juarendra/PocketMarauder/firmware/esp32_marauder/MenuFunctions.cpp

#include "MenuFunctions.h"
#include "MenuMarquee.h"
#include "CommandLine.h"
#include "OwnedListLifecycle.h"
#include "lang_var.h"

#ifdef HAS_SCREEN

extern const unsigned char menu_icons[][66];
extern LinkedList<AccessPoint>* access_points;
extern LinkedList<Station>* stations;
extern LinkedList<AirTag>* airtags;
extern LinkedList<Flipper>* flippers;
extern LinkedList<BleDevice>* ble_devices;
extern CommandLine cli_obj;

namespace {
bool parseGeofenceNumber(const String& value, double& parsed) {
  char* end = nullptr;
  parsed = strtod(value.c_str(), &end);
  return end != value.c_str() && *end == '\0' && isfinite(parsed);
}
}

#ifdef HAS_MINI_SCREEN
void MenuFunctions::drawMiniMenuButton(int b, int x, bool selected, uint16_t text_offset) {
  if (!current_menu || !current_menu->list || x < 0 || x >= current_menu->list->size())
    return;

  MenuNode mini_node = current_menu->list->get(x);
  bool is_setting_node = (mini_node.icon == SETTINGS && mini_node.color == TFTLIGHTGREY);
  uint16_t color = is_setting_node ? (mini_node.selected ? TFT_GREEN : TFT_RED) : this->getColor(mini_node.color);
  int16_t button_x = KEY_X - (KEY_W / 2);
  int16_t button_y = (KEY_Y + (b * (KEY_H + KEY_SPACING_Y))) - (KEY_H / 2);

  uint16_t background = selected ? (is_setting_node ? TFT_LIGHTGREY : color) : TFT_BLACK;
  uint16_t text_color = (selected && !is_setting_node) ? TFT_BLACK : color;

  display_obj.tft.setFreeFont(NULL);
  display_obj.tft.setTextSize(1);
  display_obj.tft.setTextWrap(false);
  display_obj.tft.fillRect(button_x, button_y - 4, KEY_W, KEY_H, background);
  display_obj.tft.setTextColor(text_color, background);
  display_obj.tft.setCursor(button_x + BUTTON_PADDING, button_y + (KEY_H / 2) - 8);
  display_obj.tft.print(this->menuLabelWindow(current_menu->list->get(x).name, text_offset));
}
#endif

String MenuFunctions::menuLabelWindow(const String& name, uint16_t offset) {
  const int16_t available_width = max(1, KEY_W - (2 * BUTTON_PADDING));

  #ifdef HAS_MINI_SCREEN
    display_obj.tft.setFreeFont(NULL);
    display_obj.tft.setTextSize(1);
  #else
    display_obj.tft.setFreeFont(MENU_FONT);
    display_obj.tft.setTextSize(KEY_TEXTSIZE);
  #endif

  if (offset >= name.length())
    offset = 0;

  String visible = name.substring(offset);
  while (visible.length() > 1 && display_obj.tft.textWidth(visible) > available_width)
    visible.remove(visible.length() - 1);

  return visible;
}

uint16_t MenuFunctions::menuLabelMaxOffset(const String& name) {
  const int16_t available_width = max(1, KEY_W - (2 * BUTTON_PADDING));
  uint16_t max_offset = 0;

  #ifdef HAS_MINI_SCREEN
    display_obj.tft.setFreeFont(NULL);
    display_obj.tft.setTextSize(1);
  #else
    display_obj.tft.setFreeFont(MENU_FONT);
    display_obj.tft.setTextSize(KEY_TEXTSIZE);
  #endif

  if (display_obj.tft.textWidth(name) > available_width) {
    max_offset = name.length() > 0 ? name.length() - 1 : 0;
    for (uint16_t offset = 1; offset < name.length(); offset++) {
      if (display_obj.tft.textWidth(name.substring(offset)) <= available_width) {
        max_offset = offset;
        break;
      }
    }
  }

  #ifdef HAS_FULL_SCREEN
    display_obj.tft.setFreeFont(NULL);
  #endif

  return max_offset;
}

void MenuFunctions::updateMenuMarquee(uint32_t current_time) {
  const bool menu_visible = (wifi_scan_obj.currentScanMode == WIFI_SCAN_OFF) ||
                            (wifi_scan_obj.currentScanMode == WIFI_CONNECTED) ||
                            (wifi_scan_obj.currentScanMode == OTA_UPDATE);

  if (!menu_visible || !current_menu || !current_menu->list ||
      current_menu->list->size() == 0 || current_menu->selected >= current_menu->list->size()) {
    marquee_menu = nullptr;
    marquee_selected = 0xFFFF;
    marquee_rendered_offset = 0;
    marquee_max_offset = 0;
    return;
  }

  if (marquee_menu != current_menu || marquee_selected != current_menu->selected) {
    marquee_menu = current_menu;
    marquee_selected = current_menu->selected;
    marquee_selected_since = current_time;
    marquee_rendered_offset = 0;
    marquee_max_offset = this->menuLabelMaxOffset(
      current_menu->list->get(current_menu->selected).name
    );
    return;
  }

  const uint16_t next_offset = MenuMarquee::offsetForElapsed(
    current_time - marquee_selected_since,
    marquee_max_offset
  );

  if (next_offset == marquee_rendered_offset)
    return;

  marquee_rendered_offset = next_offset;
  this->buttonSelected(
    current_menu->selected - menu_start_index,
    current_menu->selected,
    marquee_rendered_offset
  );
}

void MenuFunctions::buttonNotSelected(int b, int x) {
  if (x == -1)
    x = b;

  // Ensure b is within valid button index range
  b = (x - menu_start_index) % BUTTON_SCREEN_LIMIT;

  #ifdef HAS_MINI_SCREEN
    this->drawMiniMenuButton(b, x, false);
  #endif

  uint16_t color = (current_menu->list->get(x).icon == SETTINGS && current_menu->list->get(x).color == TFTLIGHTGREY) ? (current_menu->list->get(x).selected ? TFT_GREEN : TFT_RED) : this->getColor(current_menu->list->get(x).color);
  uint16_t icon_color = (current_menu->list->get(x).icon == SETTINGS && current_menu->list->get(x).color == TFTLIGHTGREY) ? TFT_LIGHTGREY : color;

  #ifdef HAS_FULL_SCREEN
    display_obj.tft.setFreeFont(MENU_FONT);
    display_obj.key[b].initButton(&display_obj.tft, KEY_X, KEY_Y + b * (KEY_H + KEY_SPACING_Y), KEY_W, KEY_H, TFT_BLACK, TFT_BLACK, color, (char*)"", KEY_TEXTSIZE);
    display_obj.key[b].drawButton(false, this->menuLabelWindow(current_menu->list->get(x).name));
    if ((current_menu->list->get(x).name != text09) && (current_menu->list->get(x).icon != 255))
          display_obj.tft.drawXBitmap(0,
                                      KEY_Y + (b * (KEY_H + KEY_SPACING_Y)) - (ICON_H / 2),
                                      menu_icons[current_menu->list->get(x).icon],
                                      ICON_W,
                                      ICON_H,
                                      TFT_BLACK,
                                      icon_color);
    display_obj.tft.setFreeFont(NULL);
  #endif
}

void MenuFunctions::buttonSelected(int b, int x, uint16_t text_offset) {
  if (x == -1)
    x = b;

  // Ensure b is within valid button index range
  b = (x - menu_start_index) % BUTTON_SCREEN_LIMIT;

  uint16_t color = this->getColor(current_menu->list->get(x).color);

  #ifdef HAS_MINI_SCREEN
    this->drawMiniMenuButton(b, x, true, text_offset);
  #endif

  #ifdef HAS_FULL_SCREEN
    display_obj.tft.setFreeFont(MENU_FONT);
    if (current_menu->list->get(x).icon == SETTINGS && current_menu->list->get(x).color == TFTLIGHTGREY) {
      uint16_t setting_color = current_menu->list->get(x).selected ? TFT_GREEN : TFT_RED;
      display_obj.key[b].initButton(&display_obj.tft, KEY_X, KEY_Y + b * (KEY_H + KEY_SPACING_Y), KEY_W, KEY_H, TFT_BLACK, TFT_LIGHTGREY, setting_color, (char*)"", KEY_TEXTSIZE);
      display_obj.key[b].drawButton(false, this->menuLabelWindow(current_menu->list->get(x).name, text_offset));
      display_obj.tft.drawXBitmap(0,
                                      KEY_Y + (b * (KEY_H + KEY_SPACING_Y)) - (ICON_H / 2),
                                      menu_icons[current_menu->list->get(x).icon],
                                      ICON_W,
                                      ICON_H,
                                      TFT_BLACK,
                                      TFT_LIGHTGREY);
    } else {
      display_obj.key[b].drawButton(true, this->menuLabelWindow(current_menu->list->get(x).name, text_offset));
      if ((current_menu->list->get(x).name != text09) && (current_menu->list->get(x).icon != 255))
            display_obj.tft.drawXBitmap(0,
                                        KEY_Y + (b * (KEY_H + KEY_SPACING_Y)) - (ICON_H / 2),
                                        menu_icons[current_menu->list->get(x).icon],
                                        ICON_W,
                                        ICON_H,
                                        TFT_BLACK,
                                        color);
    }
    display_obj.tft.setFreeFont(NULL);
  #endif
}

void MenuFunctions::displayMenuButtons() {
  #ifdef HAS_ILI9341
    // Draw lines to show each menu button
    for (int i = 0; i < 3; i++) {

      // Draw horizontal line on left
      display_obj.tft.drawLine(0, 
                              TFT_HEIGHT / 3 * (i),
                              (TFT_WIDTH / 12) / 2,
                              TFT_HEIGHT / 3 * (i),
                              TFT_FARTGRAY);

      // Draw horizontal line on right
      display_obj.tft.drawLine(TFT_WIDTH - 1 - ((TFT_WIDTH / 12) / 2), 
                              TFT_HEIGHT / 3 * (i),
                              TFT_WIDTH,
                              TFT_HEIGHT / 3 * (i),
                              TFT_FARTGRAY);

      // Draw vertical line on left
      display_obj.tft.drawLine(0, 
                              (TFT_HEIGHT / 3 * (i)) - ((TFT_WIDTH / 12) / 2),
                              0,
                              (TFT_HEIGHT / 3 * (i)) + ((TFT_WIDTH / 12) / 2),
                              TFT_FARTGRAY);

      // Draw vertical line on right
      display_obj.tft.drawLine(TFT_WIDTH - 1, 
                              (TFT_HEIGHT / 3 * (i)) - ((TFT_WIDTH / 12) / 2),
                              TFT_WIDTH - 1,
                              (TFT_HEIGHT / 3 * (i)) + ((TFT_WIDTH / 12) / 2),
                              TFT_FARTGRAY);
    }
  #endif
}

// Function to check menu input
void MenuFunctions::main(uint32_t currentTime)
{
  #ifdef HAS_MINI_SCREEN
    if (geofenceMenuRefreshPending) {
      geofenceMenuRefreshPending = false;
      this->buildGeofenceMenu();
    }
  #endif
  #ifdef HAS_SD
    if (sd_browser_release_pending && current_menu != &sdDeleteMenu)
      this->releaseSDDeleteBrowserResources();
  #endif
  if (saved_wifi_release_pending && current_menu != &savedWifiMenu) {
    this->releaseSavedWifiMenu();
    saved_wifi_release_pending = false;
  }

  #if defined(MARAUDER_CARDPUTER) || defined(MARAUDER_CARDPUTER_ADV)
    this->updateKeyboard();
  #endif

  // Some function exited and we need to go back to normal
  if (display_obj.exit_draw) {
    if (wifi_scan_obj.currentScanMode != WIFI_CONNECTED)
      wifi_scan_obj.currentScanMode = WIFI_SCAN_OFF;
    display_obj.exit_draw = false;
    this->orientDisplay();
  }
  if ((wifi_scan_obj.currentScanMode == WIFI_SCAN_OFF) ||
      (wifi_scan_obj.currentScanMode == WIFI_CONNECTED) ||
      (wifi_scan_obj.currentScanMode == OTA_UPDATE) ||
      (wifi_scan_obj.currentScanMode == ESP_UPDATE) ||
      (wifi_scan_obj.currentScanMode == SHOW_INFO) ||
      (wifi_scan_obj.currentScanMode == WIFI_SCAN_GPS_DATA) ||
      (wifi_scan_obj.currentScanMode == GPS_POI) ||
      (wifi_scan_obj.currentScanMode == GPS_TRACKER) ||
      (wifi_scan_obj.currentScanMode == WIFI_SCAN_GPS_NMEA)) {
    if (wifi_scan_obj.orient_display) {
      this->orientDisplay();
      wifi_scan_obj.orient_display = false;
    }
  }

  if (currentTime != 0) {
    if (currentTime - initTime >= BANNER_TIME) {
      this->initTime = millis();
      if ((wifi_scan_obj.currentScanMode != LV_JOIN_WIFI) &&
          (wifi_scan_obj.currentScanMode != LV_ADD_SSID) && (wifi_scan_obj.currentScanMode != WIFI_PACKET_MONITOR)) // GCOVR_EXCL_LINE -- Packet Monitor owns its full hardware display.
        this->updateStatusBar();
      
      // Do channel analyzer stuff
      if ((wifi_scan_obj.currentScanMode == WIFI_SCAN_CHAN_ANALYZER) ||
          (wifi_scan_obj.currentScanMode == BT_SCAN_ANALYZER)){
        #ifdef HAS_SCREEN
          this->setGraphScale(this->graphScaleCheck(wifi_scan_obj._analyzer_values));

          this->drawGraph(wifi_scan_obj._analyzer_values);
        #endif
      }

      if (wifi_scan_obj.currentScanMode == WIFI_SCAN_CHAN_ACT) {
        #ifdef HAS_SCREEN
          this->setGraphScale(this->graphScaleCheckSmall(wifi_scan_obj.channel_activity));

          this->drawGraphSmall(wifi_scan_obj.channel_activity);

        #endif
      }
    }
  }

  this->updateMenuMarquee(currentTime);


  boolean pressed = false;
  // This is code from bodmer's keypad example
  uint16_t t_x = 0, t_y = 0; // To store the touch coordinates

  // Get the display buffer out of the way
  if ((wifi_scan_obj.currentScanMode != WIFI_SCAN_OFF ) &&
      (wifi_scan_obj.currentScanMode != WIFI_CONNECTED) &&
      (wifi_scan_obj.currentScanMode != WIFI_ATTACK_BEACON_SPAM) &&
      (wifi_scan_obj.currentScanMode != WIFI_ATTACK_AP_SPAM) &&
      (wifi_scan_obj.currentScanMode != WIFI_ATTACK_CSA) &&
      (wifi_scan_obj.currentScanMode != WIFI_ATTACK_QUIET) &&
      (wifi_scan_obj.currentScanMode != WIFI_ATTACK_AUTH) &&
      (wifi_scan_obj.currentScanMode != WIFI_ATTACK_DEAUTH) &&
      (wifi_scan_obj.currentScanMode != WIFI_ATTACK_DEAUTH_MANUAL) &&
      (wifi_scan_obj.currentScanMode != WIFI_ATTACK_DEAUTH_TARGETED) &&
      (wifi_scan_obj.currentScanMode != WIFI_ATTACK_BAD_MSG_TARGETED) &&
      (wifi_scan_obj.currentScanMode != WIFI_ATTACK_BAD_MSG) &&
      (wifi_scan_obj.currentScanMode != WIFI_ATTACK_SLEEP) &&
      (wifi_scan_obj.currentScanMode != WIFI_ATTACK_SLEEP_TARGETED) &&
      (wifi_scan_obj.currentScanMode != WIFI_ATTACK_MIMIC) &&
	  (wifi_scan_obj.currentScanMode != WIFI_ATTACK_FUNNY_BEACON) &&
      (wifi_scan_obj.currentScanMode != WIFI_ATTACK_RICK_ROLL))
    display_obj.displayBuffer();


  int pre_getTouch = millis();

  #ifdef HAS_ILI9341
    if (!this->disable_touch)
      pressed = display_obj.updateTouch(&t_x, &t_y);
  #endif


  // Brightness gesture: hold top or bottom zone 1.5s to enter brightness mode
  #ifdef HAS_ILI9341
    bool touching_menu_control = false;
    if (pressed) {
      for (uint8_t b = BUTTON_ARRAY_LEN; b < BUTTON_ARRAY_LEN + 3; b++) {
        if (display_obj.key[b].contains(t_x, t_y)) {
          touching_menu_control = true;
          break;
        }
      }
    }
    if (pressed && !touching_menu_control &&
        (wifi_scan_obj.currentScanMode == WIFI_SCAN_OFF ||
                    wifi_scan_obj.currentScanMode == WIFI_CONNECTED)) {
      uint16_t zoneUp = TFT_HEIGHT * 25 / 100;
      uint16_t zoneDown = TFT_HEIGHT * 75 / 100;
      if (t_y < zoneUp || t_y >= zoneDown) {
        uint32_t hold_start = millis();
        uint16_t hx, hy;
        bool held = false;
        while (display_obj.updateTouch(&hx, &hy)) {
          if (millis() - hold_start >= 1500) {
            held = true;
            break;
          }
          delay(10);
        }
        if (held) {
          // Wait for release before entering brightness mode
          while (display_obj.updateTouch(&hx, &hy)) delay(10);
          this->brightnessMode();
          return;
        }
      }
    }
  #endif

  // POI button interception during wardrive — full width bottom bar
  #ifdef HAS_ILI9341
    if (pressed &&
        (wifi_scan_obj.currentScanMode == WIFI_SCAN_WAR_DRIVE ||
         wifi_scan_obj.currentScanMode == WIFI_SCAN_STATION_WAR_DRIVE)) {
      if (t_y >= (SCREEN_HEIGHT - 50)) {
        wifi_scan_obj.tagPOI(nullptr);
        // Brief green flash
        display_obj.tft.fillRect(0, SCREEN_HEIGHT - 50, SCREEN_WIDTH, 50, TFT_GREEN);
        display_obj.tft.setTextSize(2);
        #ifdef HAS_GPS
        if (gps_obj.getFixStatus())
          display_obj.tft.setTextColor(TFT_BLACK, TFT_GREEN);
        else
        #endif
          display_obj.tft.setTextColor(TFT_BLACK, TFT_RED);
        String poiFlash = "POI (" + String(wifi_scan_obj.poiCount) + ")";
        int16_t flashWidth = poiFlash.length() * 12;
        display_obj.tft.setCursor((SCREEN_WIDTH - flashWidth) / 2, SCREEN_HEIGHT - 33);
        display_obj.tft.print(poiFlash);
        delay(200);
        x = -1;
        y = -1;
        return;
      }
    }
  #endif

  // This is if there are scans/attacks going on
  #ifdef HAS_ILI9341
    if ((wifi_scan_obj.currentScanMode != WIFI_SCAN_OFF) &&
        (pressed) &&
        (wifi_scan_obj.currentScanMode != WIFI_CONNECTED) &&
        (wifi_scan_obj.currentScanMode != OTA_UPDATE) &&
        (wifi_scan_obj.currentScanMode != ESP_UPDATE) &&
        (wifi_scan_obj.currentScanMode != SHOW_INFO) &&
        (wifi_scan_obj.currentScanMode != WIFI_SCAN_GPS_DATA) &&
        (wifi_scan_obj.currentScanMode != GPS_POI) &&
        (wifi_scan_obj.currentScanMode != GPS_TRACKER) &&
        (wifi_scan_obj.currentScanMode != WIFI_SCAN_GPS_NMEA))
    {
      // Stop the current scan
      if ((wifi_scan_obj.currentScanMode == WIFI_SCAN_SAE_COMMIT) ||
          (wifi_scan_obj.currentScanMode == WIFI_SCAN_DETECT_FOLLOW) ||
          (wifi_scan_obj.currentScanMode == WIFI_SCAN_STATION_WAR_DRIVE) ||
          (wifi_scan_obj.currentScanMode == WIFI_SCAN_STATION) ||
          (wifi_scan_obj.currentScanMode == WIFI_SCAN_WAR_DRIVE) ||
          (wifi_scan_obj.currentScanMode == WIFI_SCAN_DISPLAY_AP_INFO) ||
          (wifi_scan_obj.currentScanMode == WIFI_SCAN_EVIL_PORTAL) ||
          (wifi_scan_obj.currentScanMode == WIFI_SCAN_AP_STA) ||
          (wifi_scan_obj.currentScanMode == WIFI_PING_SCAN) ||
          (wifi_scan_obj.currentScanMode == WIFI_ARP_SCAN) ||
          (wifi_scan_obj.currentScanMode == WIFI_PORT_SCAN_ALL) ||
          (wifi_scan_obj.currentScanMode == WIFI_SCAN_SSH) ||
          (wifi_scan_obj.currentScanMode == WIFI_SCAN_TELNET) ||
          (wifi_scan_obj.currentScanMode == WIFI_SCAN_DNS) ||
          (wifi_scan_obj.currentScanMode == WIFI_SCAN_SMTP) ||
          (wifi_scan_obj.currentScanMode == WIFI_SCAN_HTTP) ||
          (wifi_scan_obj.currentScanMode == WIFI_SCAN_HTTPS) ||
          (wifi_scan_obj.currentScanMode == WIFI_SCAN_RDP) ||
          (wifi_scan_obj.currentScanMode == WIFI_SCAN_PWN) ||
          (wifi_scan_obj.currentScanMode == WIFI_SCAN_PINESCAN) ||
          (wifi_scan_obj.currentScanMode == WIFI_SCAN_MULTISSID) ||
          (wifi_scan_obj.currentScanMode == WIFI_SCAN_ESPRESSIF) ||
          (wifi_scan_obj.currentScanMode == WIFI_SCAN_ALL) ||
          (wifi_scan_obj.currentScanMode == WIFI_ATTACK_BEACON_SPAM) ||
          (wifi_scan_obj.currentScanMode == WIFI_ATTACK_AP_SPAM) ||
          (wifi_scan_obj.currentScanMode == WIFI_ATTACK_CSA) ||
          (wifi_scan_obj.currentScanMode == WIFI_ATTACK_QUIET) ||
          (wifi_scan_obj.currentScanMode == WIFI_ATTACK_AUTH) ||
          (wifi_scan_obj.currentScanMode == WIFI_ATTACK_DEAUTH) ||
          (wifi_scan_obj.currentScanMode == WIFI_ATTACK_DEAUTH_MANUAL) ||
          (wifi_scan_obj.currentScanMode == WIFI_ATTACK_DEAUTH_TARGETED) ||
          (wifi_scan_obj.currentScanMode == WIFI_ATTACK_BAD_MSG_TARGETED) ||
          (wifi_scan_obj.currentScanMode == WIFI_ATTACK_BAD_MSG) ||
          (wifi_scan_obj.currentScanMode == WIFI_ATTACK_SLEEP) ||
          (wifi_scan_obj.currentScanMode == WIFI_ATTACK_SLEEP_TARGETED) ||
          (wifi_scan_obj.currentScanMode == WIFI_ATTACK_SAE_COMMIT) ||
          (wifi_scan_obj.currentScanMode == WIFI_ATTACK_MIMIC) ||
		      (wifi_scan_obj.currentScanMode == WIFI_ATTACK_FUNNY_BEACON) ||
          (wifi_scan_obj.currentScanMode == WIFI_ATTACK_RICK_ROLL) ||
          (wifi_scan_obj.currentScanMode == WIFI_ATTACK_BEACON_LIST) ||
          (wifi_scan_obj.currentScanMode == BT_SCAN_ALL) ||
          (wifi_scan_obj.currentScanMode == BT_SCAN_FOX_HUNT) ||
          (wifi_scan_obj.currentScanMode == WIFI_SCAN_SIG_STREN) ||
          (wifi_scan_obj.currentScanMode == BT_ATTACK_FINDMY_LIVE) ||
          (wifi_scan_obj.currentScanMode == BT_SCAN_RAYBAN) ||
          (wifi_scan_obj.currentScanMode == BT_SCAN_AIRTAG) ||
          (wifi_scan_obj.currentScanMode == BT_SCAN_AIRTAG_MON) ||
          (wifi_scan_obj.currentScanMode == BT_SCAN_FLIPPER) ||
          (wifi_scan_obj.currentScanMode == BT_SCAN_SIMPLE) ||
          (wifi_scan_obj.currentScanMode == BT_SCAN_SIMPLE_TWO) ||
          (wifi_scan_obj.currentScanMode == BT_ATTACK_SOUR_APPLE) ||
          (wifi_scan_obj.currentScanMode == BT_ATTACK_APPLE_JUICE) ||
          (wifi_scan_obj.currentScanMode == BT_ATTACK_SWIFTPAIR_SPAM) ||
          (wifi_scan_obj.currentScanMode == BT_ATTACK_SPAM_ALL) ||
          (wifi_scan_obj.currentScanMode == BT_ATTACK_SAMSUNG_SPAM) ||
          (wifi_scan_obj.currentScanMode == BT_ATTACK_GOOGLE_SPAM) ||
          (wifi_scan_obj.currentScanMode == BT_ATTACK_FLIPPER_SPAM) ||
          (wifi_scan_obj.currentScanMode == BT_SPOOF_AIRTAG) ||
          (wifi_scan_obj.currentScanMode == BT_SCAN_WAR_DRIVE) ||
          (wifi_scan_obj.currentScanMode == BT_SCAN_WAR_DRIVE_CONT) ||
          (wifi_scan_obj.currentScanMode == BT_SCAN_SKIMMERS) ||
          (wifi_scan_obj.currentScanMode == BT_SCAN_ANALYZER))
      {
        wifi_scan_obj.StartScan(WIFI_SCAN_OFF);
  
        // If we don't do this, the text and button coordinates will be off
        display_obj.init();
  
        // Take us back to the menu
        changeMenu(current_menu, true);
      }
  
      x = -1;
      y = -1;
  
      return;
    }
  #endif

  #ifdef HAS_BUTTONS

    #if (C_BTN >= 0) && !defined(MARAUDER_CARDPUTER) && !defined(MARAUDER_CARDPUTER_ADV)
      bool c_btn_press = c_btn.justPressed();
    #elif defined(MARAUDER_CARDPUTER) || defined(MARAUDER_CARDPUTER_ADV)
      bool c_btn_press = this->isKeyPressed('(');
    #endif

    #ifndef HAS_ILI9341
    
      if ((c_btn_press) &&
          (wifi_scan_obj.currentScanMode != WIFI_SCAN_OFF) &&
          (wifi_scan_obj.currentScanMode != WIFI_CONNECTED) &&
          (wifi_scan_obj.currentScanMode != OTA_UPDATE) &&
          (wifi_scan_obj.currentScanMode != ESP_UPDATE) &&
          (wifi_scan_obj.currentScanMode != SHOW_INFO) &&
          (wifi_scan_obj.currentScanMode != WIFI_SCAN_GPS_DATA) &&
          (wifi_scan_obj.currentScanMode != GPS_POI) &&
          (wifi_scan_obj.currentScanMode != GPS_TRACKER) &&
          (wifi_scan_obj.currentScanMode != WIFI_SCAN_GPS_NMEA))
      {
        // Stop the current scan
        if ((wifi_scan_obj.currentScanMode == WIFI_SCAN_PROBE) ||
            (wifi_scan_obj.currentScanMode == WIFI_SCAN_SAE_COMMIT) ||
            (wifi_scan_obj.currentScanMode == WIFI_SCAN_DETECT_FOLLOW) ||
            (wifi_scan_obj.currentScanMode == WIFI_SCAN_STATION_WAR_DRIVE) ||
            (wifi_scan_obj.currentScanMode == WIFI_SCAN_RAW_CAPTURE) ||
            (wifi_scan_obj.currentScanMode == WIFI_SCAN_STATION) ||
            (wifi_scan_obj.currentScanMode == WIFI_SCAN_AP) ||
            (wifi_scan_obj.currentScanMode == WIFI_SCAN_WAR_DRIVE) ||
            (wifi_scan_obj.currentScanMode == WIFI_SCAN_DISPLAY_AP_INFO) ||
            (wifi_scan_obj.currentScanMode == WIFI_SCAN_EVIL_PORTAL) ||
            (wifi_scan_obj.currentScanMode == WIFI_SCAN_SIG_STREN) ||
            (wifi_scan_obj.currentScanMode == BT_ATTACK_FINDMY_LIVE) ||
            (wifi_scan_obj.currentScanMode == WIFI_SCAN_AP_STA) ||
            (wifi_scan_obj.currentScanMode == WIFI_PING_SCAN) ||
            (wifi_scan_obj.currentScanMode == WIFI_ARP_SCAN) ||
            (wifi_scan_obj.currentScanMode == WIFI_PORT_SCAN_ALL) ||
            (wifi_scan_obj.currentScanMode == WIFI_SCAN_SSH) ||
            (wifi_scan_obj.currentScanMode == WIFI_SCAN_TELNET) ||
            (wifi_scan_obj.currentScanMode == WIFI_SCAN_DNS) ||
            (wifi_scan_obj.currentScanMode == WIFI_SCAN_SMTP) ||
            (wifi_scan_obj.currentScanMode == WIFI_SCAN_HTTP) ||
            (wifi_scan_obj.currentScanMode == WIFI_SCAN_HTTPS) ||
            (wifi_scan_obj.currentScanMode == WIFI_SCAN_RDP) ||
            (wifi_scan_obj.currentScanMode == WIFI_SCAN_PWN) ||
            (wifi_scan_obj.currentScanMode == WIFI_SCAN_PINESCAN) ||
            (wifi_scan_obj.currentScanMode == WIFI_SCAN_MULTISSID) ||
            (wifi_scan_obj.currentScanMode == WIFI_SCAN_ESPRESSIF) ||
            (wifi_scan_obj.currentScanMode == WIFI_SCAN_ALL) ||
            (wifi_scan_obj.currentScanMode == WIFI_SCAN_DEAUTH) ||
            (wifi_scan_obj.currentScanMode == WIFI_ATTACK_BEACON_SPAM) ||
            (wifi_scan_obj.currentScanMode == WIFI_ATTACK_AP_SPAM) ||
            (wifi_scan_obj.currentScanMode == WIFI_ATTACK_CSA) ||
            (wifi_scan_obj.currentScanMode == WIFI_ATTACK_QUIET) ||
            (wifi_scan_obj.currentScanMode == WIFI_ATTACK_AUTH) ||
            (wifi_scan_obj.currentScanMode == WIFI_ATTACK_DEAUTH) ||
            (wifi_scan_obj.currentScanMode == WIFI_ATTACK_DEAUTH_MANUAL) ||
            (wifi_scan_obj.currentScanMode == WIFI_ATTACK_DEAUTH_TARGETED) ||
            (wifi_scan_obj.currentScanMode == WIFI_ATTACK_BAD_MSG_TARGETED) ||
            (wifi_scan_obj.currentScanMode == WIFI_ATTACK_BAD_MSG) ||
            (wifi_scan_obj.currentScanMode == WIFI_ATTACK_SLEEP) ||
            (wifi_scan_obj.currentScanMode == WIFI_ATTACK_SLEEP_TARGETED) ||
            (wifi_scan_obj.currentScanMode == WIFI_ATTACK_SAE_COMMIT) ||
            (wifi_scan_obj.currentScanMode == WIFI_ATTACK_MIMIC) ||
			      (wifi_scan_obj.currentScanMode == WIFI_ATTACK_FUNNY_BEACON) ||
            (wifi_scan_obj.currentScanMode == WIFI_ATTACK_RICK_ROLL) ||
            (wifi_scan_obj.currentScanMode == WIFI_ATTACK_BEACON_LIST) ||
            (wifi_scan_obj.currentScanMode == BT_SCAN_ALL) ||
            (wifi_scan_obj.currentScanMode == BT_SCAN_FOX_HUNT) ||
            (wifi_scan_obj.currentScanMode == BT_SCAN_RAYBAN) ||
            (wifi_scan_obj.currentScanMode == BT_SCAN_AIRTAG) ||
            (wifi_scan_obj.currentScanMode == BT_SCAN_AIRTAG_MON) ||
            (wifi_scan_obj.currentScanMode == BT_SCAN_FLIPPER) ||
            (wifi_scan_obj.currentScanMode == BT_SCAN_FLOCK) ||
            (wifi_scan_obj.currentScanMode == BT_SCAN_SIMPLE) ||
            (wifi_scan_obj.currentScanMode == BT_SCAN_SIMPLE_TWO) ||
            (wifi_scan_obj.currentScanMode == BT_ATTACK_SOUR_APPLE) ||
            (wifi_scan_obj.currentScanMode == BT_ATTACK_APPLE_JUICE) ||
            (wifi_scan_obj.currentScanMode == BT_ATTACK_SWIFTPAIR_SPAM) ||
            (wifi_scan_obj.currentScanMode == BT_ATTACK_SPAM_ALL) ||
            (wifi_scan_obj.currentScanMode == BT_ATTACK_SAMSUNG_SPAM) ||
            (wifi_scan_obj.currentScanMode == BT_ATTACK_GOOGLE_SPAM) ||
            (wifi_scan_obj.currentScanMode == BT_ATTACK_FLIPPER_SPAM) ||
            (wifi_scan_obj.currentScanMode == BT_SPOOF_AIRTAG) ||
            (wifi_scan_obj.currentScanMode == BT_SCAN_WAR_DRIVE) ||
            (wifi_scan_obj.currentScanMode == BT_SCAN_WAR_DRIVE_CONT) ||
            (wifi_scan_obj.currentScanMode == BT_SCAN_SKIMMERS) ||
            (wifi_scan_obj.currentScanMode == WIFI_SCAN_EAPOL) ||
            (wifi_scan_obj.currentScanMode == WIFI_SCAN_ACTIVE_EAPOL) ||
            (wifi_scan_obj.currentScanMode == WIFI_SCAN_ACTIVE_LIST_EAPOL) ||
            (wifi_scan_obj.currentScanMode == WIFI_PACKET_MONITOR) ||
            (wifi_scan_obj.currentScanMode == WIFI_SCAN_CHAN_ANALYZER) ||
            (wifi_scan_obj.currentScanMode == WIFI_SCAN_CHAN_ACT) ||
            (wifi_scan_obj.currentScanMode == WIFI_SCAN_PACKET_RATE) ||
            (wifi_scan_obj.currentScanMode == BT_SCAN_ANALYZER))
        {
          wifi_scan_obj.StartScan(WIFI_SCAN_OFF);

          // Restore display state without full reinit to avoid screen flash
          #if defined(MARAUDER_CARDPUTER) || defined(MARAUDER_CARDPUTER_ADV)
            display_obj.tft.setRotation(SCREEN_ORIENTATION);
            display_obj.clearScreen();
          #else
            display_obj.init();
          #endif

          // Take us back to the menu
          changeMenu(current_menu, true);
        }
    
        x = -1;
        y = -1;
    
        return;
      }
    #endif

  #endif


  // Check if any key coordinate boxes contain the touch coordinates
  // This is for when on a menu
  // Make sure to add certain scanning functions here or else
  // menu items will be selected while scans and attacks are running
  #ifdef HAS_ILI9341
    if ((wifi_scan_obj.currentScanMode != WIFI_ATTACK_BEACON_SPAM) &&
        (wifi_scan_obj.currentScanMode != WIFI_ATTACK_AP_SPAM) &&
        (wifi_scan_obj.currentScanMode != WIFI_ATTACK_CSA) &&
        (wifi_scan_obj.currentScanMode != WIFI_ATTACK_QUIET) &&
        (wifi_scan_obj.currentScanMode != WIFI_ATTACK_AUTH) &&
        (wifi_scan_obj.currentScanMode != WIFI_ATTACK_DEAUTH) &&
        (wifi_scan_obj.currentScanMode != WIFI_ATTACK_DEAUTH_MANUAL) &&
        (wifi_scan_obj.currentScanMode != WIFI_ATTACK_DEAUTH_TARGETED) &&
        (wifi_scan_obj.currentScanMode != WIFI_ATTACK_BAD_MSG_TARGETED) &&
        (wifi_scan_obj.currentScanMode != WIFI_ATTACK_BAD_MSG) &&
        (wifi_scan_obj.currentScanMode != WIFI_ATTACK_SLEEP) &&
        (wifi_scan_obj.currentScanMode != WIFI_ATTACK_SLEEP_TARGETED) &&
        (wifi_scan_obj.currentScanMode != WIFI_ATTACK_SAE_COMMIT) &&
        (wifi_scan_obj.currentScanMode != WIFI_ATTACK_MIMIC) &&
        (wifi_scan_obj.currentScanMode != WIFI_SCAN_PACKET_RATE) &&
        (wifi_scan_obj.currentScanMode != WIFI_SCAN_RAW_CAPTURE) &&
        (wifi_scan_obj.currentScanMode != WIFI_SCAN_CHAN_ANALYZER) &&
        (wifi_scan_obj.currentScanMode != WIFI_SCAN_CHAN_ACT) &&
        (wifi_scan_obj.currentScanMode != WIFI_SCAN_SIG_STREN) &&
        (wifi_scan_obj.currentScanMode != WIFI_SCAN_AP) &&
        (wifi_scan_obj.currentScanMode != BT_SCAN_FLOCK) &&
        (wifi_scan_obj.currentScanMode != WIFI_SCAN_PROBE) &&
        (wifi_scan_obj.currentScanMode != WIFI_SCAN_DEAUTH) &&
		    (wifi_scan_obj.currentScanMode != WIFI_ATTACK_FUNNY_BEACON) &&
        (wifi_scan_obj.currentScanMode != WIFI_SCAN_EAPOL) &&
        (wifi_scan_obj.currentScanMode != WIFI_ATTACK_RICK_ROLL))
    {
      // Need this to set all keys to false
      /*for (uint8_t b = 0; b < BUTTON_ARRAY_LEN; b++) {
        if (pressed && display_obj.key[b].contains(t_x, t_y)) {
          display_obj.key[b].press(true);  // tell the button it is pressed
        } else {
          display_obj.key[b].press(false);  // tell the button it is NOT pressed
        }
      }*/

      // Detect up, down, select
      int8_t menu_button;
      const bool menu_navigation_active =
          wifi_scan_obj.currentScanMode == WIFI_SCAN_OFF ||
          wifi_scan_obj.currentScanMode == WIFI_CONNECTED ||
          wifi_scan_obj.currentScanMode == OTA_UPDATE;
      if (menu_navigation_active) {
        const int8_t held_button =
            display_obj.menuButton(&t_x, &t_y, pressed, true);
        const int8_t released_button = menuTouchReleasedButton(
            menu_touch_button, held_button, pressed);
        menu_touch_button = held_button;
        const bool up_event = menu_up_repeat.update(
            held_button == UP_BUTTON, currentTime);
        const bool down_event = menu_down_repeat.update(
            held_button == DOWN_BUTTON, currentTime);
        menu_button = up_event ? UP_BUTTON :
                      down_event ? DOWN_BUTTON :
                      released_button == SELECT_BUTTON ? SELECT_BUTTON : -1;
      } else {
        menu_up_repeat.reset();
        menu_down_repeat.reset();
        menu_touch_button = -1;
        menu_button = display_obj.menuButton(&t_x, &t_y, pressed);
      }

      if (menu_button >= 0) {
        if (menu_button == UP_BUTTON) {
          if ((wifi_scan_obj.currentScanMode == WIFI_SCAN_OFF) ||
              (wifi_scan_obj.currentScanMode == WIFI_CONNECTED) ||
              (wifi_scan_obj.currentScanMode == OTA_UPDATE)) {
            if (current_menu->selected > 0) {
              current_menu->selected--;
              // Page up
              if (current_menu->selected < this->menu_start_index) {
                this->buildButtons(current_menu, current_menu->selected);
                this->displayCurrentMenu(current_menu->selected);
              }
              this->buttonSelected(current_menu->selected - this->menu_start_index, current_menu->selected);
              if (!current_menu->list->get(current_menu->selected + 1).selected || (current_menu->list->get(current_menu->selected + 1).icon == SETTINGS && current_menu->list->get(current_menu->selected + 1).color == TFTLIGHTGREY))
                this->buttonNotSelected(current_menu->selected + 1 - this->menu_start_index, current_menu->selected + 1);
            }
            // Loop to end
            else {
              current_menu->selected = current_menu->list->size() - 1;
              if (current_menu->selected >= BUTTON_SCREEN_LIMIT) {
                this->buildButtons(current_menu, current_menu->selected + 1 - BUTTON_SCREEN_LIMIT);
                this->displayCurrentMenu(current_menu->selected + 1 - BUTTON_SCREEN_LIMIT);
              }
              this->buttonSelected(current_menu->selected, current_menu->selected);
              if (!current_menu->list->get(0).selected || (current_menu->list->get(0).icon == SETTINGS && current_menu->list->get(0).color == TFTLIGHTGREY))
                this->buttonNotSelected(0, this->menu_start_index);
            }
          }
          else if ((wifi_scan_obj.currentScanMode == WIFI_PACKET_MONITOR) ||
                  (wifi_scan_obj.currentScanMode == WIFI_SCAN_EAPOL) ||
                  (wifi_scan_obj.currentScanMode == WIFI_SCAN_CHAN_ANALYZER) ||
                  (wifi_scan_obj.currentScanMode == WIFI_SCAN_PACKET_RATE) ||
                  (wifi_scan_obj.currentScanMode == WIFI_SCAN_RAW_CAPTURE) ||
                  (wifi_scan_obj.currentScanMode == WIFI_SCAN_AP) ||
                  (wifi_scan_obj.currentScanMode == BT_SCAN_FLOCK) ||
                  (wifi_scan_obj.currentScanMode == WIFI_SCAN_PROBE) ||
                  (wifi_scan_obj.currentScanMode == WIFI_SCAN_DEAUTH) ||
                  (wifi_scan_obj.currentScanMode == WIFI_SCAN_SIG_STREN)) {
            #ifndef HAS_DUAL_BAND
              if (wifi_scan_obj.set_channel < 14)
                wifi_scan_obj.changeChannel(wifi_scan_obj.set_channel + 1);
              else
                wifi_scan_obj.changeChannel(1);
            #else
              if (wifi_scan_obj.dual_band_channel_index < DUAL_BAND_CHANNELS - 1)
                wifi_scan_obj.dual_band_channel_index++;
              else
                wifi_scan_obj.dual_band_channel_index = 0;

              wifi_scan_obj.changeChannel(wifi_scan_obj.dual_band_channels[wifi_scan_obj.dual_band_channel_index]);
            #endif
          }
          else if (wifi_scan_obj.currentScanMode == WIFI_SCAN_CHAN_ACT) {
            #ifndef HAS_DUAL_BAND
              if (wifi_scan_obj.activity_page < MAX_CHANNEL / CHAN_PER_PAGE) {
                wifi_scan_obj.activity_page++;
              }
            #else
              if (wifi_scan_obj.activity_page < DUAL_BAND_CHANNELS / CHAN_PER_PAGE) {
                wifi_scan_obj.activity_page++;
              }
            #endif
            wifi_scan_obj.drawChannelLine();
          }
        }
        if (menu_button == DOWN_BUTTON) {
          if ((wifi_scan_obj.currentScanMode == WIFI_SCAN_OFF) ||
              (wifi_scan_obj.currentScanMode == WIFI_CONNECTED) ||
              (wifi_scan_obj.currentScanMode == OTA_UPDATE)) {
            if (current_menu->selected < current_menu->list->size() - 1) {
              current_menu->selected++;
              // Page down
              if (current_menu->selected - this->menu_start_index >= BUTTON_SCREEN_LIMIT) {
                this->buildButtons(current_menu, current_menu->selected + 1 - BUTTON_SCREEN_LIMIT);
                this->displayCurrentMenu(current_menu->selected + 1 - BUTTON_SCREEN_LIMIT);
              }
              else
                this->buttonSelected(current_menu->selected - this->menu_start_index, current_menu->selected);
              if (!current_menu->list->get(current_menu->selected - 1).selected || (current_menu->list->get(current_menu->selected - 1).icon == SETTINGS && current_menu->list->get(current_menu->selected - 1).color == TFTLIGHTGREY))
                this->buttonNotSelected(current_menu->selected - 1 - this->menu_start_index, current_menu->selected - 1);
            }
            // Loop to beginning
            else {
              if (current_menu->selected >= BUTTON_SCREEN_LIMIT) {
                current_menu->selected = 0;
                this->buildButtons(current_menu);
                this->displayCurrentMenu();
                this->buttonSelected(current_menu->selected);
              }
              else {
                current_menu->selected = 0;
                this->buttonSelected(current_menu->selected);
                if (!current_menu->list->get(current_menu->list->size() - 1).selected || (current_menu->list->get(current_menu->list->size() - 1).icon == SETTINGS && current_menu->list->get(current_menu->list->size() - 1).color == TFTLIGHTGREY))
                  this->buttonNotSelected(current_menu->list->size() - 1);
              }
            }
          }
          else if ((wifi_scan_obj.currentScanMode == WIFI_PACKET_MONITOR) ||
                  (wifi_scan_obj.currentScanMode == WIFI_SCAN_EAPOL) ||
                  (wifi_scan_obj.currentScanMode == WIFI_SCAN_CHAN_ANALYZER) ||
                  (wifi_scan_obj.currentScanMode == WIFI_SCAN_PACKET_RATE) ||
                  (wifi_scan_obj.currentScanMode == WIFI_SCAN_RAW_CAPTURE) ||
                  (wifi_scan_obj.currentScanMode == WIFI_SCAN_AP) ||
                  (wifi_scan_obj.currentScanMode == BT_SCAN_FLOCK) ||
                  (wifi_scan_obj.currentScanMode == WIFI_SCAN_PROBE) ||
                  (wifi_scan_obj.currentScanMode == WIFI_SCAN_DEAUTH) ||
                  (wifi_scan_obj.currentScanMode == WIFI_SCAN_SIG_STREN)) {
            #ifndef HAS_DUAL_BAND
              if (wifi_scan_obj.set_channel > 1)
                wifi_scan_obj.changeChannel(wifi_scan_obj.set_channel - 1);
              else
                wifi_scan_obj.changeChannel(14);
            #else
              if (wifi_scan_obj.dual_band_channel_index > 0)
                wifi_scan_obj.dual_band_channel_index--;
              else
                wifi_scan_obj.dual_band_channel_index = DUAL_BAND_CHANNELS - 1;

              wifi_scan_obj.changeChannel(wifi_scan_obj.dual_band_channels[wifi_scan_obj.dual_band_channel_index]);
            #endif
          }
          else if (wifi_scan_obj.currentScanMode == WIFI_SCAN_CHAN_ACT) {
            #ifndef HAS_DUAL_BAND
              if (wifi_scan_obj.activity_page > 1) {
                wifi_scan_obj.activity_page--;
              }
            #else
              if (wifi_scan_obj.activity_page > 0) {
                wifi_scan_obj.activity_page--;
              }
            #endif
            wifi_scan_obj.drawChannelLine();
          }
        }
        if(menu_button == SELECT_BUTTON) {
          current_menu->list->get(current_menu->selected).callable();
        }
        else {
          if ((wifi_scan_obj.currentScanMode == WIFI_SCAN_OFF) ||
              (wifi_scan_obj.currentScanMode == WIFI_CONNECTED))
            this->displayMenuButtons();
        }
      }
    }
    x = -1;
    y = -1;
  #endif

  // Menu navigation and paging
  #ifdef HAS_BUTTONS
    // Don't do this for touch screens
    #if !(defined(MARAUDER_V6) || defined(MARAUDER_V6_1) || defined(MARAUDER_CYD_MICRO) || defined(MARAUDER_CYD_GUITION) || defined(MARAUDER_CYD_2USB) || defined(MARAUDER_CYD_3_5_INCH))
      #if !defined(MARAUDER_M5STICKC) || defined(MARAUDER_M5STICKCP2)
        #if (U_BTN >= 0 || defined(MARAUDER_CARDPUTER) || defined(MARAUDER_CARDPUTER_ADV))
          #if (U_BTN >= 0)
            const bool up_just_pressed = u_btn.justPressed();
            const bool up_is_pressed = u_btn.isPressedNow();
          #elif defined(MARAUDER_CARDPUTER) || defined(MARAUDER_CARDPUTER_ADV)
            const bool up_just_pressed = this->isKeyPressed(';');
            const bool up_is_pressed = up_just_pressed;
          #endif
            const bool menu_navigation_active =
                wifi_scan_obj.currentScanMode == WIFI_SCAN_OFF ||
                wifi_scan_obj.currentScanMode == WIFI_CONNECTED ||
                wifi_scan_obj.currentScanMode == OTA_UPDATE;
            const bool up_event = menu_navigation_active
                ? menu_up_repeat.update(up_is_pressed, currentTime)
                : up_just_pressed;
            if (!menu_navigation_active) menu_up_repeat.reset();
            if (up_event) {
              if ((wifi_scan_obj.currentScanMode == WIFI_SCAN_OFF) ||
                  (wifi_scan_obj.currentScanMode == WIFI_CONNECTED) ||
                  (wifi_scan_obj.currentScanMode == OTA_UPDATE)) {
                if (current_menu->selected > 0) {
                  current_menu->selected--;
                  // Page up
                  if (current_menu->selected < this->menu_start_index) {
                    this->buildButtons(current_menu, current_menu->selected);
                    this->displayCurrentMenu(current_menu->selected);
                  }
                  this->buttonSelected(current_menu->selected - this->menu_start_index, current_menu->selected);
                  if (!current_menu->list->get(current_menu->selected + 1).selected || (current_menu->list->get(current_menu->selected + 1).icon == SETTINGS && current_menu->list->get(current_menu->selected + 1).color == TFTLIGHTGREY))
                    this->buttonNotSelected(current_menu->selected + 1 - this->menu_start_index, current_menu->selected + 1);
                }
                // Loop to end
                else {
                  current_menu->selected = current_menu->list->size() - 1;
                  if (current_menu->selected >= BUTTON_SCREEN_LIMIT) {
                    this->buildButtons(current_menu, current_menu->selected + 1 - BUTTON_SCREEN_LIMIT);
                    this->displayCurrentMenu(current_menu->selected + 1 - BUTTON_SCREEN_LIMIT);
                  }
                  this->buttonSelected(current_menu->selected, current_menu->selected);
                  if (!current_menu->list->get(0).selected || (current_menu->list->get(0).icon == SETTINGS && current_menu->list->get(0).color == TFTLIGHTGREY))
                    this->buttonNotSelected(0, this->menu_start_index);
                }
              }
              else if ((wifi_scan_obj.currentScanMode == WIFI_PACKET_MONITOR) ||
                      (wifi_scan_obj.currentScanMode == WIFI_SCAN_EAPOL) ||
                      (wifi_scan_obj.currentScanMode == WIFI_SCAN_CHAN_ANALYZER) ||
                      (wifi_scan_obj.currentScanMode == WIFI_SCAN_PACKET_RATE) ||
                      (wifi_scan_obj.currentScanMode == WIFI_SCAN_RAW_CAPTURE) ||
                      (wifi_scan_obj.currentScanMode == WIFI_SCAN_AP) ||
                      (wifi_scan_obj.currentScanMode == BT_SCAN_FLOCK) ||
                      (wifi_scan_obj.currentScanMode == WIFI_SCAN_PROBE) ||
                      (wifi_scan_obj.currentScanMode == WIFI_SCAN_DEAUTH) ||
                      (wifi_scan_obj.currentScanMode == WIFI_SCAN_SIG_STREN)) {
                #ifndef HAS_DUAL_BAND
                  if (wifi_scan_obj.set_channel < 14)
                    wifi_scan_obj.changeChannel(wifi_scan_obj.set_channel + 1);
                  else
                    wifi_scan_obj.changeChannel(1);
                #else
                  if (wifi_scan_obj.dual_band_channel_index < DUAL_BAND_CHANNELS - 1)
                    wifi_scan_obj.dual_band_channel_index++;
                  else
                    wifi_scan_obj.dual_band_channel_index = 0;

                  wifi_scan_obj.changeChannel(wifi_scan_obj.dual_band_channels[wifi_scan_obj.dual_band_channel_index]);
                #endif
              }
              else if (wifi_scan_obj.currentScanMode == WIFI_SCAN_CHAN_ACT) {
                #ifndef HAS_DUAL_BAND
                  if (wifi_scan_obj.activity_page < MAX_CHANNEL / CHAN_PER_PAGE) {
                    wifi_scan_obj.activity_page++;
                  }
                #else
                  if (wifi_scan_obj.activity_page < DUAL_BAND_CHANNELS / CHAN_PER_PAGE) {
                    wifi_scan_obj.activity_page++;
                  }
                #endif
                wifi_scan_obj.drawChannelLine();
              }
            }
        #endif
      #endif

      #if (D_BTN >= 0 || defined(MARAUDER_CARDPUTER) || defined(MARAUDER_CARDPUTER_ADV))
      #if (D_BTN >= 0)
      const bool down_just_pressed = d_btn.justPressed();
      const bool down_is_pressed = d_btn.isPressedNow();
      #elif defined(MARAUDER_CARDPUTER) || defined(MARAUDER_CARDPUTER_ADV)
      const bool down_just_pressed = this->isKeyPressed('.');
      const bool down_is_pressed = down_just_pressed;
      #endif
      const bool down_menu_navigation_active =
          wifi_scan_obj.currentScanMode == WIFI_SCAN_OFF ||
          wifi_scan_obj.currentScanMode == WIFI_CONNECTED ||
          wifi_scan_obj.currentScanMode == OTA_UPDATE;
      const bool down_event = down_menu_navigation_active
          ? menu_down_repeat.update(down_is_pressed, currentTime)
          : down_just_pressed;
      if (!down_menu_navigation_active) menu_down_repeat.reset();
      if (down_event) {
        if ((wifi_scan_obj.currentScanMode == WIFI_SCAN_OFF) ||
            (wifi_scan_obj.currentScanMode == WIFI_CONNECTED) ||
            (wifi_scan_obj.currentScanMode == OTA_UPDATE)) {
          if (current_menu->selected < current_menu->list->size() - 1) {
            current_menu->selected++;
            // Page down
            if (current_menu->selected - this->menu_start_index >= BUTTON_SCREEN_LIMIT) {
              this->buildButtons(current_menu, current_menu->selected + 1 - BUTTON_SCREEN_LIMIT);
              this->displayCurrentMenu(current_menu->selected + 1 - BUTTON_SCREEN_LIMIT);
            }
            else
              this->buttonSelected(current_menu->selected - this->menu_start_index, current_menu->selected);
            if (!current_menu->list->get(current_menu->selected - 1).selected || (current_menu->list->get(current_menu->selected - 1).icon == SETTINGS && current_menu->list->get(current_menu->selected - 1).color == TFTLIGHTGREY))
              this->buttonNotSelected(current_menu->selected - 1 - this->menu_start_index, current_menu->selected - 1);
          }
          // Loop to beginning
          else {
            if (current_menu->selected >= BUTTON_SCREEN_LIMIT) {
              current_menu->selected = 0;
              this->buildButtons(current_menu);
              this->displayCurrentMenu();
              this->buttonSelected(current_menu->selected);
            }
            else {
              current_menu->selected = 0;
              this->buttonSelected(current_menu->selected);
              if (!current_menu->list->get(current_menu->list->size() - 1).selected || (current_menu->list->get(current_menu->list->size() - 1).icon == SETTINGS && current_menu->list->get(current_menu->list->size() - 1).color == TFTLIGHTGREY))
                this->buttonNotSelected(current_menu->list->size() - 1);
            }
          }
        }
        else if ((wifi_scan_obj.currentScanMode == WIFI_PACKET_MONITOR) ||
                (wifi_scan_obj.currentScanMode == WIFI_SCAN_EAPOL) ||
                (wifi_scan_obj.currentScanMode == WIFI_SCAN_CHAN_ANALYZER) ||
                (wifi_scan_obj.currentScanMode == WIFI_SCAN_PACKET_RATE) ||
                (wifi_scan_obj.currentScanMode == WIFI_SCAN_RAW_CAPTURE) ||
                (wifi_scan_obj.currentScanMode == WIFI_SCAN_AP) ||
                (wifi_scan_obj.currentScanMode == BT_SCAN_FLOCK) ||
                (wifi_scan_obj.currentScanMode == WIFI_SCAN_PROBE) ||
                (wifi_scan_obj.currentScanMode == WIFI_SCAN_DEAUTH) ||
                (wifi_scan_obj.currentScanMode == WIFI_SCAN_SIG_STREN)) {
          #ifndef HAS_DUAL_BAND
            if (wifi_scan_obj.set_channel > 1)
              wifi_scan_obj.changeChannel(wifi_scan_obj.set_channel - 1);
            else
              wifi_scan_obj.changeChannel(14);
          #else
            if (wifi_scan_obj.dual_band_channel_index > 0)
              wifi_scan_obj.dual_band_channel_index--;
            else
              wifi_scan_obj.dual_band_channel_index = DUAL_BAND_CHANNELS - 1;

            wifi_scan_obj.changeChannel(wifi_scan_obj.dual_band_channels[wifi_scan_obj.dual_band_channel_index]);
          #endif
        }
        else if (wifi_scan_obj.currentScanMode == WIFI_SCAN_CHAN_ACT) {
          #ifndef HAS_DUAL_BAND
            if (wifi_scan_obj.activity_page > 1) {
              wifi_scan_obj.activity_page--;
            }
          #else
            if (wifi_scan_obj.activity_page > 0) {
              wifi_scan_obj.activity_page--;
            }
          #endif
          wifi_scan_obj.drawChannelLine();
        }
      }
      #endif

      #if (R_BTN >= 0 || defined(MARAUDER_CARDPUTER) || defined(MARAUDER_CARDPUTER_ADV))
      #if (R_BTN >= 0)
      if (r_btn.justPressed()) {
      #elif defined(MARAUDER_CARDPUTER) || defined(MARAUDER_CARDPUTER_ADV)
      if (this->isKeyPressed('/')) {
      #endif
        if (wifi_scan_obj.currentScanMode == WIFI_SCAN_OFF) {
          #ifndef HAS_DUAL_BAND
            if (wifi_scan_obj.set_channel < 14)
              wifi_scan_obj.changeChannel(wifi_scan_obj.set_channel + 1);
            else
              wifi_scan_obj.changeChannel(1);
          #else
            if (wifi_scan_obj.dual_band_channel_index < DUAL_BAND_CHANNELS - 1)
              wifi_scan_obj.dual_band_channel_index++;
            else
              wifi_scan_obj.dual_band_channel_index = 0;

            wifi_scan_obj.changeChannel(wifi_scan_obj.dual_band_channels[wifi_scan_obj.dual_band_channel_index]);
          #endif
        }
      }
      #endif

      #if (L_BTN >= 0 || defined(MARAUDER_CARDPUTER) || defined(MARAUDER_CARDPUTER_ADV))
      #if (L_BTN >= 0)
      if (l_btn.justPressed()) {
      #elif defined(MARAUDER_CARDPUTER) || defined(MARAUDER_CARDPUTER_ADV)
      if (this->isKeyPressed(',')) {
      #endif
        if (wifi_scan_obj.currentScanMode == WIFI_SCAN_OFF) {
          #ifndef HAS_DUAL_BAND
            if (wifi_scan_obj.set_channel > 1)
              wifi_scan_obj.changeChannel(wifi_scan_obj.set_channel - 1);
            else
              wifi_scan_obj.changeChannel(14);
          #else
            if (wifi_scan_obj.dual_band_channel_index > 0)
              wifi_scan_obj.dual_band_channel_index--;
            else
              wifi_scan_obj.dual_band_channel_index = DUAL_BAND_CHANNELS - 1;

            wifi_scan_obj.changeChannel(wifi_scan_obj.dual_band_channels[wifi_scan_obj.dual_band_channel_index]);
          #endif
        }
      }
      #endif

      #if defined(MARAUDER_CARDPUTER) || defined(MARAUDER_CARDPUTER_ADV)
      if (this->isKeyPressed('`') || this->isKeyPressed(KEY_BACKSPACE)) {
        if (wifi_scan_obj.currentScanMode == WIFI_SCAN_OFF) {
          if (current_menu->parentMenu != NULL) {
            this->changeMenu(current_menu->parentMenu, true);
          }
        }
      }
      #endif

      if(c_btn_press){
        current_menu->list->get(current_menu->selected).callable();
      }

    #endif
  #endif
}

#if BATTERY_ANALOG_ON == 1
byte battery_analog_array[10];
byte battery_count = 0;
byte battery_analog_last = 101;
#define BATTERY_CHECK 50
uint16_t battery_analog = 0;
void MenuFunctions::battery(bool initial)
{
  if (BATTERY_ANALOG_ON) {
    uint8_t n = 0;
    byte battery_analog_sample[10];
    byte deviation;
    if (battery_count == BATTERY_CHECK - 5)  digitalWrite(BATTERY_PIN, HIGH);
    else if (battery_count == 5) digitalWrite(BATTERY_PIN, LOW);
    if (battery_count == 0) {
      battery_analog = 0;
      for (n = 9; n > 0; n--)battery_analog_array[n] = battery_analog_array[n - 1];
      for (n = 0; n < 10; n++) {
        battery_analog_sample[n] = map((analogRead(ANALOG_PIN) * 5), 2400, 4200, 0, 100);
        if (battery_analog_sample[n] > 100) battery_analog_sample[n] = 100;
        else if (battery_analog_sample[n] < 0) battery_analog_sample[n] = 0;
        battery_analog += battery_analog_sample[n];
      }
      battery_analog = battery_analog / 10;
      for (n = 0; n < 10; n++) {
        deviation = abs(battery_analog - battery_analog_sample[n]);
        if (deviation >= 10) battery_analog_sample[n] = battery_analog;
      }
      battery_analog = 0;
      for (n = 0; n < 10; n++) battery_analog += battery_analog_sample[n];
      battery_analog = battery_analog / 10;
      battery_analog_array[0] = battery_analog;
      if (battery_analog_array[9] > 0 ) {
        battery_analog = 0;
        for (n = 0; n < 10; n++) battery_analog += battery_analog_array[n];
        battery_analog = battery_analog / 10;
      }
      battery_count ++;
    }
    else if (battery_count < BATTERY_CHECK) battery_count++;
    else if (battery_count >= BATTERY_CHECK) battery_count = 0;

    if (battery_analog_last != battery_analog) {
      battery_analog_last = battery_analog;
      MenuFunctions::battery2();
    }
  }
}
void MenuFunctions::battery2(bool initial)
{
  uint16_t the_color;
  if ( digitalRead(CHARGING_PIN) == 1) the_color = TFT_BLUE;
  else if (battery_analog < 20) the_color = TFT_RED;
  else if (battery_analog < 40)  the_color = TFT_YELLOW;
  else the_color = TFT_GREEN;

  display_obj.tft.setTextColor(the_color, STATUSBAR_COLOR);
  display_obj.tft.fillRect(SB_TOUCH_X, 0, 50, STATUS_BAR_WIDTH, STATUSBAR_COLOR);
  display_obj.tft.drawXBitmap(SB_TOUCH_X,
                              0,
                              menu_icons[STATUS_BAT],
                              16,
                              16,
                              STATUSBAR_COLOR,
                              the_color);
  display_obj.tft.drawString((String) battery_analog + "%", SB_BAT_X, 0, 2);
}
#else
void MenuFunctions::battery(bool initial)
{
  #ifdef HAS_BATTERY
    uint16_t the_color;
    if (battery_obj.i2c_supported)
    {
      // Could use int compare maybe idk
      if (((String)battery_obj.battery_level != "25") && ((String)battery_obj.battery_level != "0"))
        the_color = TFT_GREEN;
      else
        the_color = TFT_RED;

      if ((battery_obj.battery_level != battery_obj.old_level) || (initial)) {
        battery_obj.old_level = battery_obj.battery_level;
        display_obj.tft.fillRect(204, 0, SCREEN_WIDTH, STATUS_BAR_WIDTH, STATUSBAR_COLOR);
      }

      display_obj.tft.setCursor(0, 1);
      /*if (!this->disable_touch) {
        display_obj.tft.drawXBitmap(SB_TOUCH_X,
                                    0,
                                    menu_icons[STATUS_BAT],
                                    16,
                                    16,
                                    STATUSBAR_COLOR,
                                    the_color);
      }*/
      #if defined(MARAUDER_CARDPUTER) || defined(MARAUDER_CARDPUTER_ADV)
        display_obj.tft.drawString((String)battery_obj.battery_level + "%", SB_BAT_X, 0, 1);
      #else
        display_obj.tft.drawString((String)battery_obj.battery_level + "%", SB_BAT_X, 0, 2);
      #endif
    }
  #endif
}
void MenuFunctions::battery2(bool initial)
{
  MenuFunctions::battery(initial);
}
#endif

void MenuFunctions::updateStatusBar()
{
  display_obj.tft.setTextSize(1);

  bool status_changed = false;
  
  #if defined(MARAUDER_MINI) || defined(MARAUDER_M5STICKC) || defined(MARAUDER_REV_FEATHER) || defined(MARAUDER_CARDPUTER) || defined(MARAUDER_CARDPUTER_ADV) || defined(MARAUDER_MINI_V3)
    display_obj.tft.setFreeFont(NULL);
  #endif

  uint16_t the_color; 

  #ifdef HAS_GPS
    if (this->old_gps_sat_count != gps_obj.getNumSats()) {
      this->old_gps_sat_count = gps_obj.getNumSats();
      display_obj.tft.fillRect(0, 0, SCREEN_WIDTH, STATUS_BAR_WIDTH, STATUSBAR_COLOR);
      status_changed = true;
    }
  #endif

  // GPS Stuff
  #ifdef HAS_GPS
    if (gps_obj.getGpsModuleStatus()) {
      if (gps_obj.getFixStatus())
        the_color = TFT_GREEN;
      else
        the_color = TFT_RED;
        
      #ifdef HAS_FULL_SCREEN
        display_obj.tft.drawXBitmap(4,
                                    0,
                                    menu_icons[STATUS_GPS],
                                    16,
                                    16,
                                    STATUSBAR_COLOR,
                                    the_color);
        display_obj.tft.setTextColor(TFT_WHITE, STATUSBAR_COLOR, true);

        display_obj.tft.drawString(gps_obj.getNumSatsString(), 22, 0, 2);
      #elif defined(HAS_SCREEN)
        display_obj.tft.setTextColor(the_color, STATUSBAR_COLOR, true);
        display_obj.tft.drawString("GPS", 0, 0, 1);
      #endif
    }
  #endif

  display_obj.tft.setTextColor(TFT_WHITE, STATUSBAR_COLOR, true);

  // WiFi Channel Stuff
  uint8_t primaryChannel;
  wifi_second_chan_t secondChannel;
  esp_err_t err = esp_wifi_get_channel(&primaryChannel, &secondChannel);

  uint8_t current_channel = wifi_scan_obj.set_channel;

  if (err == ESP_OK)
    current_channel = primaryChannel;

  if ((current_channel != wifi_scan_obj.old_channel) || (status_changed)) {
    wifi_scan_obj.old_channel = current_channel;
    #if defined(MARAUDER_MINI) || defined(MARAUDER_M5STICKC) || defined(MARAUDER_REV_FEATHER) || defined(MARAUDER_CARDPUTER) || defined(MARAUDER_CARDPUTER_ADV) || defined(MARAUDER_MINI_V3)
      display_obj.tft.fillRect(TFT_WIDTH/4, 0, CHAR_WIDTH * 6, STATUS_BAR_WIDTH, STATUSBAR_COLOR);
    #elif defined(HAS_DUAL_BAND)
      display_obj.tft.fillRect(50, 0, (CHAR_WIDTH / 2) * 8, STATUS_BAR_WIDTH, STATUSBAR_COLOR);
    #else
      display_obj.tft.fillRect(50, 0, (CHAR_WIDTH / 2) * 7, STATUS_BAR_WIDTH, STATUSBAR_COLOR);
    #endif
    #ifdef HAS_FULL_SCREEN
      display_obj.tft.drawString("CH: " + (String)wifi_scan_obj.old_channel, 50, 0, 2);
    #endif

    #ifdef HAS_MINI_SCREEN
      display_obj.tft.drawString("CH:" + (String)wifi_scan_obj.old_channel, TFT_WIDTH/4, 0, 1);
    #endif
  }

  // RAM Stuff
  wifi_scan_obj.free_ram = String(esp_get_free_heap_size());
  if ((wifi_scan_obj.free_ram != wifi_scan_obj.old_free_ram) || (status_changed)) {
    wifi_scan_obj.old_free_ram = wifi_scan_obj.free_ram;
    //display_obj.tft.fillRect(SB_MEM_X, 0, 60, STATUS_BAR_WIDTH, STATUSBAR_COLOR);
    #ifdef HAS_FULL_SCREEN
    #ifndef HAS_PSRAM
      display_obj.tft.drawString("D:" + String(getDRAMUsagePercent()) + "%", SB_MEM_X, 0, 2);
    #else
      display_obj.tft.drawString("D:" + String(getDRAMUsagePercent()) + "%", SB_MEM_X, 0, 1);
      display_obj.tft.drawString("P:" + String(getPSRAMUsagePercent()) + "%", SB_MEM_X, 8, 1);
    #endif
  #endif

  #ifdef HAS_MINI_SCREEN
    display_obj.tft.drawString(String(getDRAMUsagePercent()) + "%", TFT_WIDTH/1.75, 0, 1);
  #endif
  }

  // Draw battery info
  MenuFunctions::battery(false);
  display_obj.tft.fillRect(186, 0, 16, STATUS_BAR_WIDTH, STATUSBAR_COLOR);

  // Disable touch stuff
  #ifdef HAS_ILI9341
    #ifdef HAS_BUTTONS
      if (this->disable_touch) {
        display_obj.tft.setCursor(0, 1);
        display_obj.tft.drawXBitmap(SB_TOUCH_X,
                                    0,
                                    menu_icons[DISABLE_TOUCH],
                                    16,
                                    16,
                                    STATUSBAR_COLOR,
                                    TFT_RED);
      }
      else {
        display_obj.tft.setCursor(0, 1);
        display_obj.tft.drawXBitmap(SB_TOUCH_X,
                                    0,
                                    menu_icons[DISABLE_TOUCH],
                                    16,
                                    16,
                                    STATUSBAR_COLOR,
                                    TFT_DARKGREY);
      }
    #endif
  #endif

  // Draw SD info
  #ifdef HAS_SD
    if (sd_obj.supported)
      the_color = TFT_GREEN;
    else
      the_color = TFT_RED;

    #ifdef HAS_FULL_SCREEN
      display_obj.tft.drawXBitmap(SB_SD_X,
                                  0,
                                  menu_icons[STATUS_SD],
                                  16,
                                  16,
                                  STATUSBAR_COLOR,
                                  the_color);
    #endif
  #endif

  #ifdef HAS_MINI_SCREEN
    display_obj.tft.setTextColor(the_color, STATUSBAR_COLOR, true);
    display_obj.tft.drawString("SD", TFT_WIDTH - 12, 0, 1);
  #endif

  // WiFi connection status stuff
  if (wifi_scan_obj.wifi_connected) {
    #ifdef HAS_FULL_SCREEN
      display_obj.tft.drawXBitmap(SB_WIFI_X,
                                  0,
                                  menu_icons[JOINED],
                                  16,
                                  16,
                                  STATUSBAR_COLOR,
                                  TFT_GREEN);
    #endif
  } else {
    #ifdef HAS_FULL_SCREEN
      display_obj.tft.drawXBitmap(SB_WIFI_X,
                                  0,
                                  menu_icons[JOINED],
                                  16,
                                  16,
                                  STATUSBAR_COLOR,
                                  TFT_DARKGREY);
    #endif
  }

  // Force PMKID stuff
  if ((wifi_scan_obj.force_pmkid) || (wifi_scan_obj.ep_deauth)) {
    #ifdef HAS_FULL_SCREEN
      display_obj.tft.drawXBitmap(SB_FORCE_X,
                                  0,
                                  menu_icons[FORCE],
                                  16,
                                  16,
                                  STATUSBAR_COLOR,
                                  TFT_GREEN);
    #endif
  } else {
    #ifdef HAS_FULL_SCREEN
      display_obj.tft.drawXBitmap(SB_FORCE_X,
                                  0,
                                  menu_icons[FORCE],
                                  16,
                                  16,
                                  STATUSBAR_COLOR,
                                  TFT_DARKGREY);
    #endif
  }
}

void MenuFunctions::drawStatusBar()
{
  display_obj.tft.setTextSize(1);
  #ifdef HAS_MINI_SCREEN
    display_obj.tft.setFreeFont(NULL);
  #endif
  display_obj.tft.fillRect(0, 0, SCREEN_WIDTH, STATUS_BAR_WIDTH, STATUSBAR_COLOR);
  display_obj.tft.setTextColor(TFT_WHITE, STATUSBAR_COLOR);

  uint16_t the_color;

  // GPS Stuff
  #ifdef HAS_GPS
    if (gps_obj.getGpsModuleStatus()) {
      if (gps_obj.getFixStatus())
        the_color = TFT_GREEN;
      else
        the_color = TFT_RED;
        
      #ifdef HAS_FULL_SCREEN
        display_obj.tft.drawXBitmap(4,
                                    0,
                                    menu_icons[STATUS_GPS],
                                    16,
                                    16,
                                    STATUSBAR_COLOR,
                                    the_color);
        display_obj.tft.setTextColor(TFT_WHITE, STATUSBAR_COLOR);

        display_obj.tft.drawString(gps_obj.getNumSatsString(), 22, 0, 2);
      #endif
    }
  #endif

  display_obj.tft.setTextColor(TFT_WHITE, STATUSBAR_COLOR);


  // WiFi Channel Stuff
  uint8_t primaryChannel;
  wifi_second_chan_t secondChannel;
  esp_err_t err = esp_wifi_get_channel(&primaryChannel, &secondChannel);

  if (err == ESP_OK)
    wifi_scan_obj.old_channel = primaryChannel;
  else
    wifi_scan_obj.old_channel = wifi_scan_obj.set_channel;

  #ifdef HAS_MINI_SCREEN
    display_obj.tft.fillRect(43, 0, TFT_WIDTH * 0.21, STATUS_BAR_WIDTH, STATUSBAR_COLOR);
  #else
    display_obj.tft.fillRect(50, 0, TFT_WIDTH * 0.21, STATUS_BAR_WIDTH, STATUSBAR_COLOR);
  #endif
  #ifdef HAS_FULL_SCREEN
    display_obj.tft.drawString("CH: " + (String)wifi_scan_obj.old_channel, 50, 0, 2);
  #endif

  #ifdef HAS_MINI_SCREEN
    display_obj.tft.drawString("CH:" + (String)wifi_scan_obj.old_channel, TFT_WIDTH/4, 0, 1);
  #endif

  // RAM Stuff
  wifi_scan_obj.free_ram = String(esp_get_free_heap_size());
  wifi_scan_obj.old_free_ram = wifi_scan_obj.free_ram;
  display_obj.tft.fillRect(100, 0, 60, STATUS_BAR_WIDTH, STATUSBAR_COLOR);
  #ifdef HAS_FULL_SCREEN
    #ifndef HAS_PSRAM
      display_obj.tft.drawString("D:" + String(getDRAMUsagePercent()) + "%", SB_MEM_X, 0, 2);
    #else
      display_obj.tft.drawString("D:" + String(getDRAMUsagePercent()) + "%", SB_MEM_X, 0, 1);
      display_obj.tft.drawString("P:" + String(getPSRAMUsagePercent()) + "%", SB_MEM_X, 8, 1);
    #endif
  #endif

  #ifdef HAS_MINI_SCREEN
    display_obj.tft.drawString(String(getDRAMUsagePercent()) + "%", TFT_WIDTH/1.75, 0, 1);
  #endif


  MenuFunctions::battery(true);
  display_obj.tft.fillRect(186, 0, 16, STATUS_BAR_WIDTH, STATUSBAR_COLOR);


  // Disable touch stuff
  #ifdef HAS_ILI9341
    #ifdef HAS_BUTTONS
      if (this->disable_touch) {
        display_obj.tft.setCursor(0, 1);
        display_obj.tft.drawXBitmap(SB_TOUCH_X,
                                    0,
                                    menu_icons[DISABLE_TOUCH],
                                    16,
                                    16,
                                    STATUSBAR_COLOR,
                                    TFT_RED);
      }
      else {
        display_obj.tft.setCursor(0, 1);
        display_obj.tft.drawXBitmap(SB_TOUCH_X,
                                    0,
                                    menu_icons[DISABLE_TOUCH],
                                    16,
                                    16,
                                    STATUSBAR_COLOR,
                                    TFT_DARKGREY);
      }
    #endif
  #endif

  // Draw SD info
  #ifdef HAS_SD
    if (sd_obj.supported)
      the_color = TFT_GREEN;
    else
      the_color = TFT_RED;
  

    #ifdef HAS_FULL_SCREEN
      display_obj.tft.drawXBitmap(SB_SD_X,
                                  0,
                                  menu_icons[STATUS_SD],
                                  16,
                                  16,
                                  STATUSBAR_COLOR,
                                  the_color);
    #endif
  #endif

  #ifdef HAS_MINI_SCREEN
    display_obj.tft.setTextColor(the_color, STATUSBAR_COLOR);
    display_obj.tft.drawString("SD", TFT_WIDTH - 12, 0, 1);
  #endif

  // WiFi connection status stuff
  if (wifi_scan_obj.wifi_connected) {
    #ifdef HAS_FULL_SCREEN
      display_obj.tft.drawXBitmap(SB_WIFI_X,
                                  0,
                                  menu_icons[JOINED],
                                  16,
                                  16,
                                  STATUSBAR_COLOR,
                                  TFT_GREEN);
    #endif
  } else {
    #ifdef HAS_FULL_SCREEN
      display_obj.tft.drawXBitmap(SB_WIFI_X,
                                  0,
                                  menu_icons[JOINED],
                                  16,
                                  16,
                                  STATUSBAR_COLOR,
                                  TFT_DARKGREY);
    #endif
  }

  // Force PMKID stuff
  if ((wifi_scan_obj.force_pmkid) || (wifi_scan_obj.ep_deauth)) {
    #ifdef HAS_FULL_SCREEN
      display_obj.tft.drawXBitmap(SB_FORCE_X,
                                  0,
                                  menu_icons[FORCE],
                                  16,
                                  16,
                                  STATUSBAR_COLOR,
                                  TFT_GREEN);
    #endif
  } else {
    #ifdef HAS_FULL_SCREEN
      display_obj.tft.drawXBitmap(SB_FORCE_X,
                                  0,
                                  menu_icons[FORCE],
                                  16,
                                  16,
                                  STATUSBAR_COLOR,
                                  TFT_DARKGREY);
    #endif
  }
}

void MenuFunctions::orientDisplay() {
  display_obj.init();

  display_obj.tft.setRotation(SCREEN_ORIENTATION); // Portrait

  display_obj.tft.setCursor(0, 0);

  #ifdef HAS_ILI9341
    #ifndef HAS_CYD_TOUCH
      display_obj.setCalData();
    #else
      display_obj.touchscreen.setRotation(0);
    #endif
  #endif

  changeMenu(current_menu, true);
}

const char* MenuFunctions::callSetting(const char* key) {
  specSettingMenu.name = key;

  const char* setting_type = settings_obj.getSettingType(key);

  if (setting_type && strcmp(setting_type, "bool") == 0) {
    return "bool";
  }

  return "";
}

/*void MenuFunctions::displaySetting(String key, Menu* menu, int index) {
  specSettingMenu.name = key;

  bool setting_value = settings_obj.loadSetting<bool>(key);

  // Make a local copy of menu node
  MenuNode node = menu->list->get(index);

  display_obj.tft.setTextWrap(false);
  display_obj.tft.setFreeFont(NULL);
  display_obj.tft.setCursor(0, 100);
  display_obj.tft.setTextSize(1);

  // Set local copy value
  if (!setting_value) {
    display_obj.tft.setTextColor(TFT_RED);
    display_obj.tft.println(F(text_table1[4]));
    node.selected = false;
  }
  else {
    display_obj.tft.setTextColor(TFT_GREEN);
    display_obj.tft.println(F(text_table1[5]));
    node.selected = true;
  }

  // Put local copy back into menu
  menu->list->set(index, node);
    
}*/

void MenuFunctions::displaySetting(const char* key, Menu* menu, int index) {
  specSettingMenu.name = String(key);

  bool setting_value = settings_obj.loadSetting<bool>(key);

  // Make a local copy of menu node
  MenuNode node = menu->list->get(index);

  display_obj.tft.setTextWrap(false);
  display_obj.tft.setFreeFont(NULL);
  display_obj.tft.setCursor(0, 100);
  display_obj.tft.setTextSize(1);

  // Set local copy value
  if (!setting_value) {
    display_obj.tft.setTextColor(TFT_RED);
    display_obj.tft.println(F(text_table1[4]));
    node.selected = false;
  } else {
    display_obj.tft.setTextColor(TFT_GREEN);
    display_obj.tft.println(F(text_table1[5]));
    node.selected = true;
  }

  // Put local copy back into menu
  menu->list->set(index, node);
}

#if defined(MARAUDER_CARDPUTER) || defined(MARAUDER_CARDPUTER_ADV)
void MenuFunctions::updateKeyboard()
{
  M5CardputerKeyboard.updateKeyList();
  M5CardputerKeyboard.updateKeysState();
}

bool MenuFunctions::isKeyPressed(char c)
{
  bool pressed = M5CardputerKeyboard.isKeyPressed(c);

  if (pressed)
    delay(200);

  return pressed;
}
#endif

#ifdef HAS_DIRECT_UPLOAD
  void MenuFunctions::buildUploadFileMenu() {
    if (sd_obj.supported) {
      this->setupSDFileList();

      uploadLogsMenu.list->clear();
      delete uploadLogsMenu.list;
      uploadLogsMenu.list = new LinkedList<MenuNode>();
      uploadLogsMenu.name = "Logs";

      uploadLogsMenu.parentMenu = &wifiGeneralMenu;

      this->addNodes(&uploadLogsMenu, "Back", TFTLIGHTGREY, 0, [this]() {
        this->changeMenu(uploadLogsMenu.parentMenu, true);
      });

      this->addNodes(&uploadLogsMenu, "Delete Wardrive Logs", TFTORANGE, 0, [this]() {
        this->changeMenu(&deleteAllMenu, true);
      });

      this->addNodes(&uploadLogsMenu, "Upload All", TFTGREEN, 0, [this]() {
        this->changeMenu(&uploadAllMenu, true);
        
      });

      for (int i = 0; i < sd_obj.sd_files->size(); i++) {
        File current_file = sd_obj.getFile("/" + sd_obj.sd_files->get(i));
        if (sd_obj.sd_files->get(i).startsWith("wardrive_") || sd_obj.sd_files->get(i).startsWith("wigle-")) {
          if (!sd_obj.sd_files->get(i).endsWith(".wdg") && !sd_obj.sd_files->get(i).endsWith(".wigle") && !sd_obj.sd_files->get(i).endsWith(".gpx")) {
            this->addNodes(&uploadLogsMenu, sd_obj.sd_files->get(i).c_str(), TFTCYAN, 0, [this, i]() {
              sd_obj.selected_file_name = sd_obj.sd_files->get(i);
              Serial.println(sd_obj.sd_files->get(i) + " selected");
              this->changeMenu(&actionMenu, true);
            });
          }
        }
      }

      Serial.println("Built SD file menu with " + (String)sd_obj.sd_files->size() + " files");
    } else {
      Serial.println("SD Card not detected. Skipping menu creation...");
    }
  }
#endif

const char* MenuFunctions::foxSortLabel() const {
  switch (fox_sort_mode) {
    case TargetSortMode::SIGNAL_DESC: return "Signal v";
    case TargetSortMode::NAME_ASC: return "Name A-Z";
    case TargetSortMode::CHANNEL_ASC: return "Channel 1-177";
  }
  return "Signal v";
}

const char* MenuFunctions::foxFilterLabel() const {
  switch (fox_filter_mode) {
    case TargetFilterMode::ALL: return "All";
    case TargetFilterMode::RECENT_30S: return "Seen <30s";
    case TargetFilterMode::BAND_24_GHZ: return "2.4 GHz";
    case TargetFilterMode::BAND_5_GHZ: return "5 GHz";
  }
  return "All";
}

bool MenuFunctions::foxListSupportsRecent() const {
  return fox_target_list == FoxHuntListKind::AP_TARGETS ||
         fox_target_list == FoxHuntListKind::APS_WITH_STATIONS ||
         fox_target_list == FoxHuntListKind::FINDMY_TARGETS;
}

bool MenuFunctions::foxListSupportsBand() const {
  return fox_target_list == FoxHuntListKind::AP_TARGETS ||
         fox_target_list == FoxHuntListKind::APS_WITH_STATIONS ||
         fox_target_list == FoxHuntListKind::STATION_TARGETS ||
         fox_target_list == FoxHuntListKind::PINEAPPLE_TARGETS ||
         fox_target_list == FoxHuntListKind::MULTISSID_TARGETS;
}

void MenuFunctions::buildFoxSortMenu() {
  foxSortMenu.list->clear();
  foxSortMenu.parentMenu = current_menu;
  this->addNodes(&foxSortMenu, text09, TFTLIGHTGREY, 0, [this]() { this->changeMenu(foxSortMenu.parentMenu, true); });
  this->addNodes(&foxSortMenu, "Signal: Strongest", TFTCYAN, 255, [this]() {
    fox_sort_mode = TargetSortMode::SIGNAL_DESC;
    buildFoxTargetList(fox_target_list, fox_target_context_ap);
  });
  this->addNodes(&foxSortMenu, "Name/MAC: A-Z", TFTCYAN, 255, [this]() {
    fox_sort_mode = TargetSortMode::NAME_ASC;
    buildFoxTargetList(fox_target_list, fox_target_context_ap);
  });
  if (foxListSupportsBand()) {
    this->addNodes(&foxSortMenu, "Channel: Low-High", TFTCYAN, 255, [this]() {
      fox_sort_mode = TargetSortMode::CHANNEL_ASC;
      buildFoxTargetList(fox_target_list, fox_target_context_ap);
    });
  }
  this->changeMenu(&foxSortMenu, true);
}

void MenuFunctions::buildFoxFilterMenu() {
  foxFilterMenu.list->clear();
  foxFilterMenu.parentMenu = current_menu;
  this->addNodes(&foxFilterMenu, text09, TFTLIGHTGREY, 0, [this]() { this->changeMenu(foxFilterMenu.parentMenu, true); });
  this->addNodes(&foxFilterMenu, "All", TFTGREEN, 255, [this]() {
    fox_filter_mode = TargetFilterMode::ALL;
    buildFoxTargetList(fox_target_list, fox_target_context_ap);
  });
  if (foxListSupportsRecent()) {
    this->addNodes(&foxFilterMenu, "Seen in 30 Seconds", TFTGREEN, 255, [this]() {
      fox_filter_mode = TargetFilterMode::RECENT_30S;
      buildFoxTargetList(fox_target_list, fox_target_context_ap);
    });
  }
  if (foxListSupportsBand()) {
    this->addNodes(&foxFilterMenu, "2.4 GHz", TFTGREEN, 255, [this]() {
      fox_filter_mode = TargetFilterMode::BAND_24_GHZ;
      buildFoxTargetList(fox_target_list, fox_target_context_ap);
    });
    #ifdef HAS_DUAL_BAND
      this->addNodes(&foxFilterMenu, "5 GHz", TFTGREEN, 255, [this]() {
        fox_filter_mode = TargetFilterMode::BAND_5_GHZ;
        buildFoxTargetList(fox_target_list, fox_target_context_ap);
      });
    #endif
  }
  this->changeMenu(&foxFilterMenu, true);
}

void MenuFunctions::buildFoxTargetList(FoxHuntListKind type, int context_ap) {
  fox_target_list = type;
  fox_target_context_ap = context_ap;
  if (!foxListSupportsRecent() && fox_filter_mode == TargetFilterMode::RECENT_30S)
    fox_filter_mode = TargetFilterMode::ALL;
  if (!foxListSupportsBand() && (fox_filter_mode == TargetFilterMode::BAND_24_GHZ || fox_filter_mode == TargetFilterMode::BAND_5_GHZ))
    fox_filter_mode = TargetFilterMode::ALL;
  if (!foxListSupportsBand() && fox_sort_mode == TargetSortMode::CHANNEL_ASC)
    fox_sort_mode = TargetSortMode::SIGNAL_DESC;

  Menu* menu = type == FoxHuntListKind::STATION_TARGETS ? &wifiStationMenu : &wifiAPMenu;
  menu->list->clear();
  menu->parentMenu = type == FoxHuntListKind::STATION_TARGETS ? &wifiAPMenu : &foxHuntMenu;
  this->addNodes(menu, text09, TFTLIGHTGREY, 0, [this, menu]() { this->changeMenu(menu->parentMenu, true); });
  String sort_row = "Sort: " + String(foxSortLabel());
  this->addNodes(menu, sort_row.c_str(), TFTCYAN, 255, [this]() { buildFoxSortMenu(); });
  String filter_row = "Filter: " + String(foxFilterLabel());
  this->addNodes(menu, filter_row.c_str(), TFTGREEN, 255, [this]() { buildFoxFilterMenu(); });
  this->addNodes(menu, "Refresh List", TFTYELLOW, 255, [this]() { buildFoxTargetList(fox_target_list, fox_target_context_ap); });

  std::vector<TargetListItem> items;
  auto add_item = [&items](size_t index, int16_t rssi, uint8_t channel, uint32_t last_seen, const String& name) {
    TargetListItem item = {index, rssi, channel, last_seen, {}};
    strncpy(item.name, name.c_str(), sizeof(item.name) - 1);
    items.push_back(item);
  };

  if (type == FoxHuntListKind::AP_TARGETS || type == FoxHuntListKind::APS_WITH_STATIONS) {
    for (int i = 0; i < access_points->size(); i++) {
      const AccessPoint& ap = access_points->get(i);
      if (type == FoxHuntListKind::APS_WITH_STATIONS && ap.stations->size() == 0)
        continue;
      add_item(i, ap.rssi, ap.channel, ap.last_seen_ms, ap.essid.length() ? ap.essid : macToString(ap.bssid));
    }
  } else if (type == FoxHuntListKind::STATION_TARGETS && context_ap >= 0 && context_ap < access_points->size()) {
    const AccessPoint& ap = access_points->get(context_ap);
    for (int x = 0; x < ap.stations->size(); x++) {
      int station_index = ap.stations->get(x);
      add_item(station_index, -128, ap.channel, 0, macToString(stations->get(station_index).mac));
    }
  } else if (type == FoxHuntListKind::PINEAPPLE_TARGETS) {
    for (size_t i = 0; i < wifi_scan_obj.getPineScanCount(); i++)
      add_item(i, wifi_scan_obj.getPineScanRssi(i), wifi_scan_obj.getPineScanChannel(i), 0, wifi_scan_obj.getPineScanLabel(i));
  } else if (type == FoxHuntListKind::MULTISSID_TARGETS) {
    for (size_t i = 0; i < wifi_scan_obj.getMultiSSIDCount(); i++)
      add_item(i, wifi_scan_obj.getMultiSSIDRssi(i), wifi_scan_obj.getMultiSSIDChannel(i), 0, wifi_scan_obj.getMultiSSIDLabel(i));
  } else if (type == FoxHuntListKind::BLE_TARGETS) {
    for (int i = 0; i < ble_devices->size(); i++)
      add_item(i, ble_devices->get(i).rssi, 0, 0, ble_devices->get(i).name.length() ? ble_devices->get(i).name : macToString(ble_devices->get(i).mac));
  } else if (type == FoxHuntListKind::FINDMY_TARGETS) {
    for (int i = 0; i < airtags->size(); i++)
      add_item(i, airtags->get(i).rssi, 0, airtags->get(i).last_seen, airtags->get(i).mac);
  } else if (type == FoxHuntListKind::FLIPPER_TARGETS) {
    for (int i = 0; i < flippers->size(); i++)
      add_item(i, flippers->get(i).rssi, 0, flippers->get(i).last_seen,
               flippers->get(i).name.length() ? flippers->get(i).name : flippers->get(i).mac);
  } else if (type == FoxHuntListKind::META_TARGETS || type == FoxHuntListKind::FLOCK_TARGETS) {
    const String device_type = type == FoxHuntListKind::META_TARGETS ? "Meta" : "Flock";
    for (int i = 0; i < ble_devices->size(); i++) {
      const BleDevice& device = ble_devices->get(i);
      if (device.device_type == device_type)
        add_item(i, device.rssi, 0, device.last_seen_ms,
                 device.name.length() ? device.name : macToString(device.mac));
    }
  }

  std::vector<TargetListItem> filtered;
  uint32_t now = millis();
  for (const TargetListItem& item : items) {
    if (targetListItemMatchesFilter(item, fox_filter_mode, now))
      filtered.push_back(item);
  }
  sortTargetList(filtered, fox_sort_mode);

  for (const TargetListItem& item : filtered) {
    int index = item.source_index;
    String label;
    uint16_t color = TFTCYAN;
    if (type == FoxHuntListKind::AP_TARGETS) {
      const AccessPoint& ap = access_points->get(index);
      label = String(ap.rssi) + " " + ap.essid;
      color = rssiToMenuColor(ap.rssi);
    } else if (type == FoxHuntListKind::APS_WITH_STATIONS) {
      const AccessPoint& ap = access_points->get(index);
      label = ap.essid + " (" + String(ap.stations->size()) + ")";
      color = TFTMAGENTA;
    } else if (type == FoxHuntListKind::STATION_TARGETS) {
      label = macToString(stations->get(index).mac);
      color = TFTMAGENTA;
    } else if (type == FoxHuntListKind::PINEAPPLE_TARGETS) {
      label = wifi_scan_obj.getPineScanLabel(index);
      color = TFTYELLOW;
    } else if (type == FoxHuntListKind::MULTISSID_TARGETS) {
      label = wifi_scan_obj.getMultiSSIDLabel(index);
      color = TFTORANGE;
    } else if (type == FoxHuntListKind::BLE_TARGETS) {
      label = String(ble_devices->get(index).rssi) + " " + ble_devices->get(index).name;
      color = rssiToMenuColor(ble_devices->get(index).rssi);
    } else if (type == FoxHuntListKind::FINDMY_TARGETS) {
      label = String(airtags->get(index).rssi) + " " + airtags->get(index).mac;
      color = TFTWHITE;
    } else if (type == FoxHuntListKind::FLIPPER_TARGETS) {
      label = flippers->get(index).name.length() ? flippers->get(index).name : flippers->get(index).mac;
      color = TFTORANGE;
    } else {
      const BleDevice& device = ble_devices->get(index);
      label = String(device.rssi) + " " + (device.name.length() ? device.name : macToString(device.mac));
      color = type == FoxHuntListKind::META_TARGETS ? TFTWHITE : TFTORANGE;
    }

    this->addNodes(menu, label.c_str(), color, 255, [this, type, context_ap, index]() {
      if (type == FoxHuntListKind::APS_WITH_STATIONS) {
        buildFoxTargetList(FoxHuntListKind::STATION_TARGETS, index);
        return;
      }
      if (type == FoxHuntListKind::PINEAPPLE_TARGETS) {
        if (!wifi_scan_obj.selectPineScanFoxTarget(index)) return;
      } else if (type == FoxHuntListKind::MULTISSID_TARGETS) {
        if (!wifi_scan_obj.selectMultiSSIDFoxTarget(index)) return;
      } else if (type == FoxHuntListKind::AP_TARGETS) {
        const AccessPoint& ap = access_points->get(index);
        wifi_scan_obj.setFoxHuntTarget(ap.bssid, ap.essid, ap.rssi, ap.channel, false);
      } else if (type == FoxHuntListKind::STATION_TARGETS) {
        const AccessPoint& ap = access_points->get(context_ap);
        const Station& station = stations->get(index);
        wifi_scan_obj.setFoxHuntTarget(station.mac, macToString(station.mac), -128, ap.channel, false);
      } else if (type == FoxHuntListKind::BLE_TARGETS) {
        const BleDevice& device = ble_devices->get(index);
        wifi_scan_obj.setFoxHuntTarget(device.mac, device.name, device.rssi, 0, true, macToString(device.mac));
      } else if (type == FoxHuntListKind::FINDMY_TARGETS) {
        uint8_t mac[6];
        convertMacStringToUint8(airtags->get(index).mac, mac);
        wifi_scan_obj.setFoxHuntTarget(mac, airtags->get(index).mac, airtags->get(index).rssi, 0, true, airtags->get(index).mac);
      } else if (type == FoxHuntListKind::FLIPPER_TARGETS) {
        uint8_t mac[6];
        convertMacStringToUint8(flippers->get(index).mac, mac);
        String name = flippers->get(index).name.length() ? flippers->get(index).name : flippers->get(index).mac;
        wifi_scan_obj.setFoxHuntTarget(mac, name, flippers->get(index).rssi, 0, true, flippers->get(index).mac);
      } else if (type == FoxHuntListKind::META_TARGETS || type == FoxHuntListKind::FLOCK_TARGETS) {
        const BleDevice& device = ble_devices->get(index);
        wifi_scan_obj.setFoxHuntTarget(device.mac, device.name, device.rssi, 0, true, macToString(device.mac));
      }
      display_obj.clearScreen();
      this->drawStatusBar();
      wifi_scan_obj.StartScan(type == FoxHuntListKind::BLE_TARGETS ||
                              type == FoxHuntListKind::FINDMY_TARGETS ||
                              type == FoxHuntListKind::FLIPPER_TARGETS ||
                              type == FoxHuntListKind::META_TARGETS ||
                              type == FoxHuntListKind::FLOCK_TARGETS
                                ? BT_SCAN_FOX_HUNT : WIFI_SCAN_SIG_STREN, TFT_CYAN);
    });
  }
  this->changeMenu(menu, true);
}

void MenuFunctions::buildWiFiFoxHuntMenu() {
  foxHuntMenu.list->clear();
  foxHuntMenu.parentMenu = &wifiSnifferMenu;
  this->addNodes(&foxHuntMenu, text09, TFTLIGHTGREY, 0, [this]() { this->changeMenu(foxHuntMenu.parentMenu, true); });
  this->addNodes(&foxHuntMenu, "APs", TFTLIME, WIFI, [this]() { buildFoxTargetList(FoxHuntListKind::AP_TARGETS); });
  this->addNodes(&foxHuntMenu, "Stations", TFTMAGENTA, WIFI, [this]() { buildFoxTargetList(FoxHuntListKind::APS_WITH_STATIONS); });
  this->addNodes(&foxHuntMenu, "WiFi Pineapples", TFTYELLOW, PINESCAN_SNIFF, [this]() { buildFoxTargetList(FoxHuntListKind::PINEAPPLE_TARGETS); });
  this->addNodes(&foxHuntMenu, "MultiSSID", TFTORANGE, MULTISSID_SNIFF, [this]() { buildFoxTargetList(FoxHuntListKind::MULTISSID_TARGETS); });
  this->changeMenu(&foxHuntMenu, true);
}

void MenuFunctions::buildBluetoothFoxHuntMenu() {
  foxHuntMenu.list->clear();
  foxHuntMenu.parentMenu = &bluetoothSnifferMenu;
  this->addNodes(&foxHuntMenu, text09, TFTLIGHTGREY, 0, [this]() { this->changeMenu(foxHuntMenu.parentMenu, true); });
  this->addNodes(&foxHuntMenu, "BLE Devices", TFTCYAN, BLUETOOTH, [this]() { buildFoxTargetList(FoxHuntListKind::BLE_TARGETS); });
  this->addNodes(&foxHuntMenu, "FindMy", TFTWHITE, BLUETOOTH, [this]() { buildFoxTargetList(FoxHuntListKind::FINDMY_TARGETS); });
  this->addNodes(&foxHuntMenu, "Flipper Zero", TFTORANGE, FLIPPER, [this]() { buildFoxTargetList(FoxHuntListKind::FLIPPER_TARGETS); });
  this->addNodes(&foxHuntMenu, "Meta", TFTWHITE, BLUETOOTH, [this]() { buildFoxTargetList(FoxHuntListKind::META_TARGETS); });
  this->addNodes(&foxHuntMenu, "Flock", TFTORANGE, FLOCK, [this]() { buildFoxTargetList(FoxHuntListKind::FLOCK_TARGETS); });
  this->changeMenu(&foxHuntMenu, true);
}
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
